brickbots/PiFinder/docs/source/index.rst

PiFinder™ Welcome
==================
A plate solving telescope finder based around a Raspberry PI, Camera, and custom UI 'hat'

For an overview of what the PiFinder is and how it came to be visit the official project website at `PiFinder.io <https://www.pifinder.io/>`_

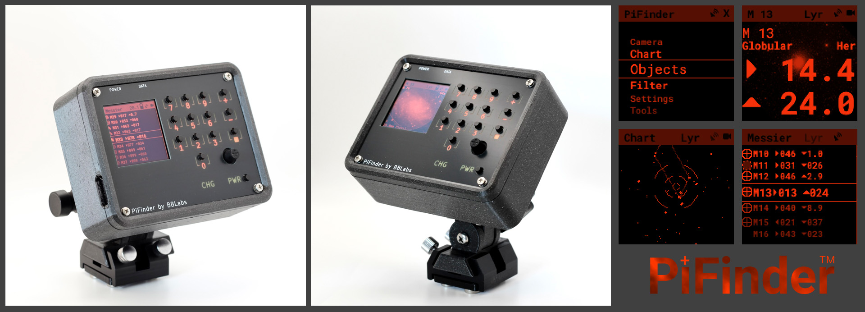
[picture p70: docs/source/images/PiFinder_rev4_banner.jpg]


.. note::
   This documentation covers rev4, v3 and v2.5 PiFinders running software |min_software| or
   above.  Not sure which you have?  See
   :ref:`Which PiFinder do I have? <quick_start:which pifinder do i have?>` in the Quick
   Start.

   Pages describe rev4 and note the v3 and v2.5 differences underneath.  |v3_docs|

   If you need docs for a previous version please choose `1.x.x <https://pifinder.readthedocs.io/en/v1.11.2/index.html>`_
   , `2.0.x <https://pifinder.readthedocs.io/en/v2.0.4/index.html>`_
   or `2.1.x <https://pifinder.readthedocs.io/en/v2.1.1/index.html>`_

* If you are new to the PiFinder, you probably want the :doc:`quick_start`
* Want to build your own?  Check out the :doc:`build_guide`
* Just bought and upgrade kit for your v2 PiFinder?  Here's the :doc:`v25_upgrade`

About
-------

The PiFinder is my attempt to improve my time at my telescope.  I don't get nearly enough of it and I want to enjoy it as much as possible.  So after years of observing with paper charts and, later, a Nexus DSC here is what I felt I was missing:

* **Reliable telescope positioning:**  The Nexus DSC is great, but my telescope just isn't built for solid encoder integration.  The slop in the way I have to couple the encoders means poor pointing accuracy.
* **Easy setup:**  The Nexus DSC needs multi-star alignment to understand how the encoders map to the sky.  The process is not terrible, but I'd like to avoid it.
* **Good push-to functionality**:  This is one place the Nexus DSC shines... if it's well aligned.  The catalog system is okay, and once you select and object the screen is clear and helpful to get the telescope pointed correctly.
* **Observation logging**:  I like to keep track of what I see each night.  I don't often sketch, just record what I saw when, with what eyepiece and some basic info about the experience.  If I could do this right at the eyepiece, that'd save time.

My hope is that other people will find this combination of functionality useful, will build their own PiFinder and help the whole project improve by making suggestions and potentially contributing to the software.  It's a pretty easy build with off the shelf parts and beginner friendly soldering.  

Features
--------

* Zero setup: Just turn it on and point it at the sky!  
* Accurate pointing: Onboard GPS determines location and time while the camera determines where the telescope is pointing.  Inertial Measurement Unit tracks telescope motion and updates sky position between camera solves
* Self-contained:  Includes catalog search/filtering, sky/object charting, push-to guidance and logging all via the screen and keypad on the unit.
* Dark site friendly:  Red OLED screen and soft backlit keys have wide brightness adjustment, right down to 'off'. No need for bright cell phones or tablets
* Easy access: Can be mounted by the eyepiece just like a finder.
* Wifi Access Point / SkySafari Integration:  The PiFinder can act as a WIFI access point to connect your tablet or phone to sync SkySafari or other planetarium software with your telescope.

Build Your Own
--------------
The PiFinder is fully open-source hardware and software.  You can order PCB's and 3d print the case with the files in this repo and order all the parts from the :doc:`Parts List <BOM>`

If you would like pre-assembled units, kits or other items to jump start your PiFinder journey, visit `PiFinder.io <https://www.pifinder.io/>`_ to see what's available and place an order.



If you'd like to learn more about how it works, and potentially build your own, everything you need should be here.  I recommend starting with the :doc:`User Manual <user_guide>` and then checking out the :doc:`Build Guide <build_guide>`.

Discord
-------
Join the `PiFinder Discord server <https://discord.gg/Nk5fHcAtWD>`_ for support with your build, usage questions, and suggestions for improvement.

.. toctree::
   :hidden:
   :maxdepth: 2

   self

.. toctree::
   :hidden:
   :maxdepth: 2
   :caption: Using your PiFinder

   quick_start
   user_guide
   menu_map
   equipment
   sqm
   catalogs
   connectivity
   skysafari
   troubleshooting

.. toctree::
   :hidden:
   :maxdepth: 2
   :caption: Building & upgrading

   build_guide
   BOM
   software
   sd_card
   v25_upgrade

.. toctree::
   :hidden:
   :maxdepth: 2
   :caption: For developers

   dev_guide
   dev_arch
   api
