brickbots/PiFinder/case/adapters/dovetail_meade_lxd.md

## PiFinder Dovetail for Meade LXD shoe

Contributed by: John Purdy

This part replaces the bottom half of the standard Vixen/Synta foot
shoe with a profile that mates with the Meade LXD shoe.  
Print with bottom of the dovetail on the plate, may require supports for side profile overhangs.
