brickbots/PiFinder/docs/ax/sqm/CONTEXT.md

# SQM (Sky Quality Meter)

Canonical language for PiFinder's solve-independent sky-brightness measurement.
The architecture and validation evidence live in [`../sqm.md`](../sqm.md).

## Product intent

**Zero-touch SQM**:
Normal operation selects the built-in profile from the detected sensor and
starts measuring without flats, darks, or a calibration file. Optional Correct
and Calibration flows refine a unit or session; they do not establish basic
functionality.

**SQM**:
The published PiFinder sky surface brightness in mag/arcsec². Higher means a
darker sky. It is empirically calibrated to an SQM-L scale but is not claimed
to have an identical spectral or angular response.

**`SQMState`**:
Latest published `value`, `source`, and `last_update` in shared state. The UI
reads this state and does not calculate photometry.

**Radiometric SQM**:
The published factory-calibration measurement from diffuse raw background,
exposure, pedestal, factory field width, and the effective radiometric zero
point. On bare sensors that zero point is not a constant — it moves with
measured **sky colour** (see *Radiometric colour term*). Avoid calling it the
"fixed-calibration" value; the calibration is fixed per sensor, the zero point
applied to a given frame is not.

**Stellar SQM (`sqm_star_calibrated`)**:
The former per-frame stellar-zero-point result. Retained as a transmission and
regression diagnostic; never the production primary or no-solve fallback.

**`sqm_altitude_corrected`**:
Optional comparison value `sqm_final + 0.28 × (airmass − 1)`. It is present
only when a real field altitude is known. It is never the primary reading.

## Images and coordinates

**Solve image**:
The processed 512×512 image used by Cedar and tetra3. It can be display-rotated.

**Raw photometry image**:
The linear cropped raw mono frame, or the mean of both Bayer-green sites. Star
flux and sky background are measured here, not on the processed solve image.
Always the **crop**, never the full-sensor frame that exposure sweeps archive —
see [Camera](../camera/CONTEXT.md) for the two extents. The margins are
vignetted with no optical black, so measuring them would bias the sky
background and break continuity with every calibrated sweep.

**Derotation**:
Mapping solve-image `(y, x)` centroids back to the orientation of the stored
raw frame using `solve_image_rotation`. Required before raw photometry.

**Centroid scale**:
Raw-photometry side length divided by 512. Both matched and all-detected
centroids must be scaled by it before use on the raw image.

## Stellar photometry

**Aperture**:
Circular radius-5-pixel region whose sky-subtracted sum is stellar flux.

**Annulus**:
The local sky ring from radius 10 through 18 pixels. Radius 10 is wing-safe on
the archive; the former 6–14 ring was contaminated by HQ PSF wings.

**Detected-source exclusion**:
Every Cedar centroid is masked out of every relevant annulus with an
aperture-radius disk. A 3σ clip catches unreported sources.

**Saturation threshold**:
`0.70 × (2^bit_depth − 1)` on raw photometry. The conservative limit rejects
stars in the sensor's nonlinear shoulder before hard clipping.

**Reference magnitude**:
Bare sensors use Gaia G with a BP−RP trim. HQ uses Hipparcos/Johnson V because
its factory IR-cut passband is closer to V. Missing Gaia data falls back to V.

**Fixed magnitude band**:
Catalog magnitudes 3.5–6.5. When at least five stars are available, only this
population votes on the frame zero point, preventing exposure-dependent
population drift.

**Photometric zero point (`mzero`)**:
Median of `reference_mag + 2.5 log10(star_flux)` over the selected population,
after a 3-MAD outlier rejection. Readings outside the fixed magnitude band do
not vote merely because a longer exposure detects them.

**MAD rejection**:
Three robust standard deviations (`1.4826 × MAD`) around the selected
population's median. Removes isolated catalog, colour, blend, or residual
nonlinearity failures; it does not replace the magnitude band.

**Wing correction (`mzero_correction`)**:
Rolling additive `−2.5 log10(f)`, where `f` is the aperture's enclosed stellar
flux fraction measured from a median-stacked curve of growth.

**`WingEstimator`**:
Conditions on several frames of bright unsaturated stars. Returns zero before
conditioning and naturally converges to zero for wingless optics. Do not
replace it with a per-star wing-boundary search; that approach integrated sky
noise and invented missing flux.

## Sky and detector model

**Local sky**:
Median cleaned annulus value for one matched star.

**Radiometer sample**:
Sparse central median reduced in the camera process on every raw frame. It
excludes the outer ten percent and records MAD, quadrant gradient, exposure,
timestamp, sequence, and native green/mono pixel scale.

**Stellar sky background**:
Median of local annulus skies, used only by stellar diagnostics.

**Bias offset**:
Static mean detector signal at minimum exposure, in raw ADU. Comes from the
built-in sensor profile unless an optional per-device calibration overrides it.
Static is the operative word: it is a stored constant, and a **tracked black
level** supersedes it when one is available.

**Tracked black level (`BlackLevelTracker`)**:
The sensor's actual pedestal right now, fitted as the intercept of sky
background against exposure over the running session. The optical-black clamp
moves with sensor state, so this measurement supersedes both the profile
constant and any wizard-measured bias offset once its fit is **leased**. It
needs no lens cap and no dark frame. Say "tracked black level", not "auto
bias" or "dynamic calibration" — it measures one specific quantity and does
not calibrate anything else. See
[ADR 0028](../../adr/0028-tracked-black-level-supersedes-stored-bias.md).

**Lease**:
The gate that decides whether a tracked black level is trusted enough to
publish, based on the fit's standard error and deviation band. Unleased, the
pedestal falls back to the stored constant. A tracker holding samples is not
the same as a tracker whose fit is leased.

**Mean dark signal**:
`calibrated_dark_current_rate × exposure_seconds`. A mean exposure-dependent
signal, not an RMS noise term. Factory profile rates are unverified engineering
estimates and remain diagnostic until optional per-device calibration measures
the rate.

**Pedestal**:
The mean detector signal subtracted from sky background. Its bias term is the
**tracked black level** when one is leased, otherwise `bias_offset`. An
optional measured calibration adds `mean_dark_signal` on top of that bias term.
An explicit total `pedestal_override` wins over all of it.

**Read noise**:
Zero-mean RMS variation in raw ADU. Diagnostic uncertainty; never subtracted
from sky signal.

**Unresolved background**:
Sky background no more than 1 ADU above the pedestal. SQM returns no new value
with `background_not_resolved_above_pedestal`; it does not clamp.

**`NoiseFloorEstimator`**:
Owner of one copied, optionally calibrated camera profile. Reports
the applied `pedestal + read_noise` as a raw-ADU operational threshold and
retains low image percentiles and the unapplied factory dark-current model only
for diagnostics. It cannot infer a dark calibration from ordinary sky images.

**Shared camera noise floor**:
The camera's exposure controller operates on processed 8-bit pixels. A raw-ADU
SQM threshold must not be published into it; the units differ.

**`CameraProfile`**:
Per-sensor hardware, detector, catalog-band, colour, and SQM offset constants.
`get_camera_profile()` returns a copy so optional calibration never mutates
global defaults or another calculator.

**Radiometric zero point**:
Exposure-normalized diffuse-sky conversion already mapped to the SQM-L scale.
It is fixed per shipped sensor/optics profile and does not change with current
stellar transmission.

**Radiometric field width**:
Angular width used for square-arcsecond conversion when no solve exists.
Derived from the **optical train** (see [Camera](../camera/CONTEXT.md)) rather
than stored per sensor: it is a property of the sensor *and* the fitted lens,
so a sensor-only constant is silently wrong the moment the lens changes. An
error here scales the assumed solid angle, and so biases every published
radiometric SQM — a lens change of one step is worth ~0.6 mag.
_Avoid_: factory field width (it is no longer a factory constant), FOV
(unqualified — see [Camera](../camera/CONTEXT.md)).

## Passband and atmosphere

**Colour coefficient**:
Per-sensor trim mapping catalog colour into the camera's stellar passband.

**SQM band offset (`sqm_band_offset`)**:
Additive mapping from sensor-band sky brightness to the reference SQM-L scale
for the calibrated sky regime, on the **stellar** path only. It is coupled to
the catalog transform, wing model, and local-annulus background estimator.
Diagnostic: the published value comes from the radiometer, not from here.

**Sky colour (`R/G`)**:
Ratio of median red to median green sky background, measured off the raw
mosaic. A *measurement of the scene*, not a sensor property — it is the
project's proxy for sky spectrum, and the thing that distinguishes a
sodium/LED-dominated light-polluted sky (green-weighted, R/G ≈ 0.83–0.89) from
a dark airglow sky (grey and NIR-rich, R/G ≈ 1.00–1.04). Say "sky colour" or
"R/G", not "colour temperature" or "white balance" — neither is what this is.

**Radiometric colour term (`radiometric_colour_slope` / `_pivot` / `_range`)**:
Sky-colour dependence of the radiometric zero point, in mag per unit R/G. It
exists because the sensor-band to V-band conversion depends on the sky's
spectrum, which a single constant cannot represent across regimes. Slope `0`
means a plain constant, which is correct for mono sensors and for IR-cut
sensors with no NIR leak. R/G is clamped to `_range` rather than extrapolated.
Distinct from **colour coefficient**, which trims *catalog star* colour on the
stellar path; this one trims *sky* colour on the radiometric path. See ADR 0026.

**Mosaic phase**:
The property that pixel `(0, 0)` of the frame reaching photometry is still a
red CFA site. Rotation by 180° and odd crop origins both break it while leaving
the green sites unchanged, so the colour term checks it and reports no colour
rather than blue-as-red.

**Airmass / altitude correction**:
Pickering (2002) airmass and `0.28 mag/airmass`. Comparison-only; unknown
altitude is `None`, never a fabricated 90°.

**Transmission deficit / cloud flag**:
Deficit of exposure-normalized stellar zero point relative to clear
transmission. Cloud is diagnostic and does not alter scene brightness.

**Optics attenuation correction**:
Recent stellar deficit classified as dew/dirty optics and subtracted from the
radiometric magnitude. It requires a session-conditioned clear baseline;
factory priors alone cannot activate it.

## Optional refinement

**SQM Correct** (removed 2026-07-18):
The former user-entered session offset against a reference meter. Removed: a
magnitude-additive knob silently absorbs ADU-space (brightness-dependent)
errors such as pedestal bias, masking the fault instead of fixing it. The
reference comparison lives on as data: a SWEEP run with a reference reading
records the difference in its metadata.

**Calibration JSON**:
Optional `~/PiFinder_data/sqm_calibration_<sensor>.json` override containing
bias, read noise, and dark-current rate. Absence is the normal zero-touch case.
Of the three fields the dark-current rate is the one that still changes the
published value: bias yields to a leased **tracked black level**, and read
noise is diagnostic.

**Calibration wizard**:
Optional service flow. Captures minimum-exposure bias frames, fits temporal
read noise and multi-exposure dark signal, optionally validates against exact
timestamp-paired sky solves, saves JSON, and sends typed
`ReloadSqmCalibration`. It does not produce or require flats or master darks.

**Zero-second request**:
An estimator capability for an explicitly managed caller. Disabled in normal
SQM because no runtime camera path services the request.

## Timing and distribution

**`SQM_CALCULATION_INTERVAL_SECONDS`**:
One-second minimum interval between new-frame-driven radiometric publications.
Camera-side radiometer collection runs on every captured frame. Sleep mode does
not publish without its normal periodic capture.

**`SQM_STELLAR_DIAGNOSTIC_INTERVAL_SECONDS`**:
Ten-second minimum interval between expensive solved stellar transmission
diagnostics.

**`ReloadSqmCalibration`**:
Typed solver command that discards the calculator and resets wing/cloud
history; the next solve reconstructs it from detected sensor plus optional
calibration JSON.

**Per-star arrays**:
Large diagnostic fields (`star_centroids`, `star_mags`, `star_fluxes`, local
backgrounds, individual mzeros). Removed before publishing shared details.

## Avoid these ambiguous phrases

- “Processed SQM pipeline” — production photometry is raw; only solving uses
  the processed image.
- “Needs calibration” — factory profiles are the normal path; qualify an
  optional per-device or session refinement.
- “Dark frame required” or “flat required” — neither is required in normal
  operation.
- “Corrected SQM” — say session-corrected, altitude-comparison, cloud estimate,
  or passband-mapped.
- “Adaptive dark calibration” — ordinary sky percentiles contain sky signal
  and are diagnostic only.
