brickbots/PiFinder/docs/source/includes/camera_cable_connect.rst

.. Shared between build_guide.rst (Assembly) and v25_upgrade.rst (Installing the
   Camera). Each page supplies its own lead-in sentence, then includes this file.

Open the connector all the way by sliding the dark-grey clip away from the PCB. Be gentle.
Too much force can break this clip.

With the connector open, slide the cable in gently and keep it aligned. Take your time and
watch the dark-grey clip. It should stay open while you slide the cable in. If it closes,
open it again so the cable goes all the way in.

When the cable is seated, slide the dark-grey clip shut. This can take a little force.
Check the photo below if you are unsure.

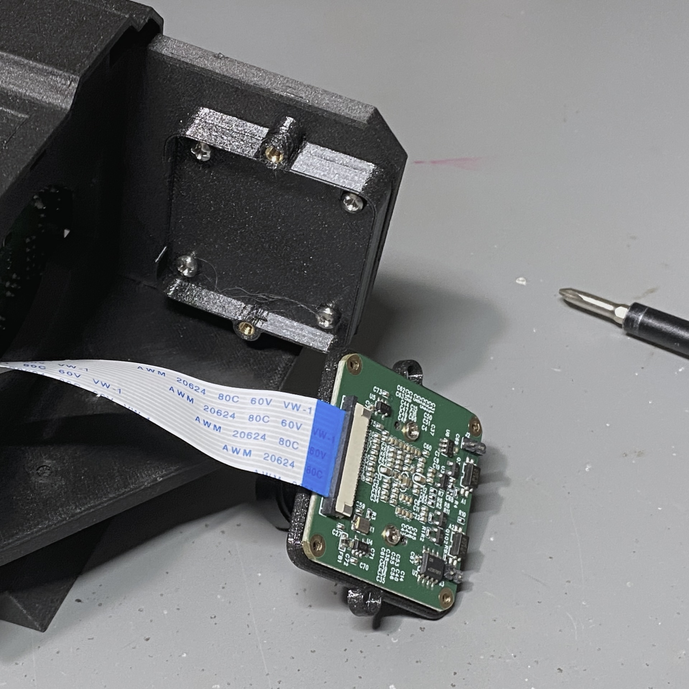
[picture p90: docs/source/images/v25_upgrade/v25_upgrade_24.jpeg]


Place the camera in the adapter and secure it with the two new screws. They match the
other four, so it does not matter if they get mixed up.

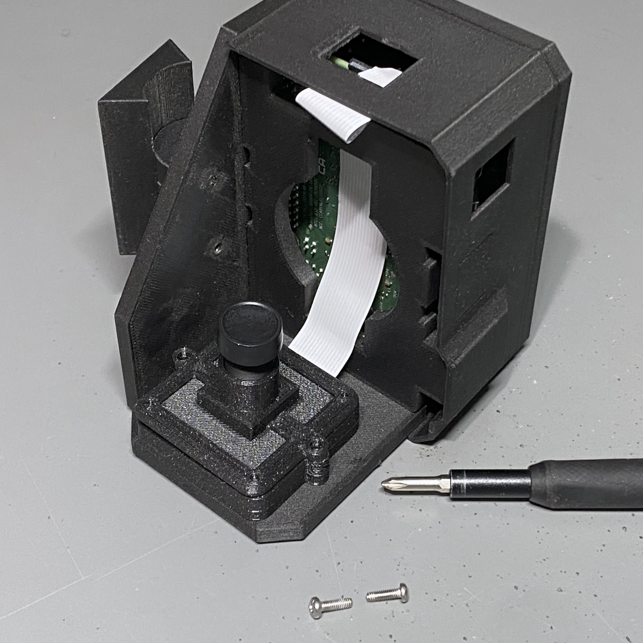
[picture p91: docs/source/images/v25_upgrade/v25_upgrade_25.jpeg]


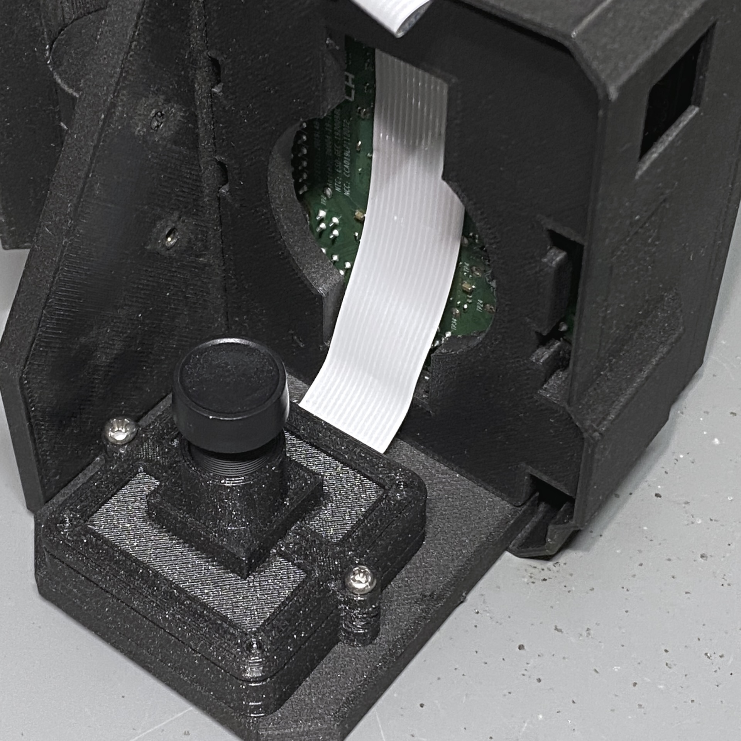
[picture p92: docs/source/images/v25_upgrade/v25_upgrade_26.jpeg]
