brickbots/PiFinder/docs/source/includes/camera_prep.rst

.. Shared between build_guide.rst and v25_upgrade.rst (Camera Prep). Each page
   supplies its own heading and lead-in sentence, then includes this file.

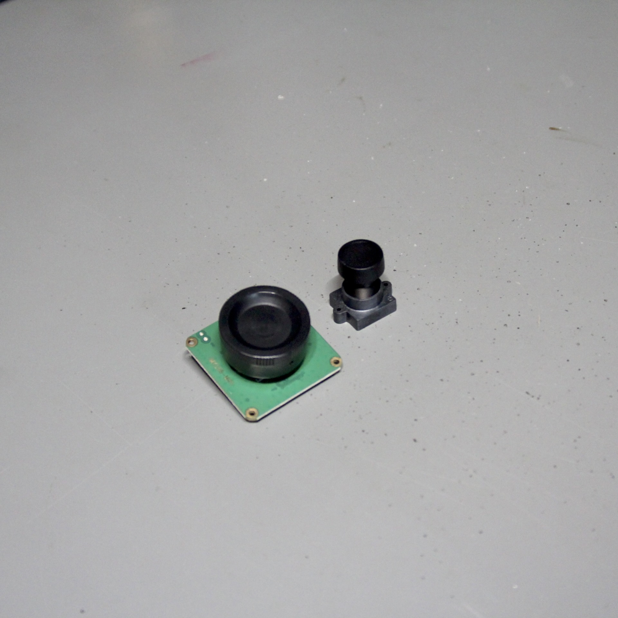
[picture p93: docs/source/images/v25_upgrade/v25_upgrade_11.jpeg]


If your camera has pin headers, clip them as close to the PCB as you reasonably can. To get closer to
the PCB, you can pull the black plastic part off with pliers, or cut through it. Take care not to
clip any surrounding components.

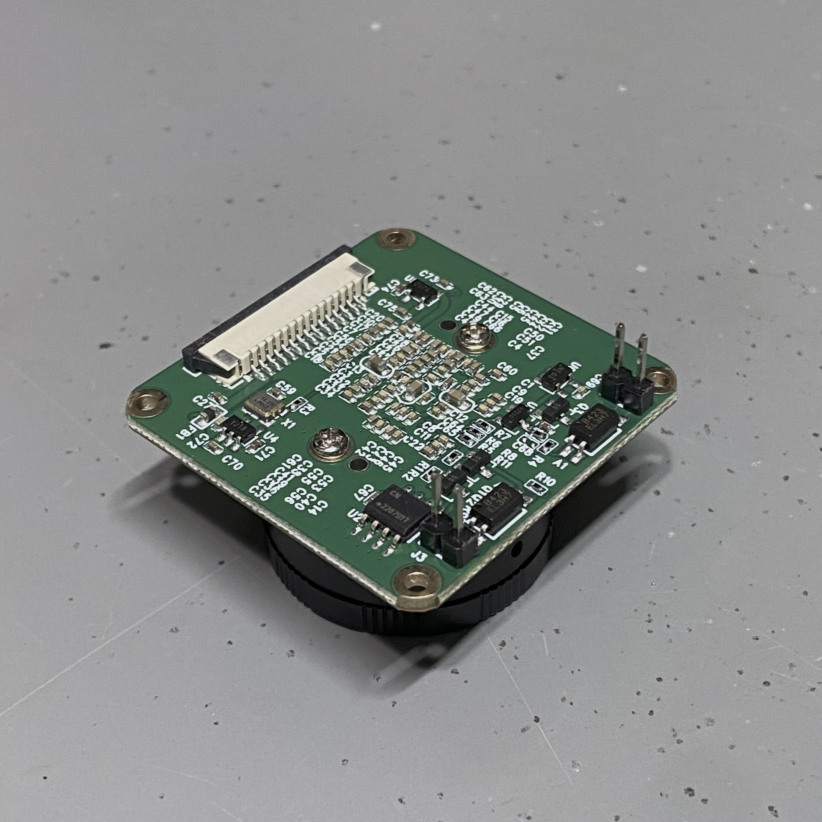
[picture p94: docs/source/images/v25_upgrade/v25_upgrade_12.jpeg]


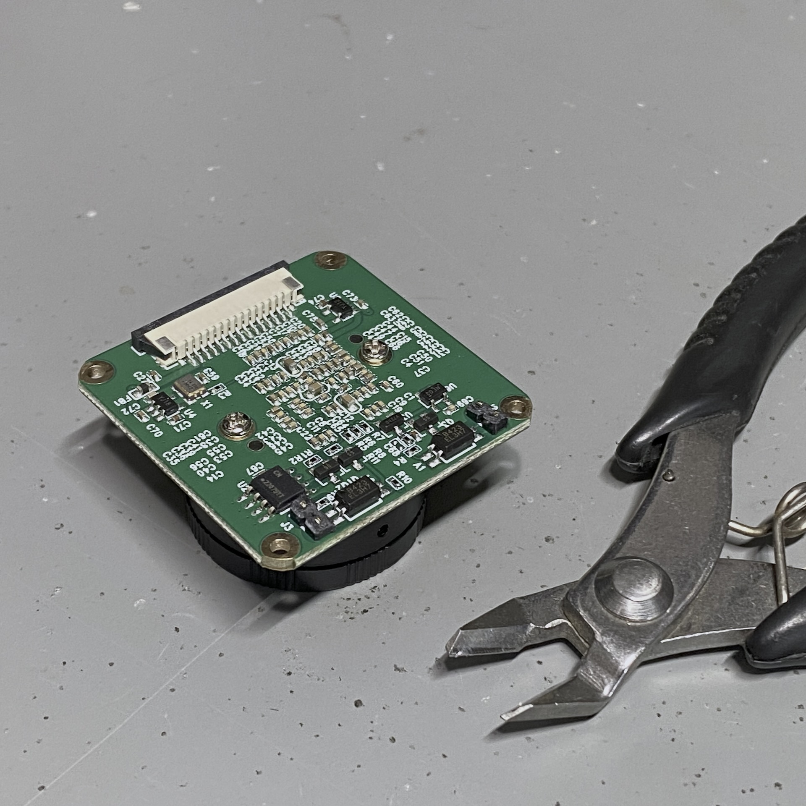
[picture p95: docs/source/images/v25_upgrade/v25_upgrade_13.jpeg]


Look through the lens holder to confirm it is clear of obstructions.

Place the lens holder on the table, large side up, as shown in the photo below. Its two
screw tabs must stick out on the sides opposite the cream-white and dark-grey cable
connector on the PCB.

Remove the two screws near the center of the green PCB (yours might be black). Lift the
PCB gently onto the new lens holder.

Take care with the sensor surface on the underside of the PCB. It should sit neatly in the
square recess of the lens holder. Refit the same two screws to fasten the PCB to the lens
holder. The screws cut their own threads, but the holes help you start them. Tighten them
until nothing moves.

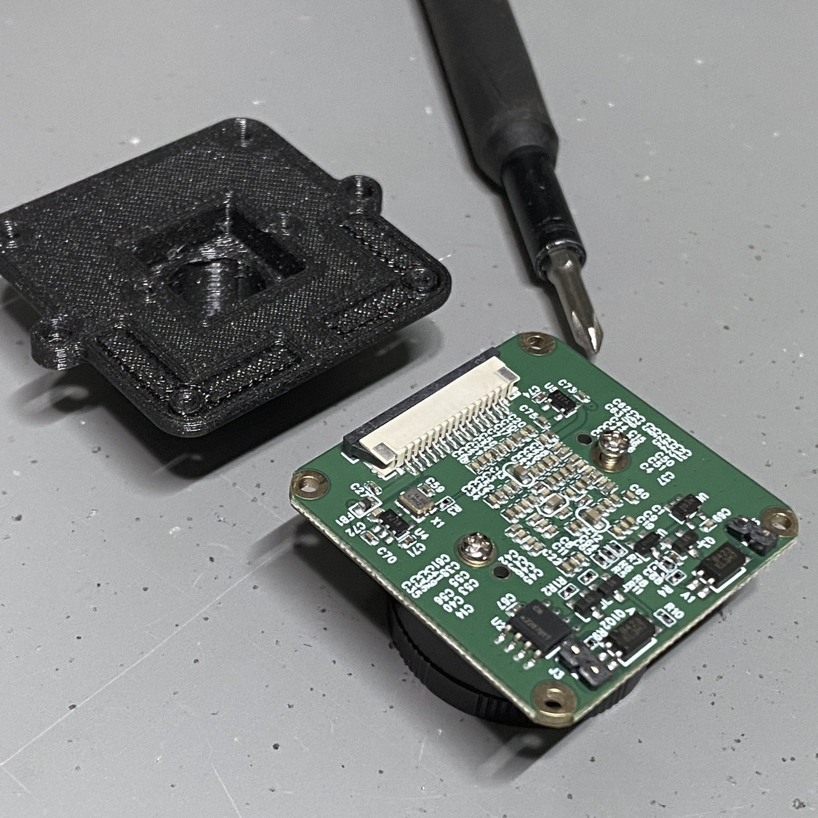
[picture p96: docs/source/images/v25_upgrade/v25_upgrade_14.jpeg]


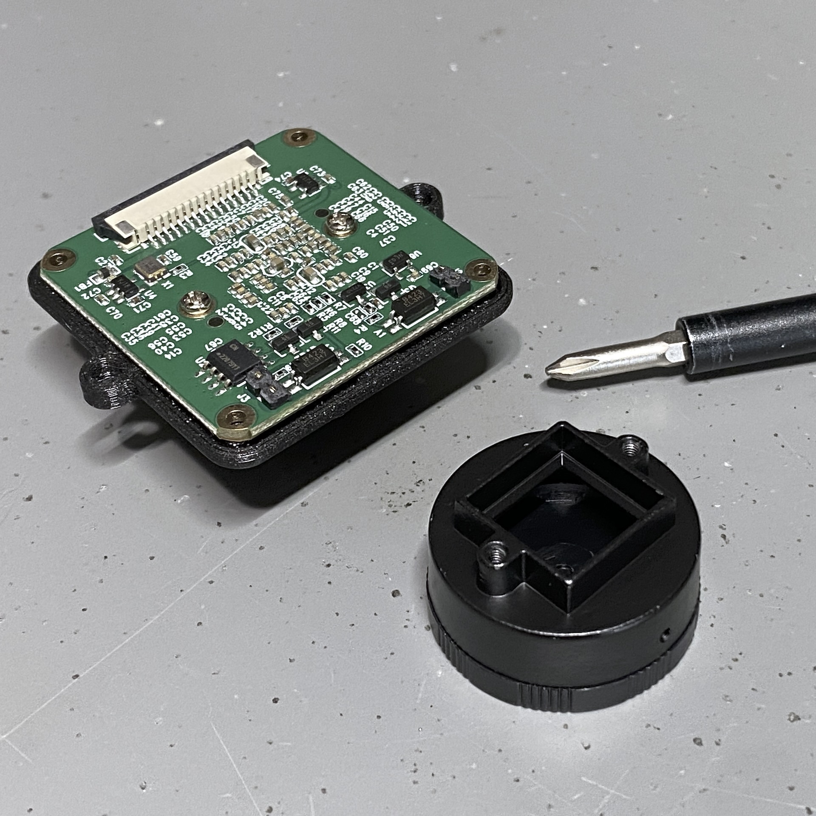
[picture p97: docs/source/images/v25_upgrade/v25_upgrade_15.jpeg]


Flip the camera assembly over and thread the lens in slowly. With gentle force it slides
in a few mm, aligns, then stops. When it stops, check that it sits straight, then screw it
into place.

For a rough focus, leave a 6mm gap (pictured below) between the top of the lens holder and
the bottom of the lip on the lens. It does not need to be exact. You set the final focus
under the stars.

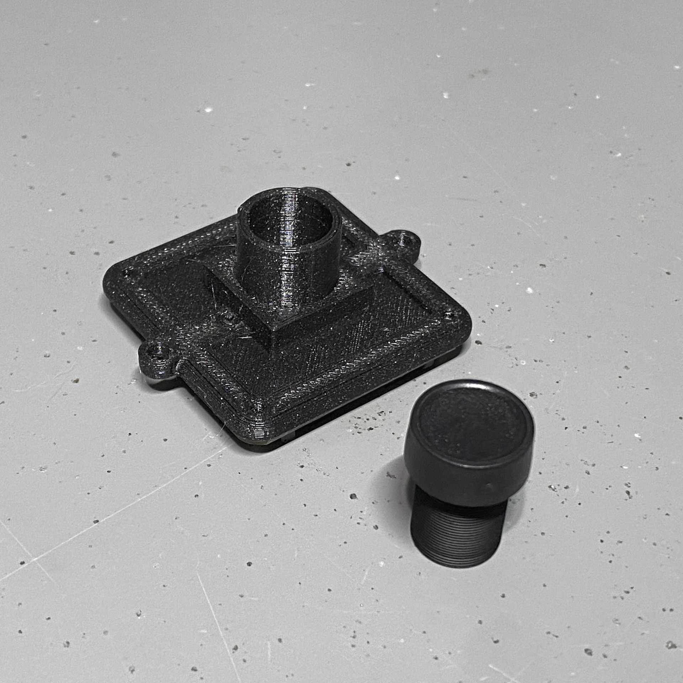
[picture p98: docs/source/images/v25_upgrade/v25_upgrade_16.jpeg]


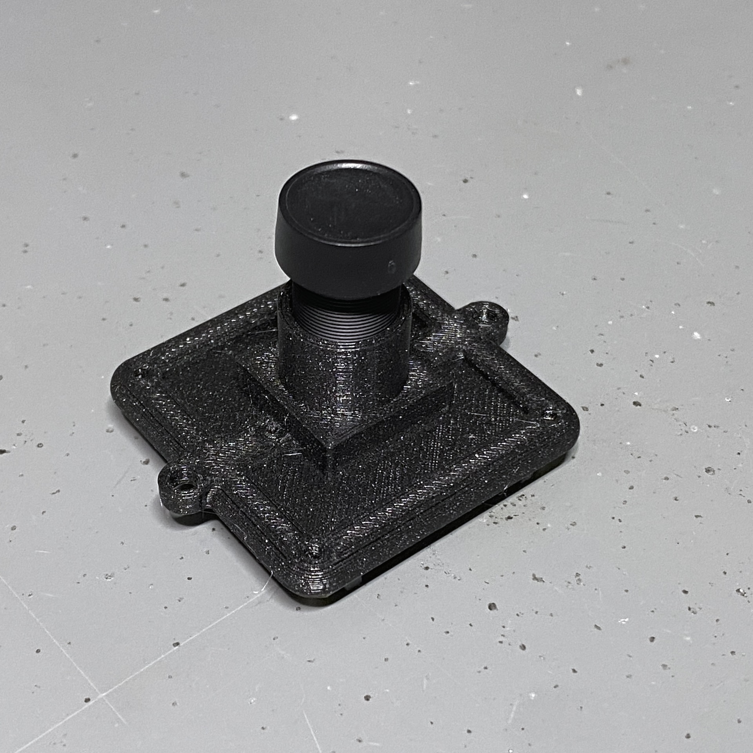
[picture p99: docs/source/images/v25_upgrade/v25_upgrade_17.jpeg]
