brickbots/PiFinder/docs/adr/0005-focus-hfd-self-contained-in-ui.md

# Focus-quality indicator: self-contained HFD measured in the UI

The focus screen (`UIPreview`) measures focus quality with **Half-Flux Diameter (HFD)** — the diameter enclosing half a star's background-subtracted flux — computed by its **own lightweight star detector** running in the main process on the raw 512×512 frame, deliberately tuned to accept broad, defocused blobs (up to a ~50 px HFD measurement cap). It does **not** reuse the solver's tetra3/Cedar centroids or SQM's photometry. The driving reason: a badly defocused frame **does not plate-solve**, so solver-derived stars (and SQM, which only runs on successful solves) vanish at exactly the moment focus help is needed most. A self-contained detector is the only source of focus feedback that works across the entire defocus range, including the donut phase at the start of a focus sweep. The math lives in a pure `focus.py` module (no UI/PIL deps) so it is unit-testable against synthetic blobs of known width; `UIPreview` owns only raw crop rendering.

## Considered Options

- **Reuse the solver's matched centroids via `shared_state`.** Rejected: matched-centroid count goes to zero when defocused. Focus guidance would go blind precisely when the image is most out of focus — the worst possible failure mode for the feature.
- **Open a second Cedar gRPC client from the UI.** Rejected: Cedar is tuned to *reject* fuzzy/large blobs (`max_size=10`, `sigma=8`) to find tight stars for solving, so it returns little or nothing on a defocused donut. Wrong tool for the defocused regime, and it adds cross-process coupling to the UI.
- **Share/refactor SQM's `_measure_star_flux_with_local_background` patch geometry.** Rejected: SQM is a different bounded context, runs in the solver process, is gated to once per 5 s on successful solves, and is photometry-tuned. The genuine overlap is ~15 lines of generic numpy patch math carrying no domain meaning; duplicating it keeps the two contexts decoupled and lets each evolve independently. SQM does not detect stars at all, so there is no "two competing star-finders" concern.
- **FWHM instead of HFD.** Rejected as the primary focus metric: FWHM assumes a Gaussian-ish PSF and breaks on saturated cores and broad/donut defocus — the exact shapes seen across a focus sweep. HFD stays stable and monotonic over the full range. The statistics display may show an area-equivalent FWHM estimate as supplementary information, clearly labelled and never substituted for HFD.
- **Report HFD in arcseconds.** Rejected: the PiFinder's ~10.2° / 512 px optics give ~72 arcsec/px, so an in-focus star would read as ~70–215 arcsec — ~30× worse than the 2–4 arcsec users expect from imaging-rig FWHM, inviting false alarm and false comparison. Pixels are the honest native unit, and only the *relative* trend matters for finding best focus.

## Consequences

- A second, intentional star-finder exists in the codebase, tuned opposite to Cedar (accept blobs rather than reject them). This is deliberate, not an oversight or a missed reuse opportunity.
- HFD is always computed on the **raw** frame. The four visual star tiles also preserve raw luminance: crop, nearest-neighbour enlargement, and the panel's red/grey channel mask are the only display operations. There is no contrast stretch, denoising, sharpening, blur, or interpolating resize.
- The four brightest detected blobs anywhere in the camera frame are repacked into the four display quadrants to use the small screen efficiently. Their relative image-space pattern is tracked under shared translation, preserving each surviving star's slot through global image motion and brightness-order changes; missing stars are replaced. HIP/catalog identity is deliberately not used because it requires a successful plate solve, while Focus must keep working before and during defocus. Compact stars use a nominal 10× enlargement relative to a full-frame preview; the crop expands around broad blobs so the effective zoom falls rather than clipping a defocused star.
- Short `SQUARE` follows the standard UI display-mode convention, cycling the four-star view, a full-screen view of the brightest star, an Image view, and focus statistics. The Image view uses the original per-frame autocontrast for display only; measurement, the star crops, and the Stats histogram remain raw. Single uses twice the apparent magnification of Stars while retaining adaptive crop expansion for broad blobs. In the four-star view the rolling 10-second HFD signal is split around the center readout; in the brightest-star view both sit on a translucent lower-third overlay so the raw star remains visible beneath them. The gap follows the actual glyph bounds so its visual padding is equal on both sides. Unavailable HFD is always `?.?`; no upper-limit sentinel is displayed. The recent signal range is centered on the readout with lower values below; this deliberately avoids claiming a universal good-focus HFD across different optics. No guide, marker, or under-stroke accompanies the signal. The statistics page includes HFD, supplementary FWHM, detected count, exposure mode/value, gain, and a log-scaled histogram of the raw frame.
- The indicator works without any plate solve, so the focus screen is useful before the system has ever solved.
- Companion glossary: [`docs/ax/ui/CONTEXT.md`](../ax/ui/CONTEXT.md) (Focus indicator section).
