brickbots/PiFinder/images/hardware_overview.png

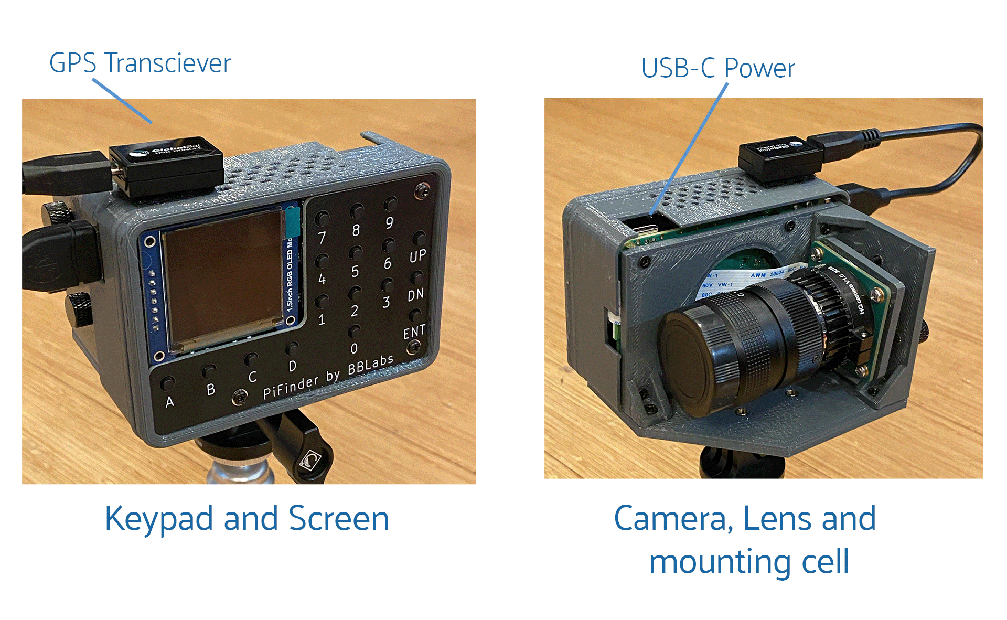
images/hardware_overview.png
