brickbots/PiFinder/case/accessories/tube_shoe_mount_38mm_bottom.stl

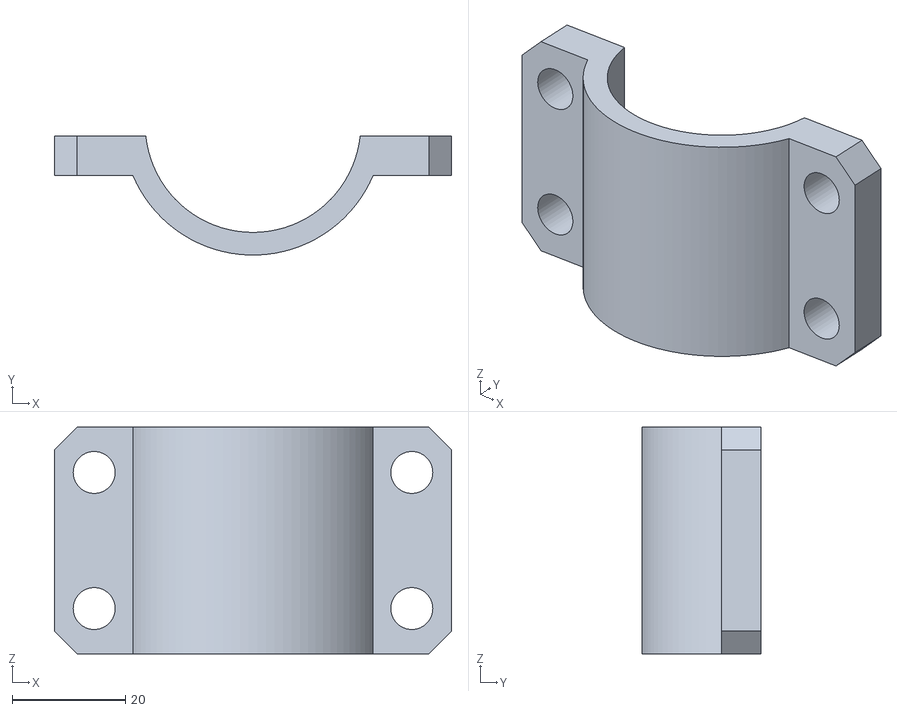
[picture p129: CAD file, 2025-09-29]
case/accessories/tube_shoe_mount_38mm_bottom.stl
70.0 x 21.0 x 40.0
