brickbots/PiFinder/case/adapters/flat30_adapter_sidemount.stl

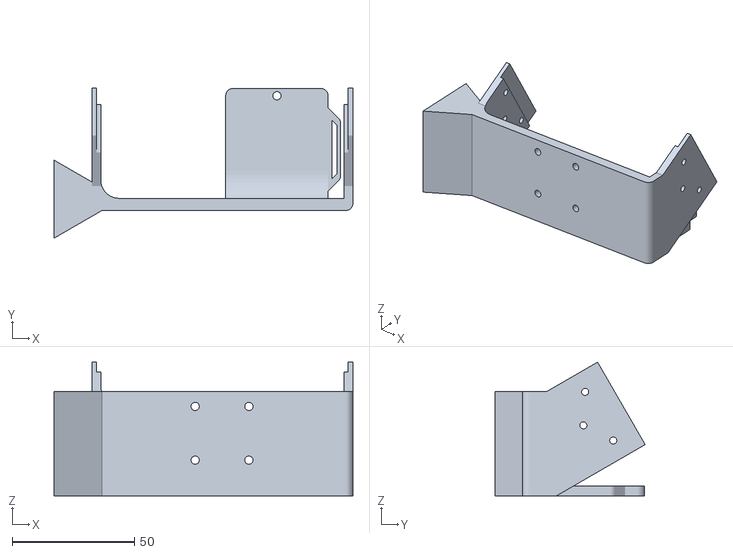
[picture p130: CAD file, 2025-02-12]
case/adapters/flat30_adapter_sidemount.stl
122.5 x 61.6 x 54.8
