brickbots/PiFinder/case/rev4/case.stl

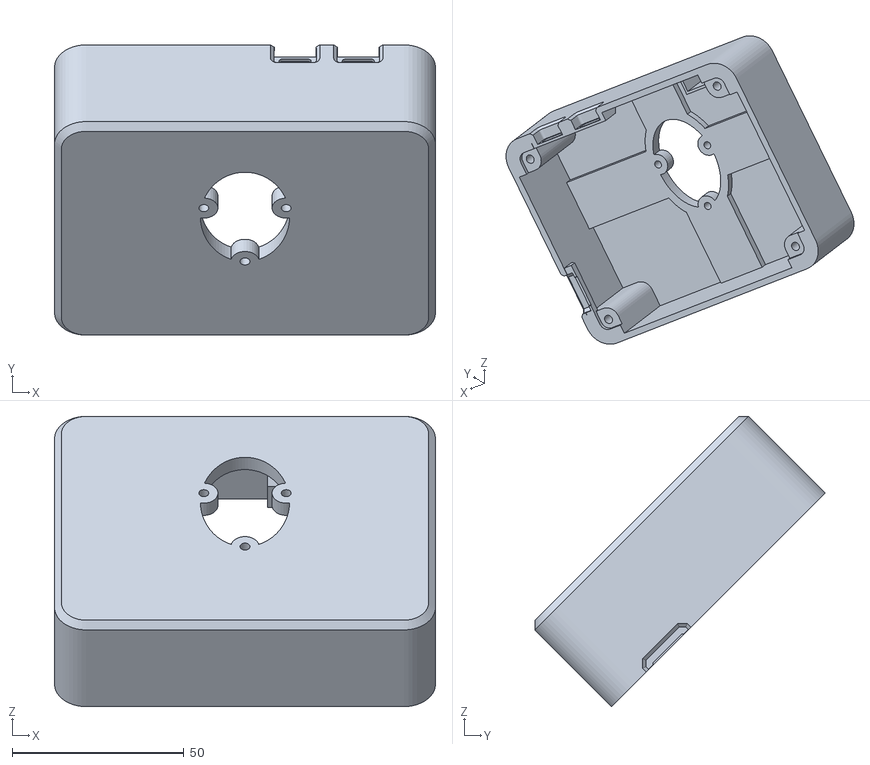
[picture p131: CAD file, 2026-08-08]
case/rev4/case.stl
111.0 x 84.6 x 84.6
