brickbots/PiFinder/case/accessories/tethered_lens_cap/Lens Cap - PETG.stl

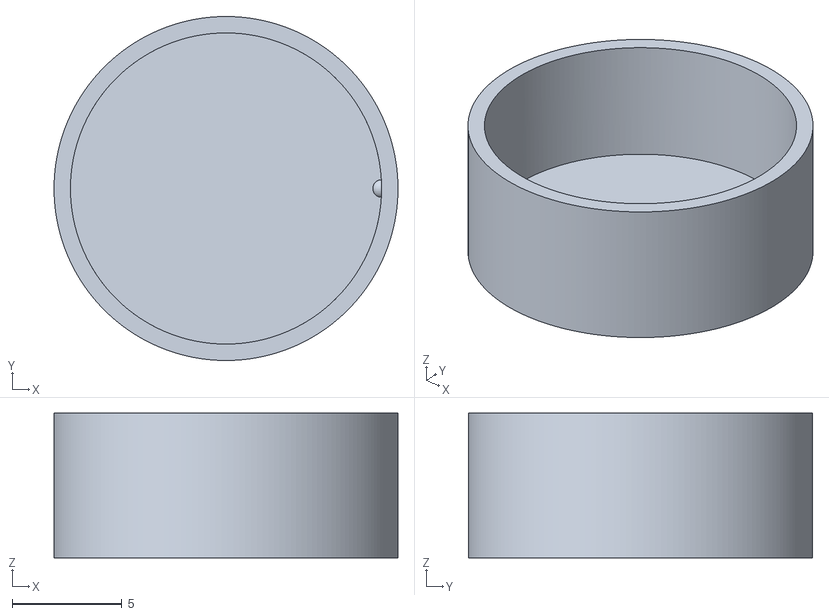
[picture p132: CAD file, 2026-07-01]
case/accessories/tethered_lens_cap/Lens Cap - PETG.stl
15.7 x 15.7 x 6.60
