brickbots/PiFinder/case/accessories/tube_shoe_mount_38mm_top.stl

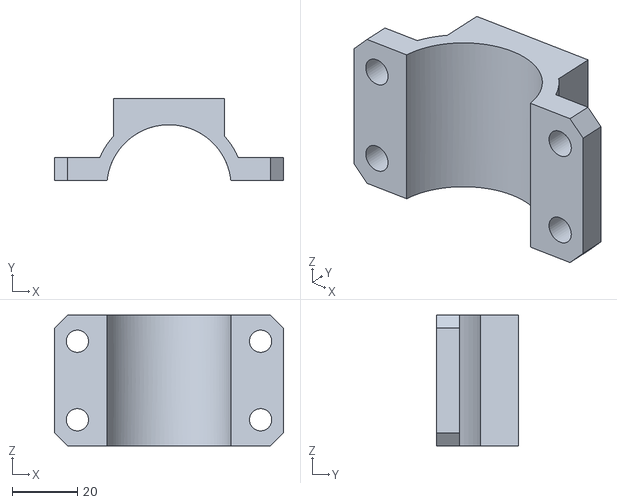
[picture p133: CAD file, 2025-09-29]
case/accessories/tube_shoe_mount_38mm_top.stl
70.0 x 25.0 x 40.0
