brickbots/PiFinder/case/adapters/dovetail_losmandy.stl

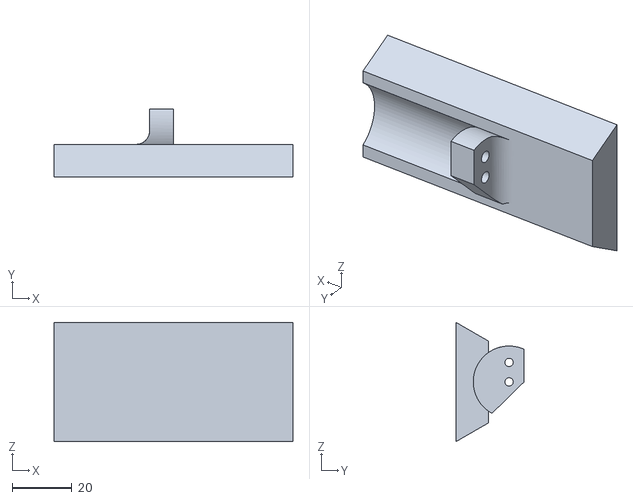
[picture p134: CAD file, 2025-02-12]
case/adapters/dovetail_losmandy.stl
80.0 x 22.9 x 40.0
