brickbots/PiFinder/case/rev4/bezel.stl

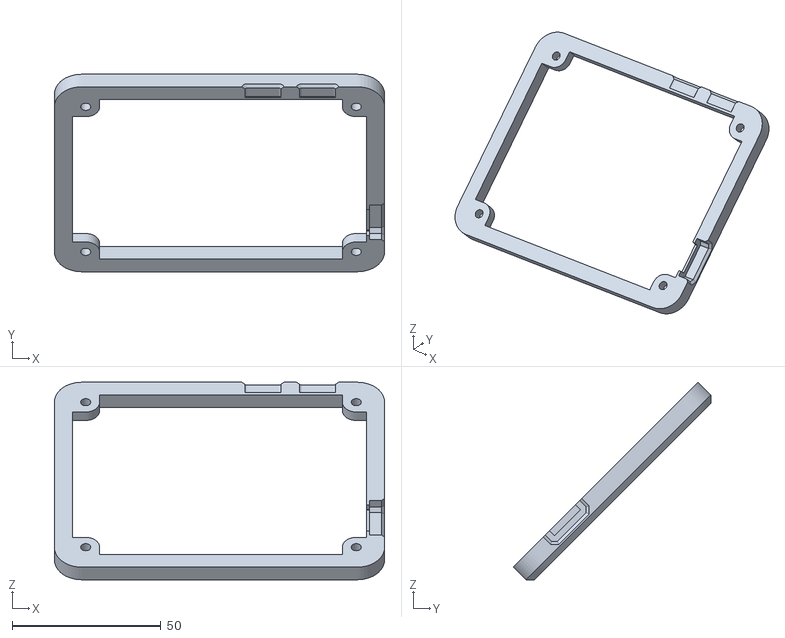
[picture p135: CAD file, 2026-08-08]
case/rev4/bezel.stl
111.0 x 66.5 x 66.5
