brickbots/PiFinder/case/accessories/tethered_lens_cap/Threaded Lens Holddown.stl

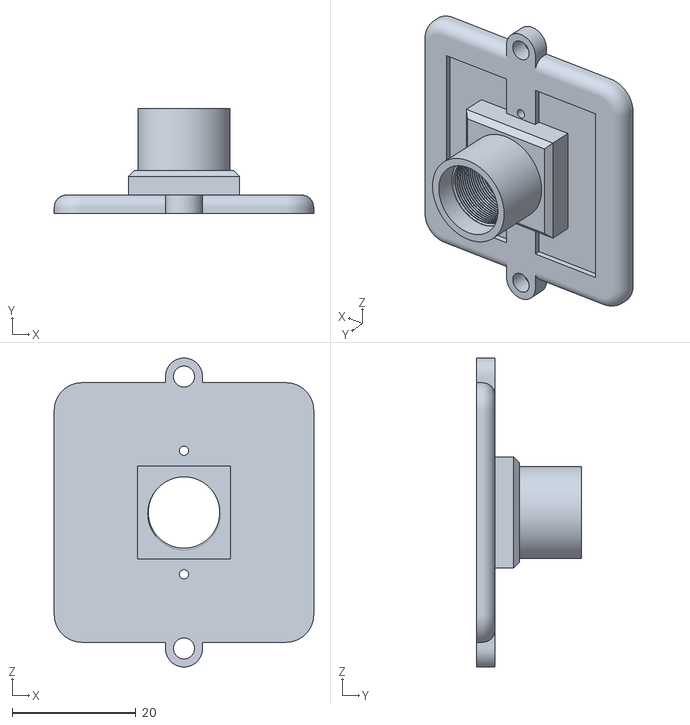
[picture p136: CAD file, 2026-07-01]
case/accessories/tethered_lens_cap/Threaded Lens Holddown.stl
42.0 x 17.0 x 50.0
