brickbots/PiFinder/case/accessories/tube_shoe_mount_30mm_bottom.stl

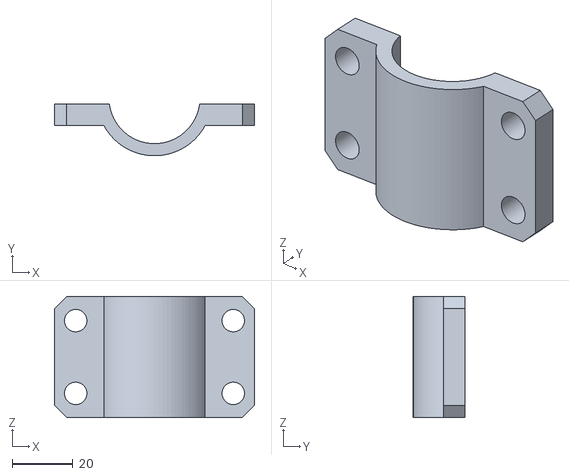
[picture p137: CAD file, 2025-09-29]
case/accessories/tube_shoe_mount_30mm_bottom.stl
66.0 x 17.0 x 40.0
