brickbots/PiFinder/case/rev4/joint_top.stl

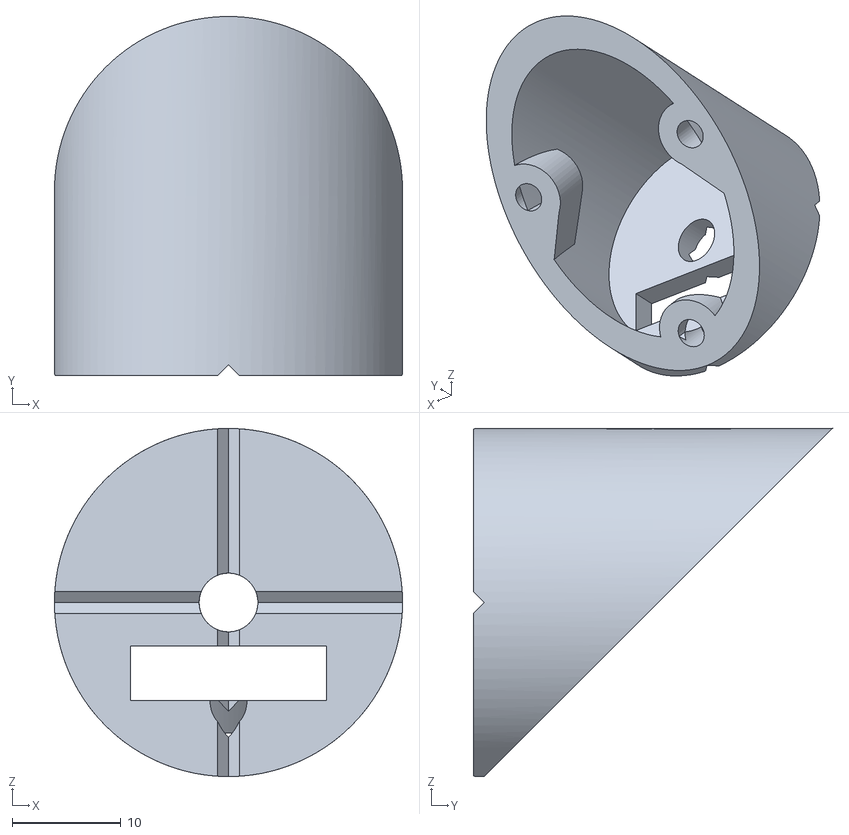
[picture p138: CAD file, 2026-08-08]
case/rev4/joint_top.stl
32.0 x 33.0 x 32.0
