brickbots/PiFinder/case/accessories/tube_shoe_mount_25mm_top.stl

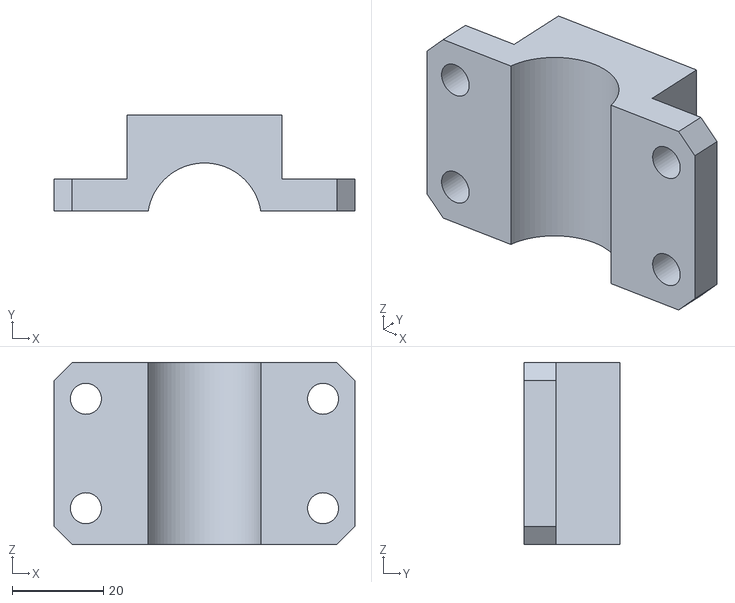
[picture p139: CAD file, 2025-09-29]
case/accessories/tube_shoe_mount_25mm_top.stl
66.0 x 21.0 x 40.0
