brickbots/PiFinder/case/rev4/joint_body.stl

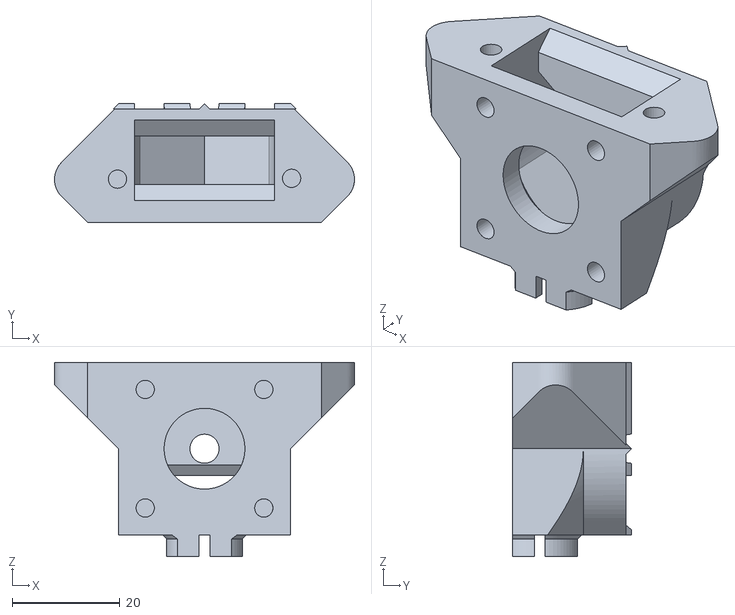
[picture p140: CAD file, 2026-08-08]
case/rev4/joint_body.stl
55.7 x 22.0 x 36.0
