brickbots/PiFinder/case/rev4/dovetail_top.stl

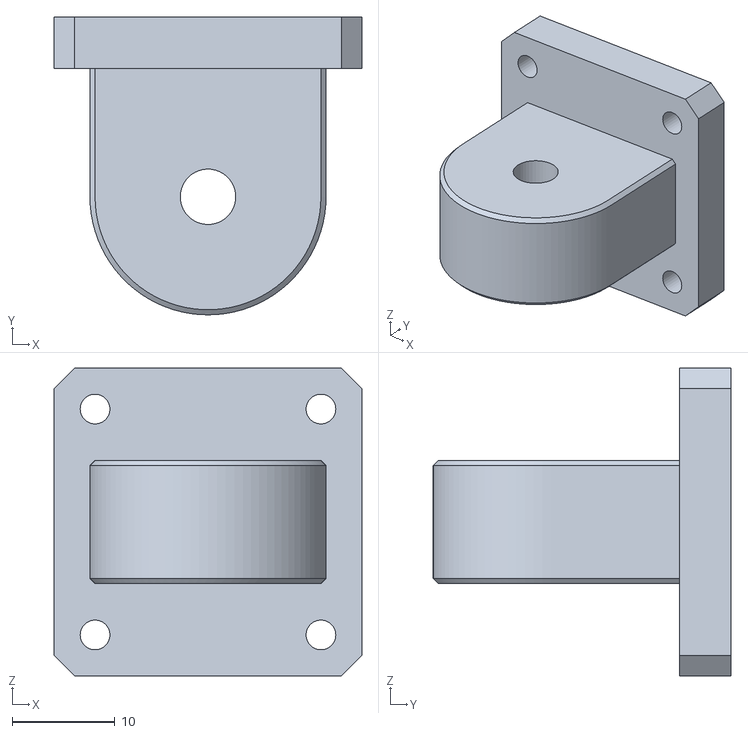
[picture p142: CAD file, 2025-10-22]
case/rev4/dovetail_top.stl
30.0 x 29.0 x 30.0
