brickbots/PiFinder/case/accessories/90_degree_dovetail.stl

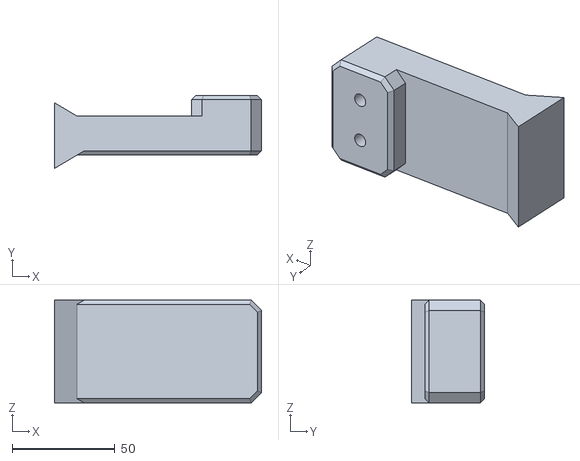
[picture p143: CAD file, 2025-09-29]
case/accessories/90_degree_dovetail.stl
100.9 x 35.5 x 50.0
