brickbots/PiFinder/case/accessories/vixen_right_angle.stl

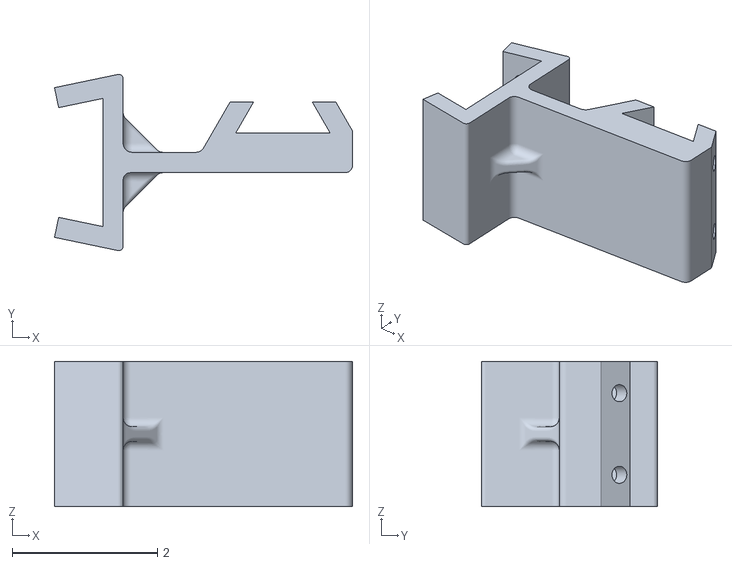
[picture p144: CAD file, 2025-04-20]
case/accessories/vixen_right_angle.stl
4.10 x 2.43 x 2.00
