brickbots/PiFinder/case/accessories/tube_shoe_mount_22mm_bottom.stl

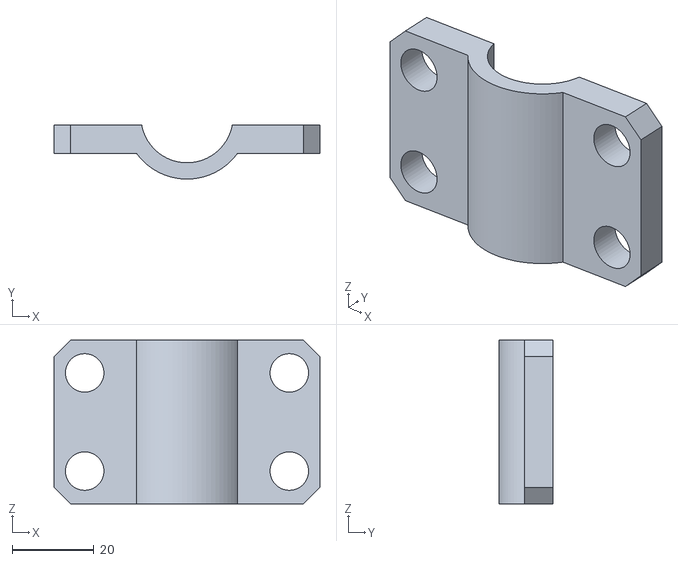
[picture p145: CAD file, 2024-08-23]
case/accessories/tube_shoe_mount_22mm_bottom.stl
65.0 x 13.2 x 40.0
