brickbots/PiFinder/case/accessories/tube_shoe_mount_32mm_bottom.stl

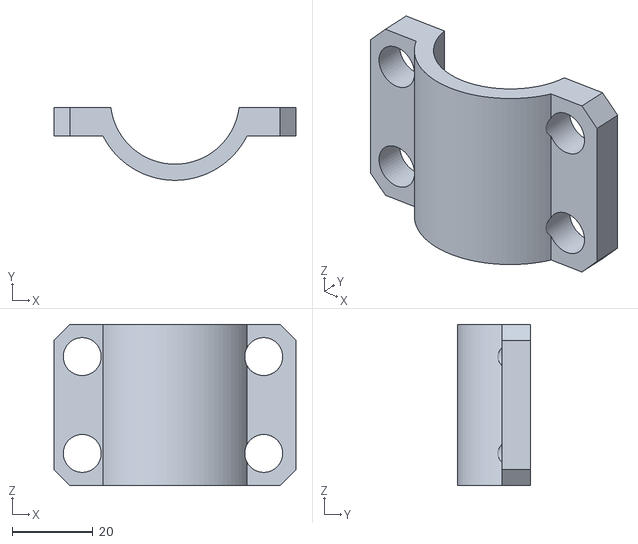
[picture p146: CAD file, 2024-08-23]
case/accessories/tube_shoe_mount_32mm_bottom.stl
60.0 x 18.0 x 40.0
