brickbots/PiFinder/case/accessories/tube_shoe_mount_22mm_top.stl

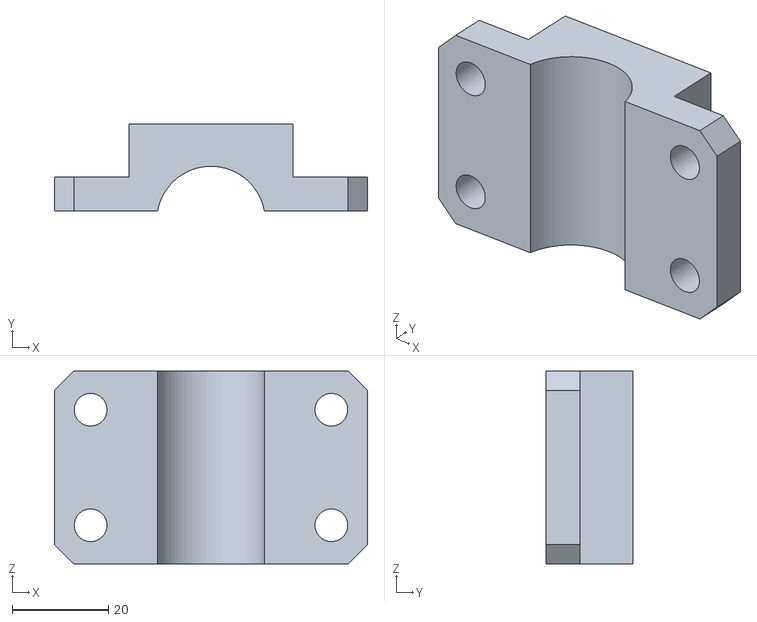
[picture p147: CAD file, 2024-08-23]
case/accessories/tube_shoe_mount_22mm_top.stl
65.0 x 18.0 x 40.0
