brickbots/PiFinder/case/accessories/tube_shoe_mount_32mm_top.stl

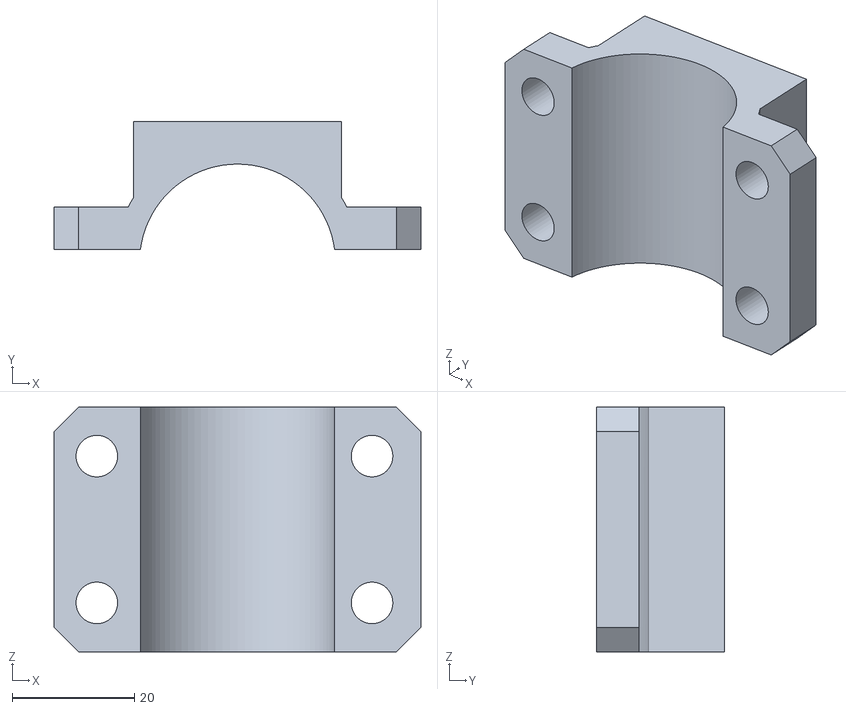
[picture p148: CAD file, 2024-08-23]
case/accessories/tube_shoe_mount_32mm_top.stl
60.0 x 21.0 x 40.0
