brickbots/PiFinder/docs/source/images/build_guide/assembly_left_04.jpeg

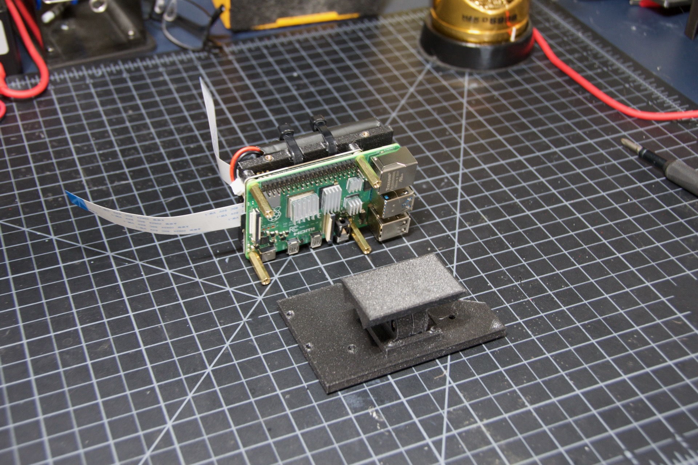
docs/source/images/build_guide/assembly_left_04.jpeg
