brickbots/PiFinder/docs/source/images/build_guide/assembly_left_13.jpeg

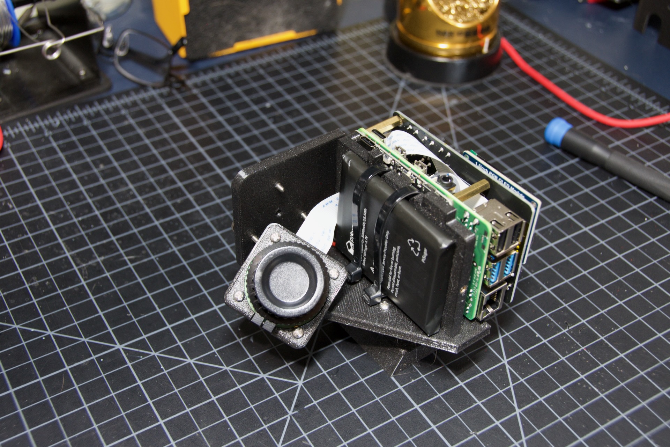
docs/source/images/build_guide/assembly_left_13.jpeg
