brickbots/PiFinder/docs/source/images/build_guide/assembly_left_17.jpeg

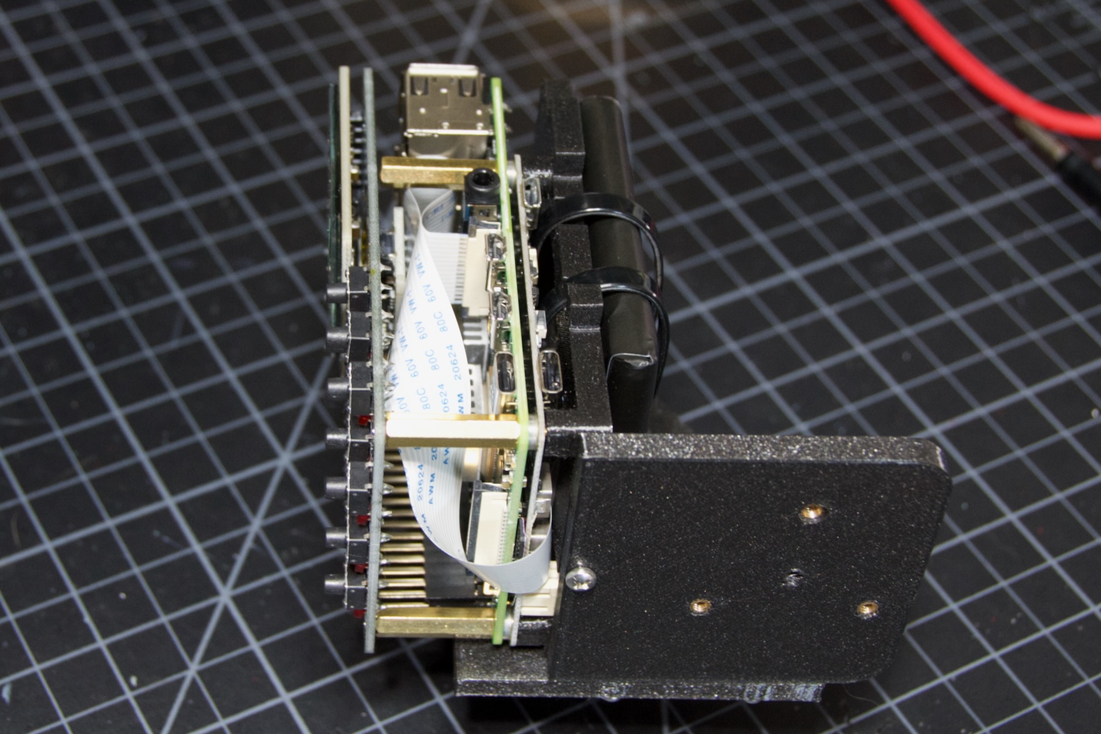
docs/source/images/build_guide/assembly_left_17.jpeg
