brickbots/PiFinder/docs/source/images/build_guide/assembly_right_04.jpeg

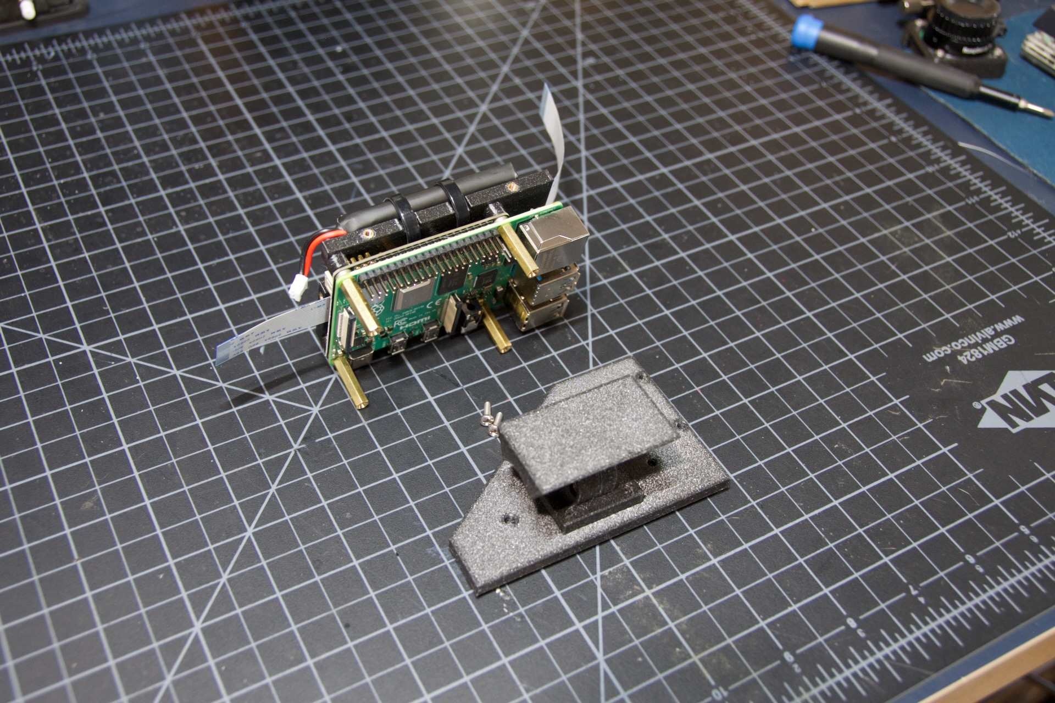
docs/source/images/build_guide/assembly_right_04.jpeg
