brickbots/PiFinder/docs/source/images/build_guide/assembly_right_05.jpeg

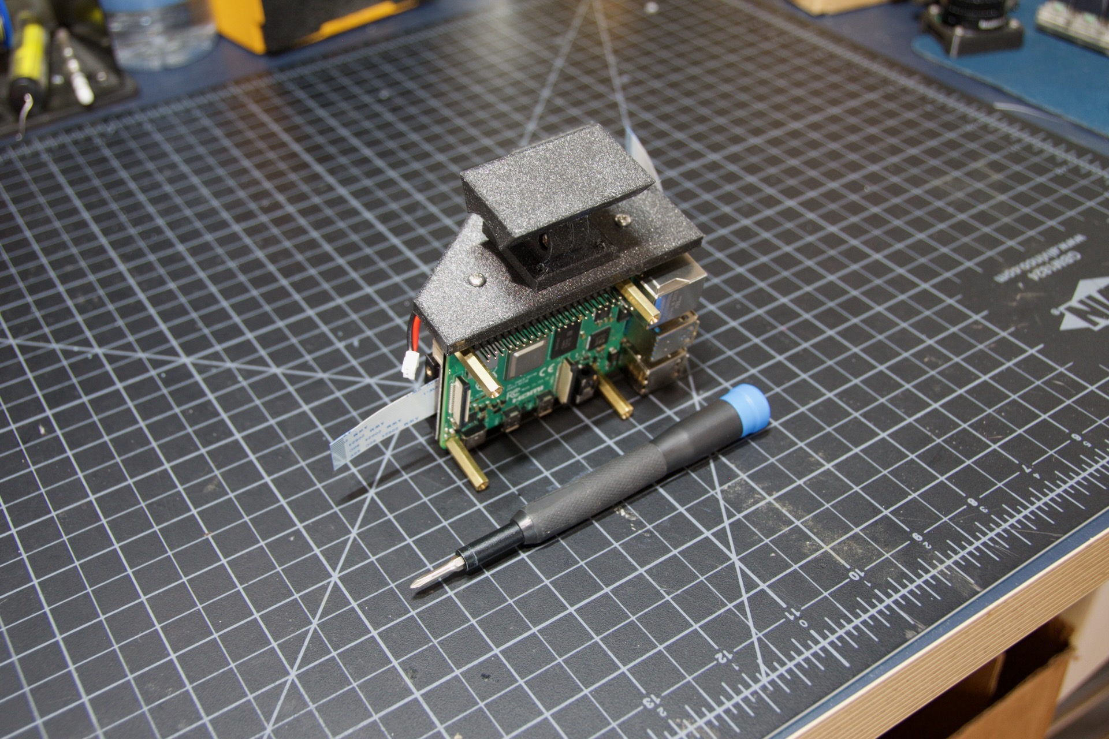
docs/source/images/build_guide/assembly_right_05.jpeg
