brickbots/PiFinder/docs/source/images/build_guide/assembly_right_06.jpeg

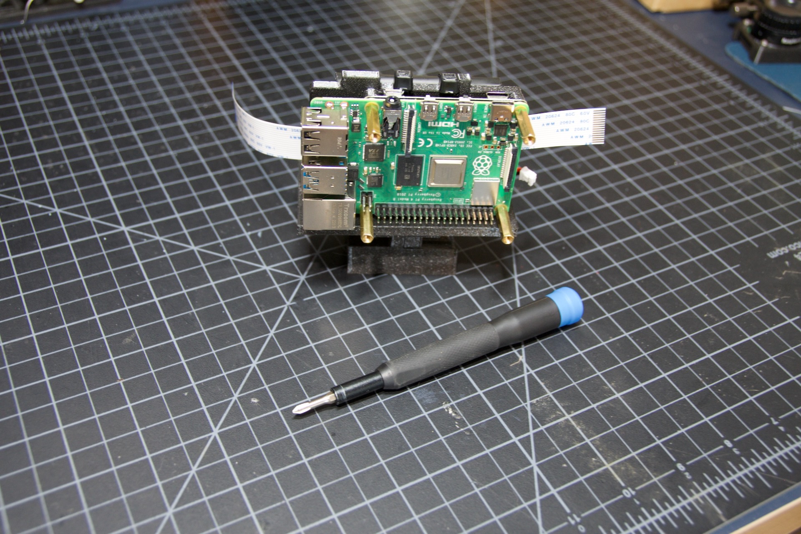
docs/source/images/build_guide/assembly_right_06.jpeg
