brickbots/PiFinder/docs/source/images/build_guide/assembly_right_17.jpeg

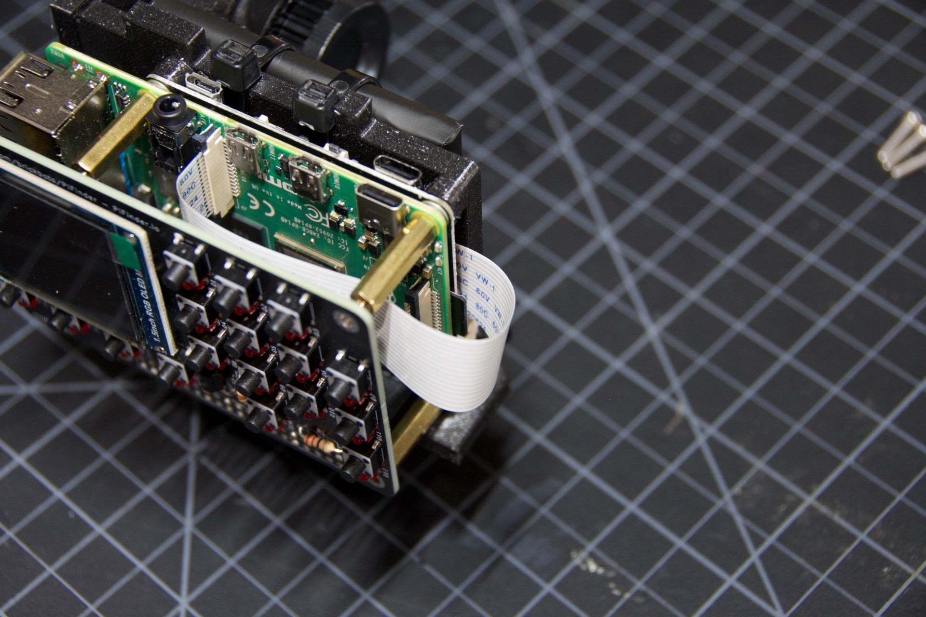
docs/source/images/build_guide/assembly_right_17.jpeg
