brickbots/PiFinder/docs/source/images/build_guide/cam_1.jpeg

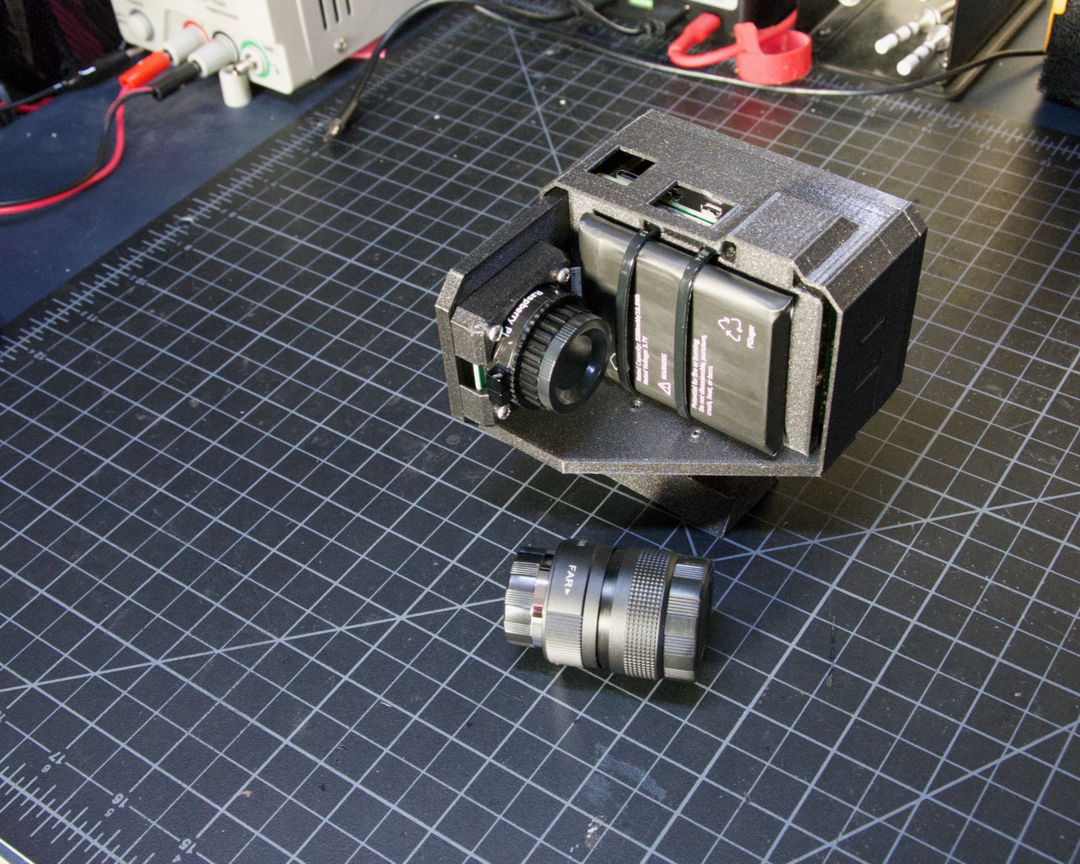
docs/source/images/build_guide/cam_1.jpeg
