brickbots/PiFinder/docs/source/images/build_guide/cam_2.jpeg

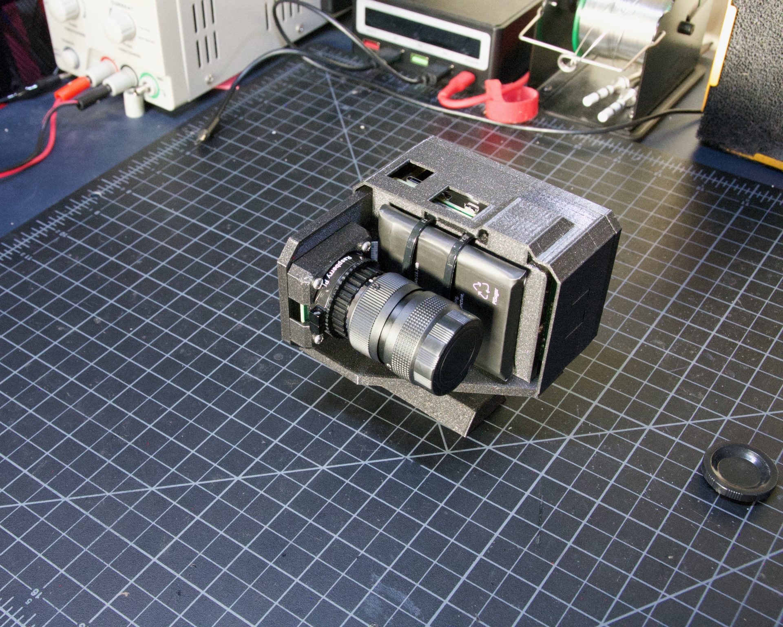
docs/source/images/build_guide/cam_2.jpeg
