brickbots/PiFinder/docs/source/images/build_guide/left_11.jpeg

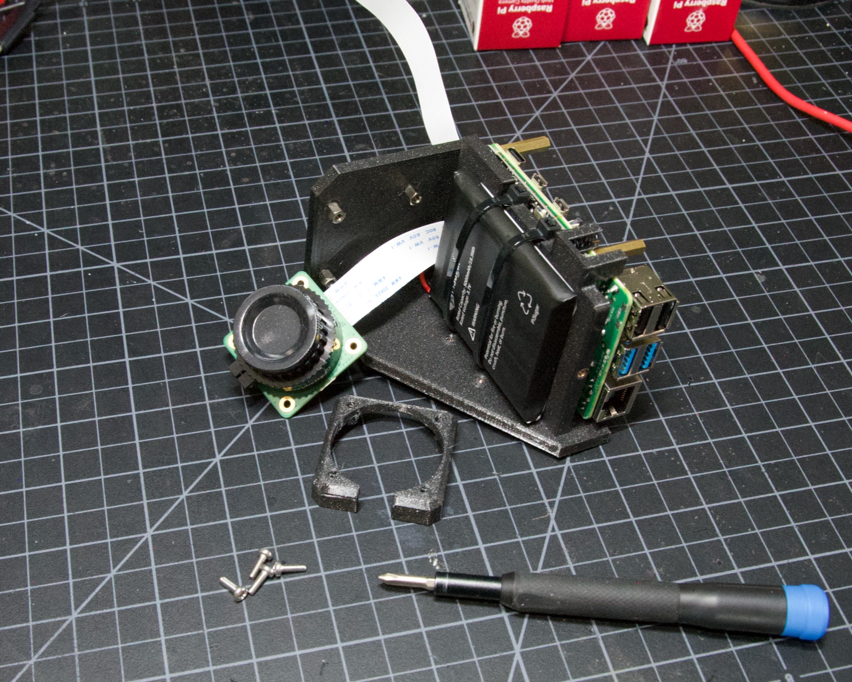
docs/source/images/build_guide/left_11.jpeg
