brickbots/PiFinder/docs/source/images/build_guide/right_12.jpeg

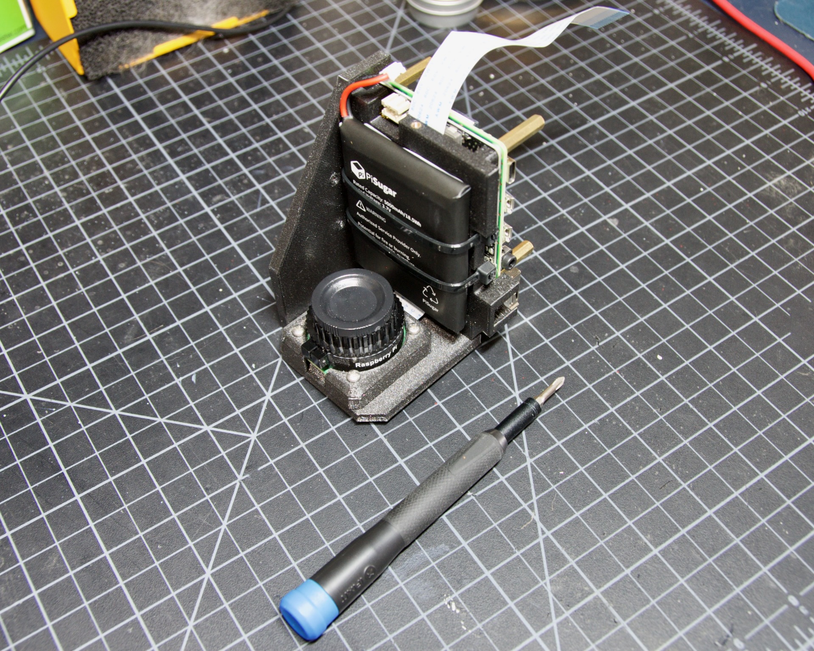
docs/source/images/build_guide/right_12.jpeg
