brickbots/PiFinder/docs/source/images/build_guide/right_13.jpeg

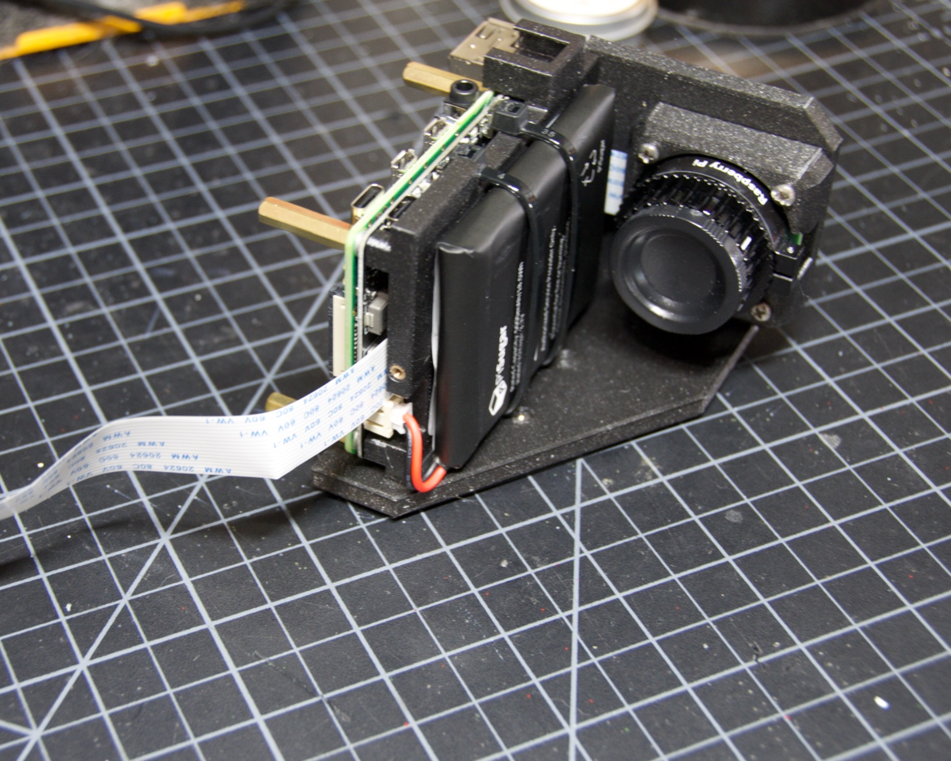
docs/source/images/build_guide/right_13.jpeg
