brickbots/PiFinder/docs/source/images/user_guide/object_list_05_docs.png

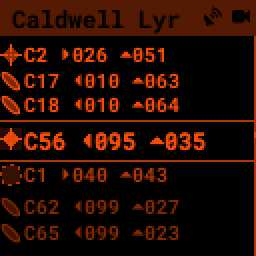
docs/source/images/user_guide/object_list_05_docs.png
