brickbots/PiFinder/images/build_guide/adjustable_dovetail/DSC_8569.jpeg

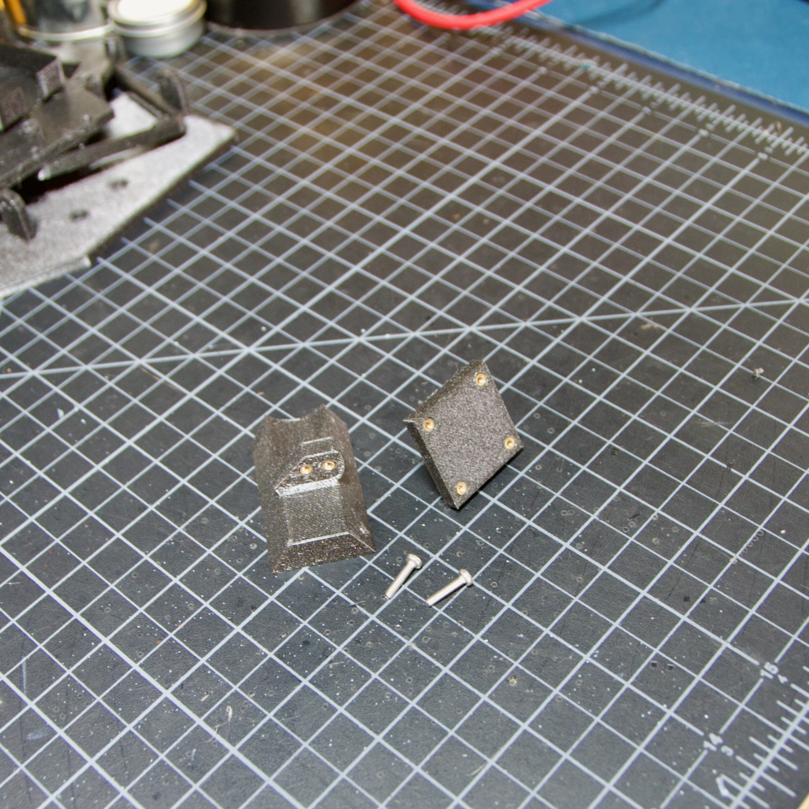
images/build_guide/adjustable_dovetail/DSC_8569.jpeg
