brickbots/PiFinder/images/build_guide/adjustable_dovetail/DSC_8578.jpeg

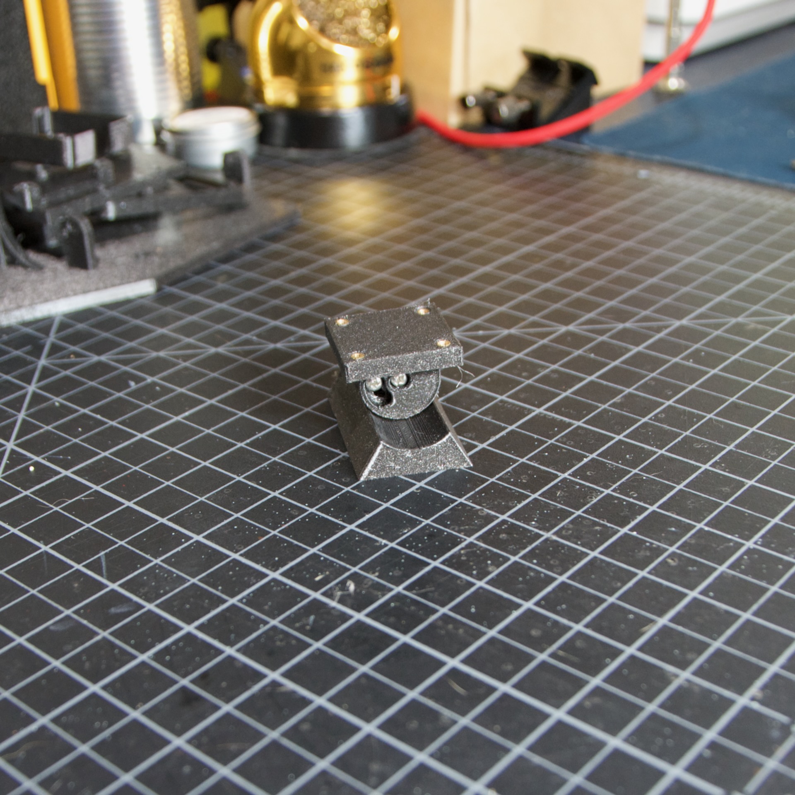
images/build_guide/adjustable_dovetail/DSC_8578.jpeg
