brickbots/PiFinder/images/build_guide/case/small_style_inserts.png

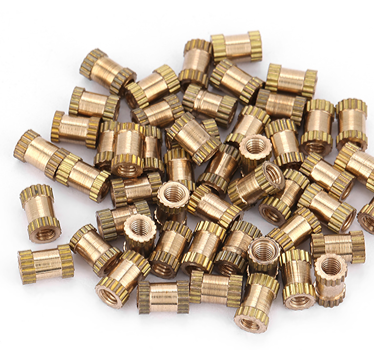
images/build_guide/case/small_style_inserts.png
