brickbots/PiFinder/images/build_guide/IMG_4633.jpeg

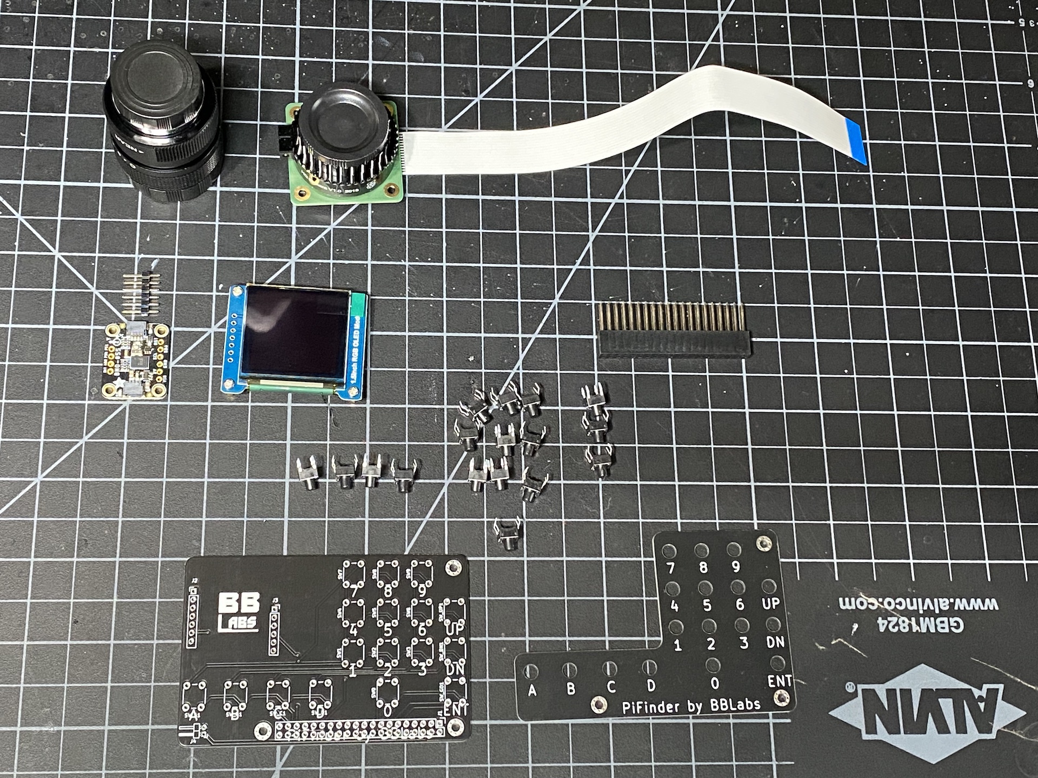
images/build_guide/IMG_4633.jpeg
