brickbots/PiFinder/images/build_guide/IMG_4634.jpeg

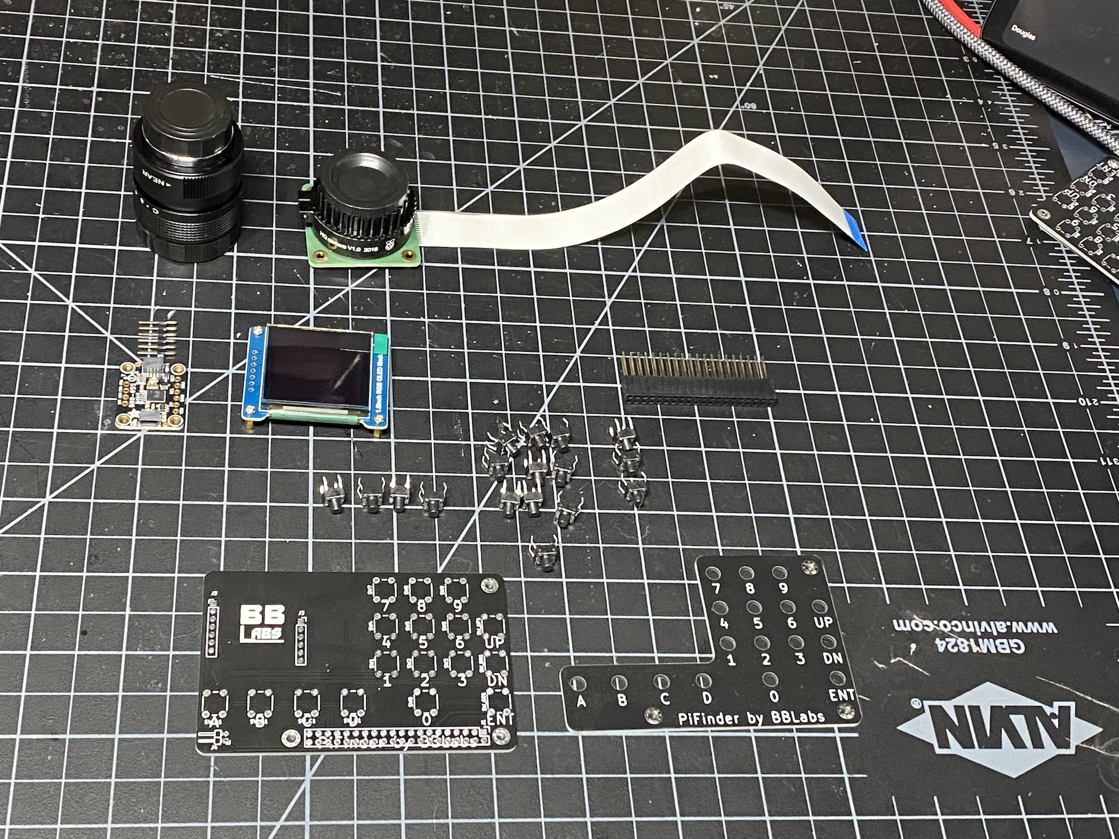
images/build_guide/IMG_4634.jpeg
