brickbots/PiFinder/images/build_guide/IMG_4635.jpeg

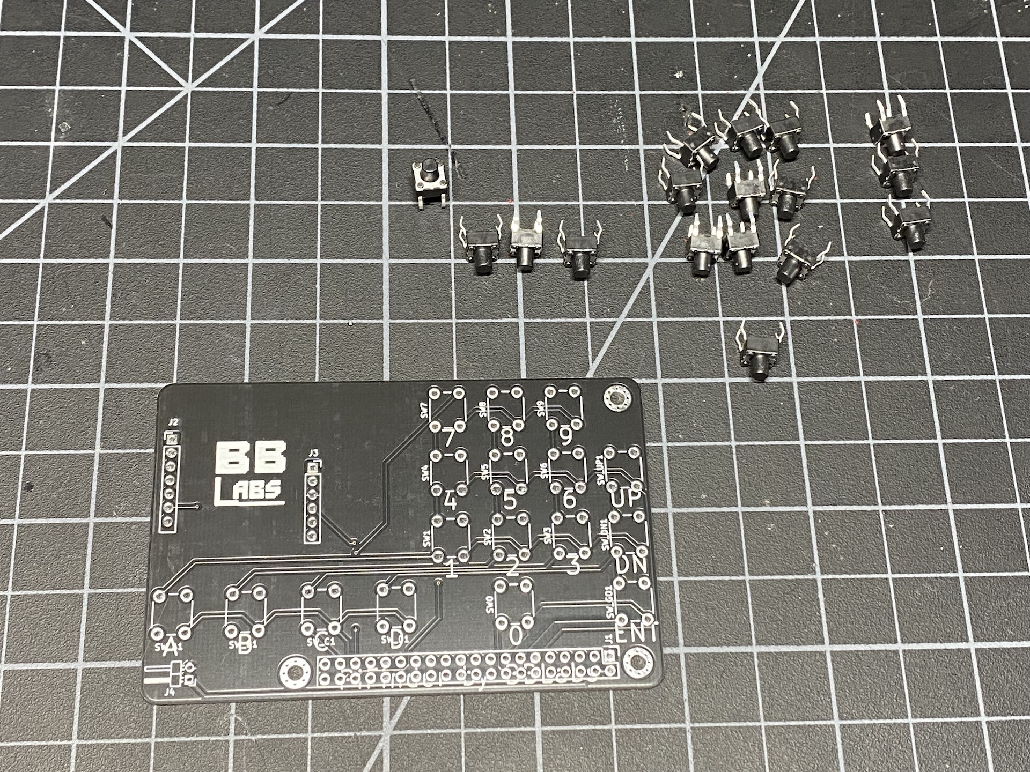
images/build_guide/IMG_4635.jpeg
