brickbots/PiFinder/images/build_guide/IMG_4636.jpeg

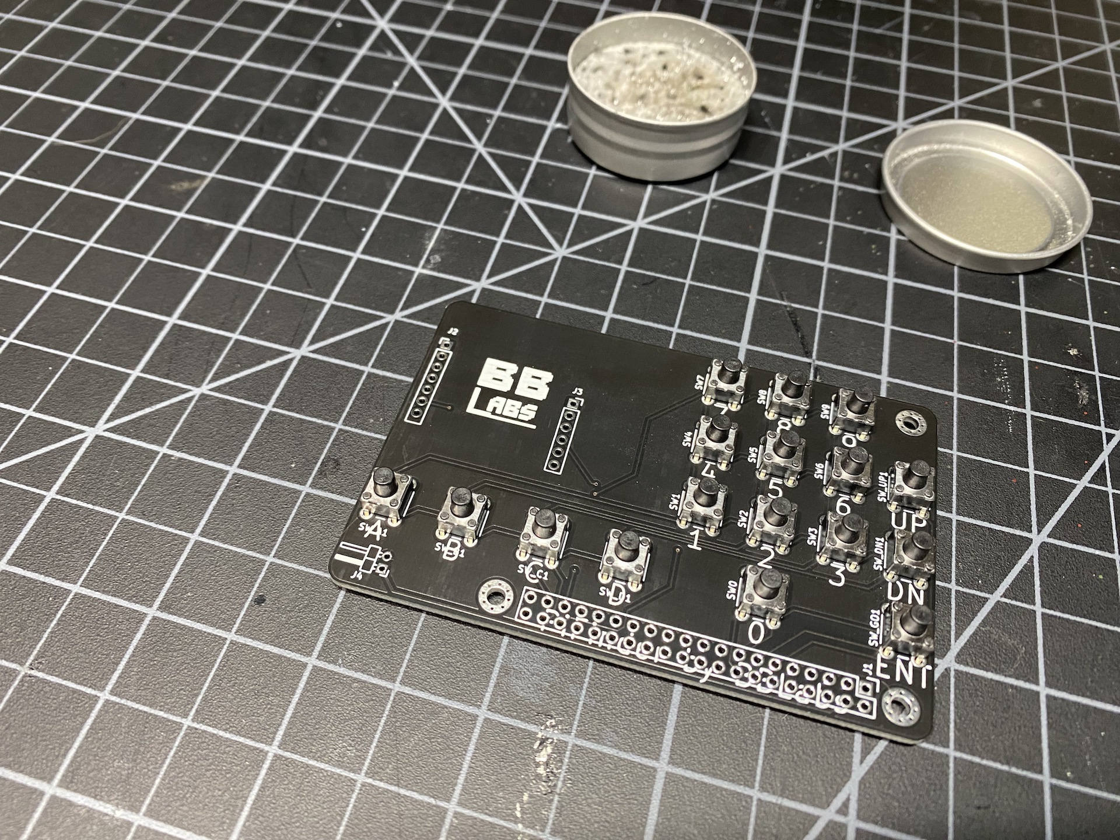
images/build_guide/IMG_4636.jpeg
