brickbots/PiFinder/images/build_guide/IMG_4637.jpeg

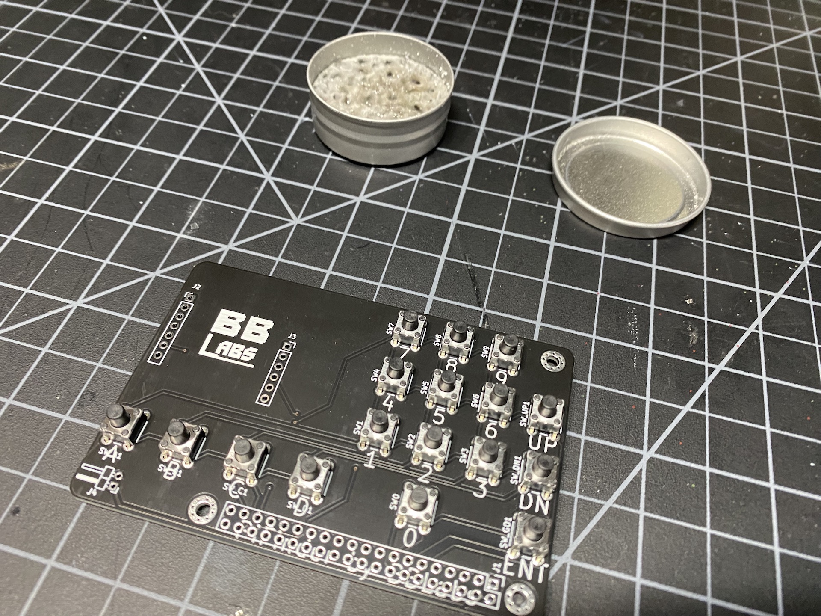
images/build_guide/IMG_4637.jpeg
