brickbots/PiFinder/images/build_guide/IMG_4638.jpeg

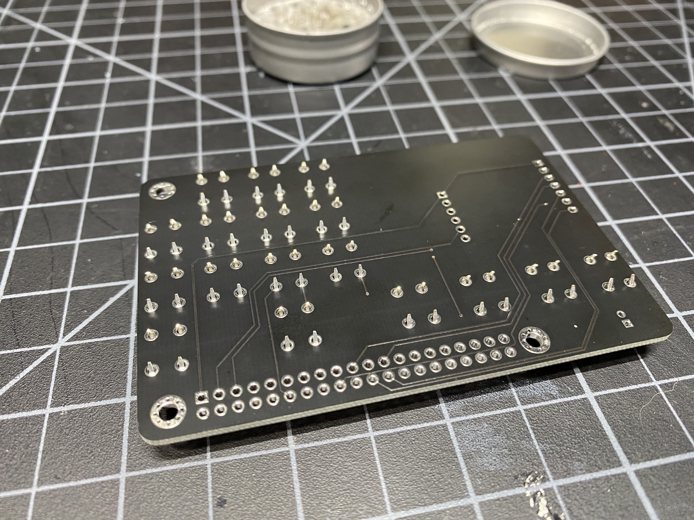
images/build_guide/IMG_4638.jpeg
