brickbots/PiFinder/images/build_guide/IMG_4639.jpeg

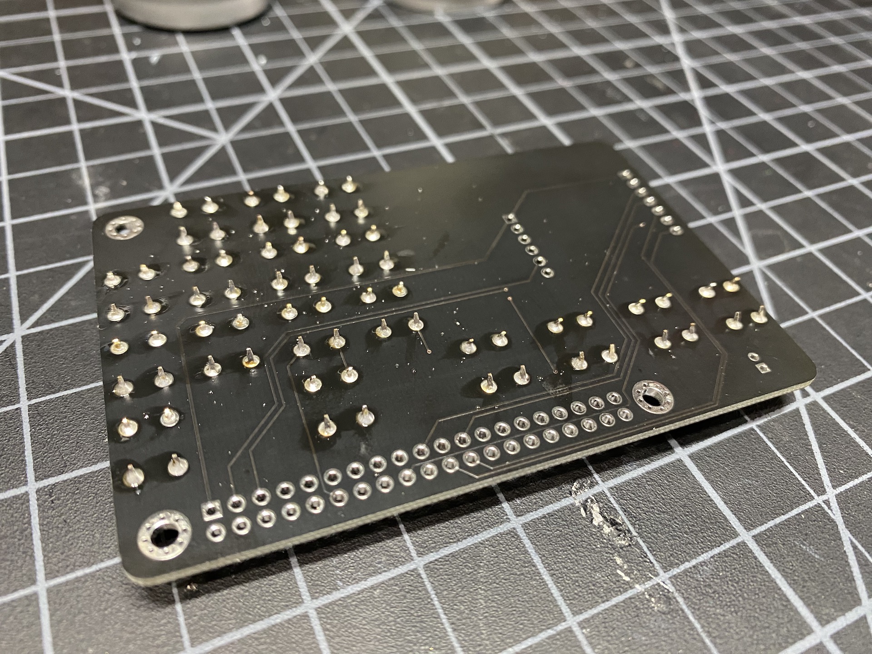
images/build_guide/IMG_4639.jpeg
