brickbots/PiFinder/images/build_guide/IMG_4642.jpeg

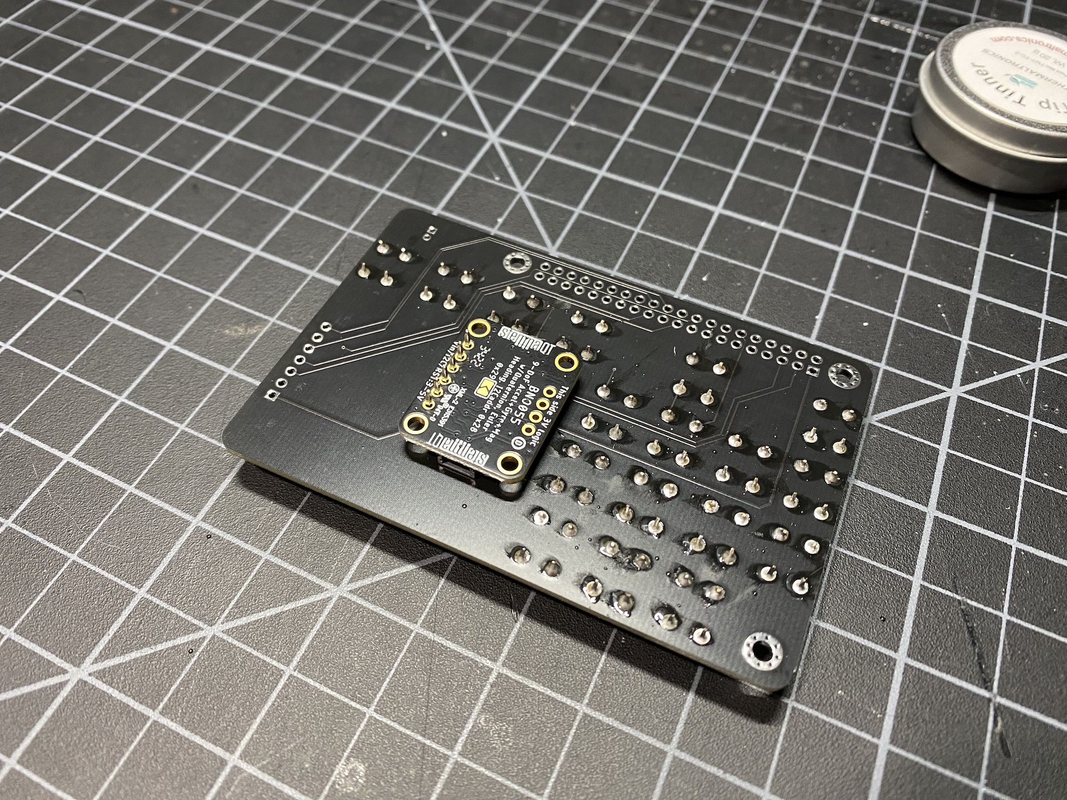
images/build_guide/IMG_4642.jpeg
