brickbots/PiFinder/images/build_guide/IMG_4643.jpeg

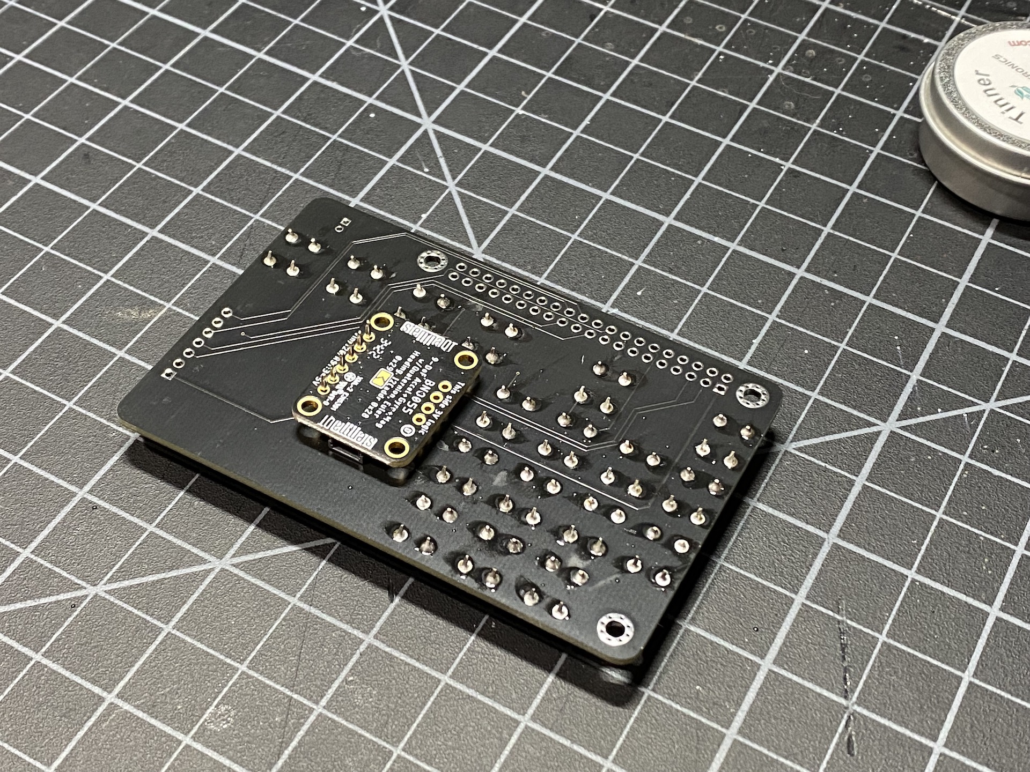
images/build_guide/IMG_4643.jpeg
