brickbots/PiFinder/images/build_guide/IMG_4647.jpeg

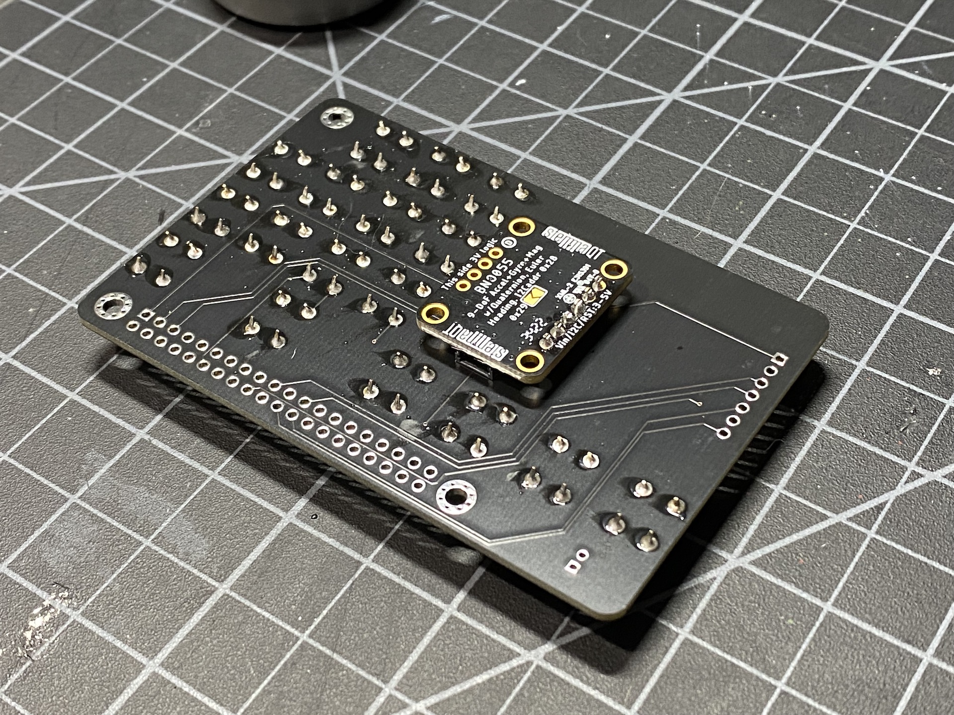
images/build_guide/IMG_4647.jpeg
