brickbots/PiFinder/images/build_guide/IMG_4651.jpeg

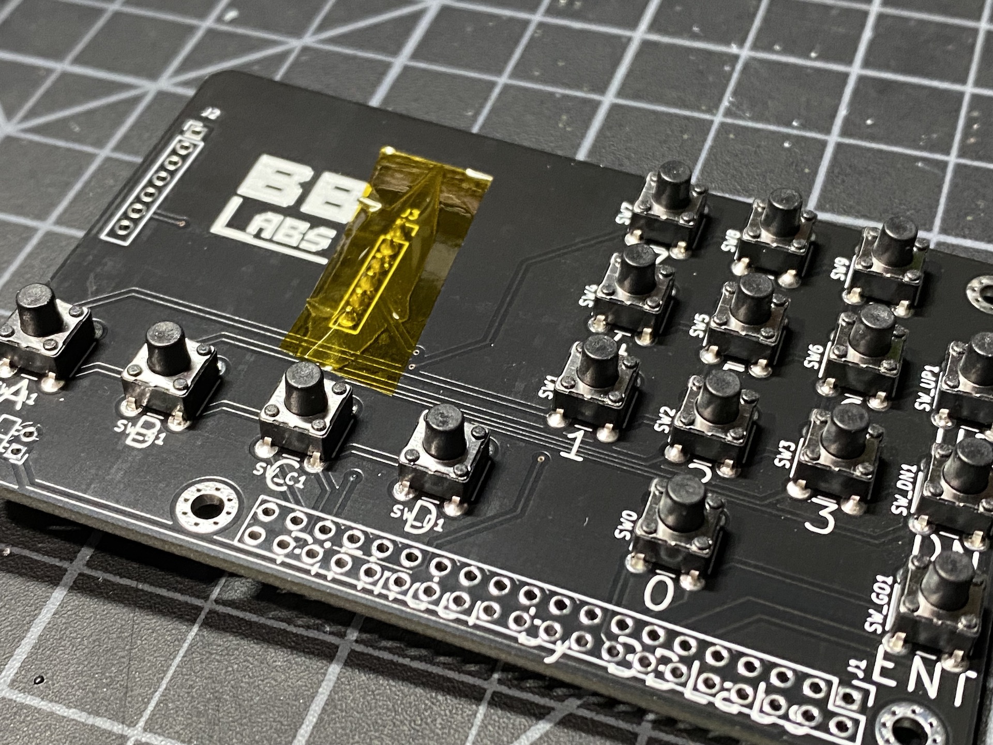
images/build_guide/IMG_4651.jpeg
