brickbots/PiFinder/images/build_guide/IMG_4655.jpeg

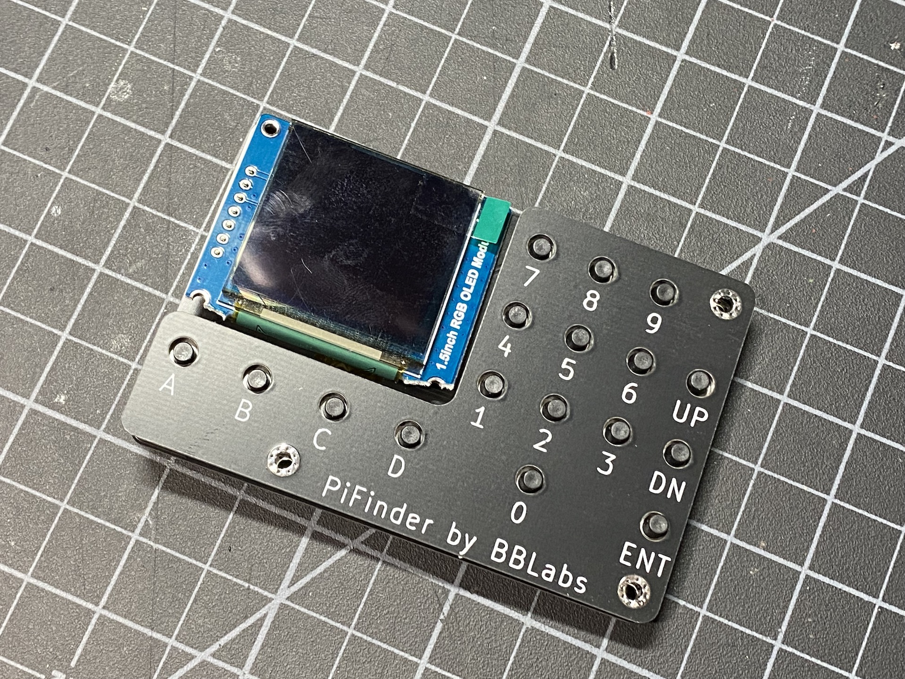
images/build_guide/IMG_4655.jpeg
