brickbots/PiFinder/images/build_guide/IMG_4658.jpeg

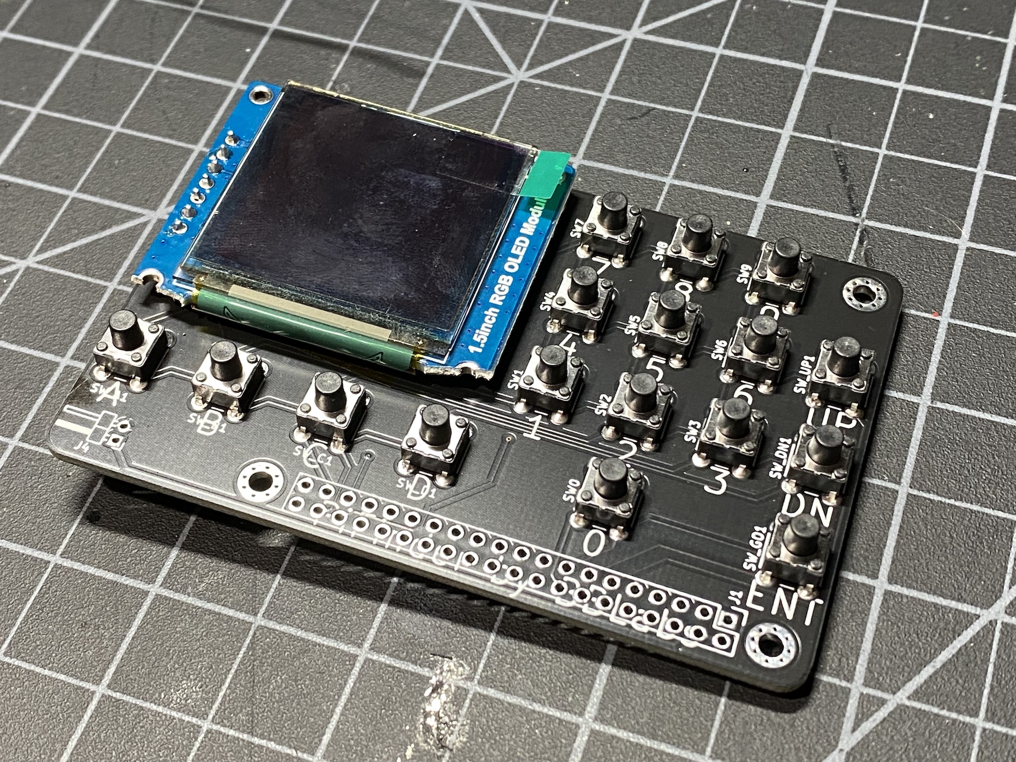
images/build_guide/IMG_4658.jpeg
