brickbots/PiFinder/images/build_guide/IMG_4661.jpeg

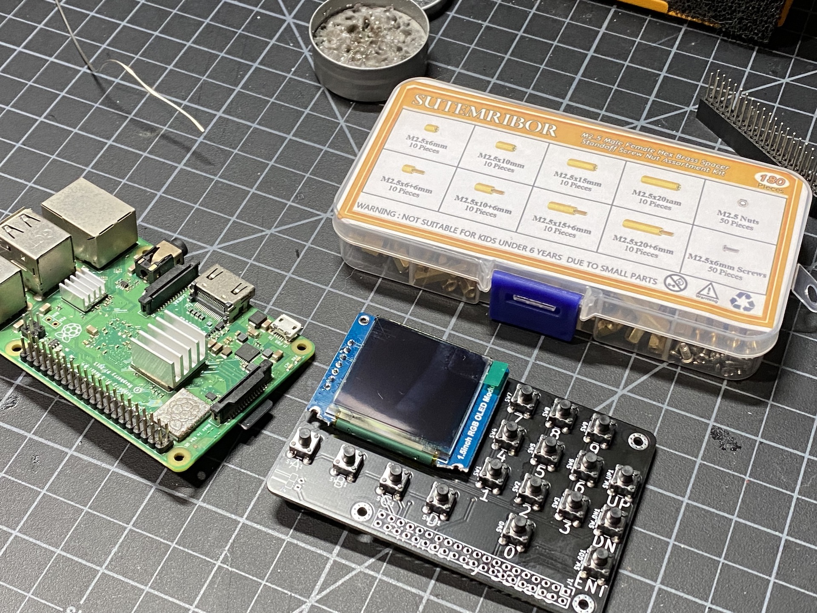
images/build_guide/IMG_4661.jpeg
