brickbots/PiFinder/images/build_guide/IMG_4662.jpeg

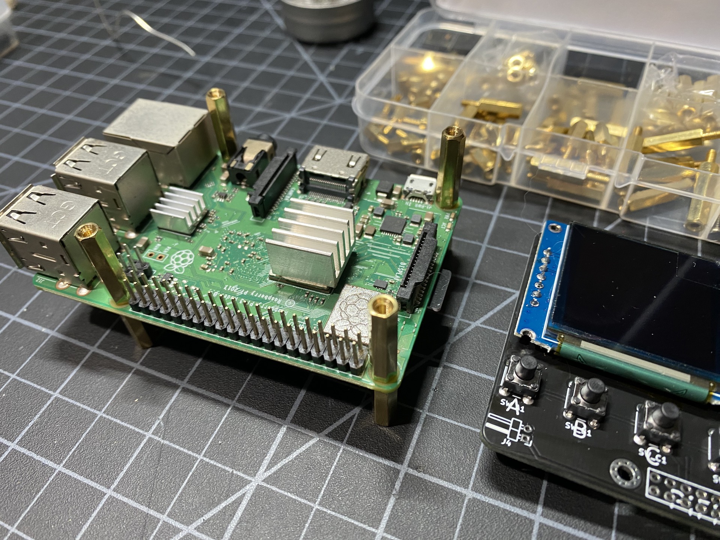
images/build_guide/IMG_4662.jpeg
