brickbots/PiFinder/images/build_guide/IMG_4663.jpeg

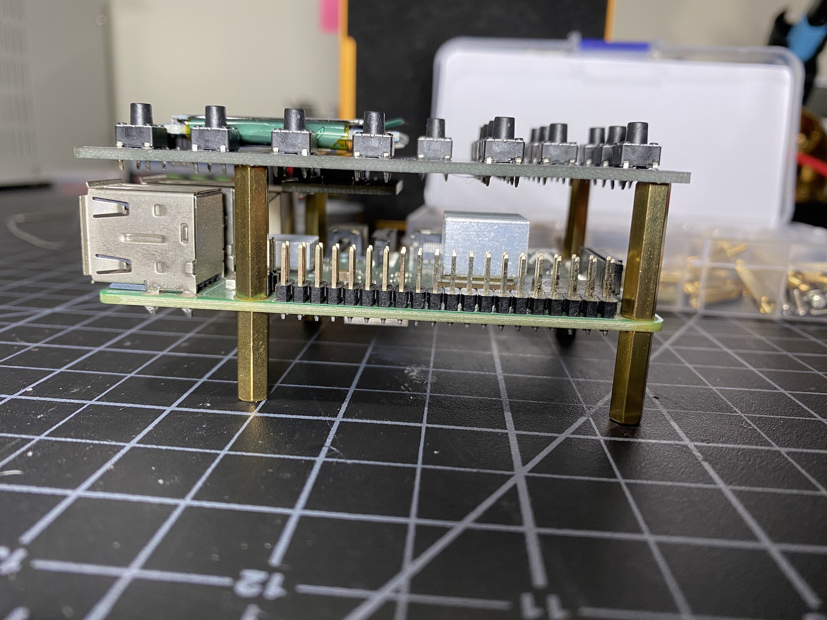
images/build_guide/IMG_4663.jpeg
