brickbots/PiFinder/images/build_guide/IMG_4667.jpeg

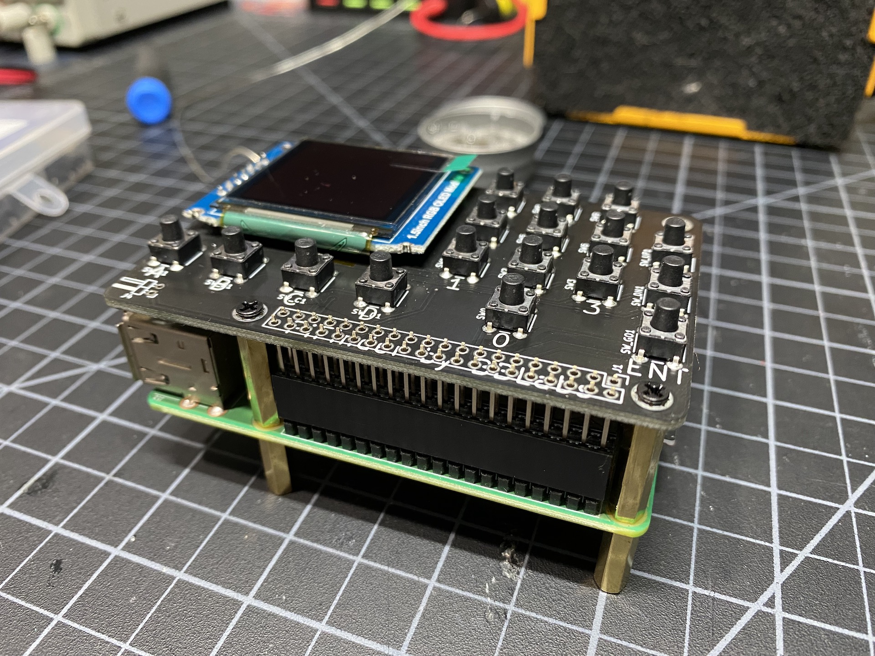
images/build_guide/IMG_4667.jpeg
