brickbots/PiFinder/images/build_guide/IMG_4685.jpeg

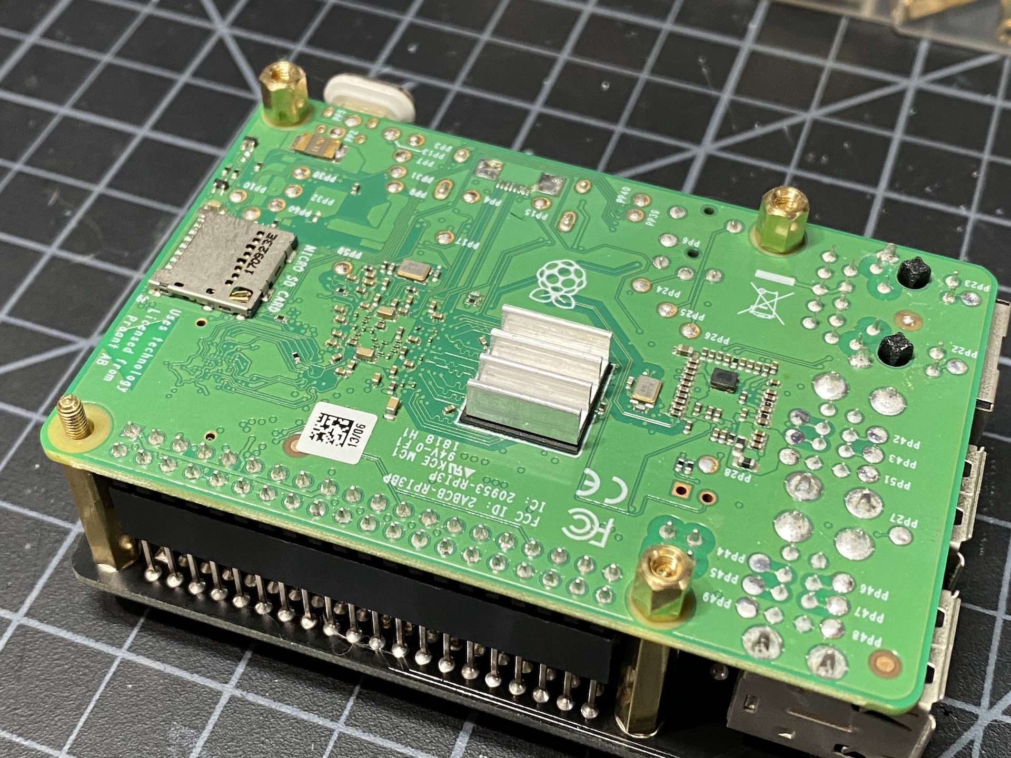
images/build_guide/IMG_4685.jpeg
