brickbots/PiFinder/images/build_guide/IMG_4686.jpeg

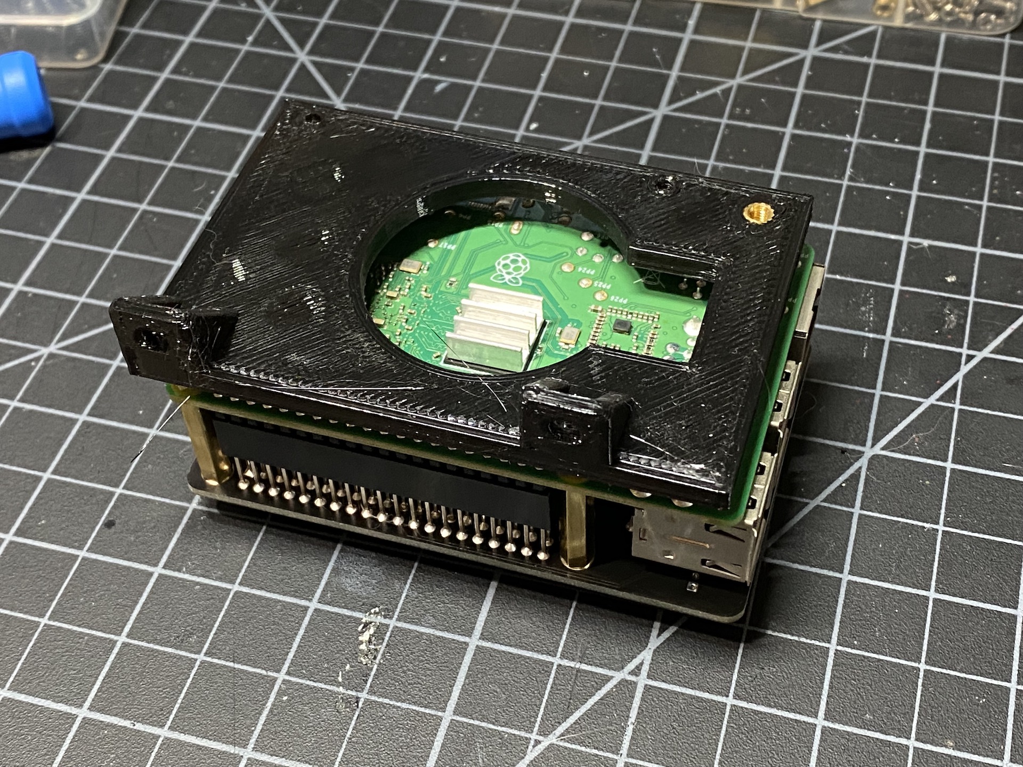
images/build_guide/IMG_4686.jpeg
