brickbots/PiFinder/images/build_guide/IMG_4687.jpeg

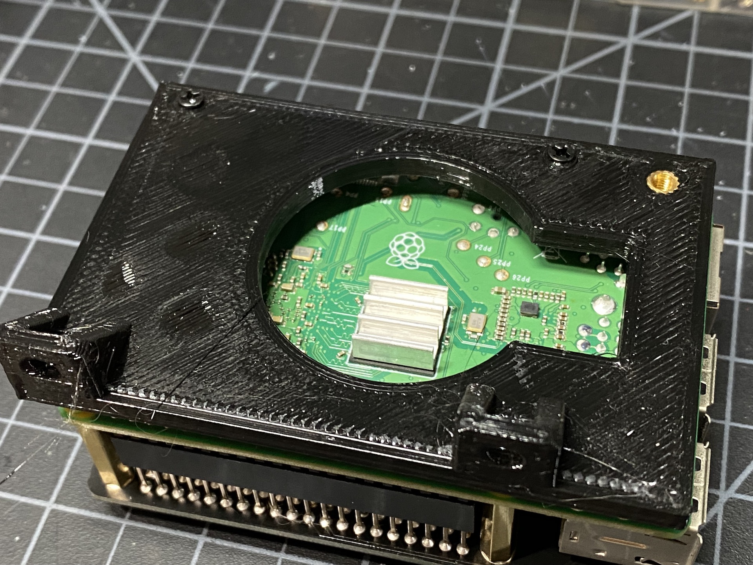
images/build_guide/IMG_4687.jpeg
