brickbots/PiFinder/images/build_guide/IMG_4688.jpeg

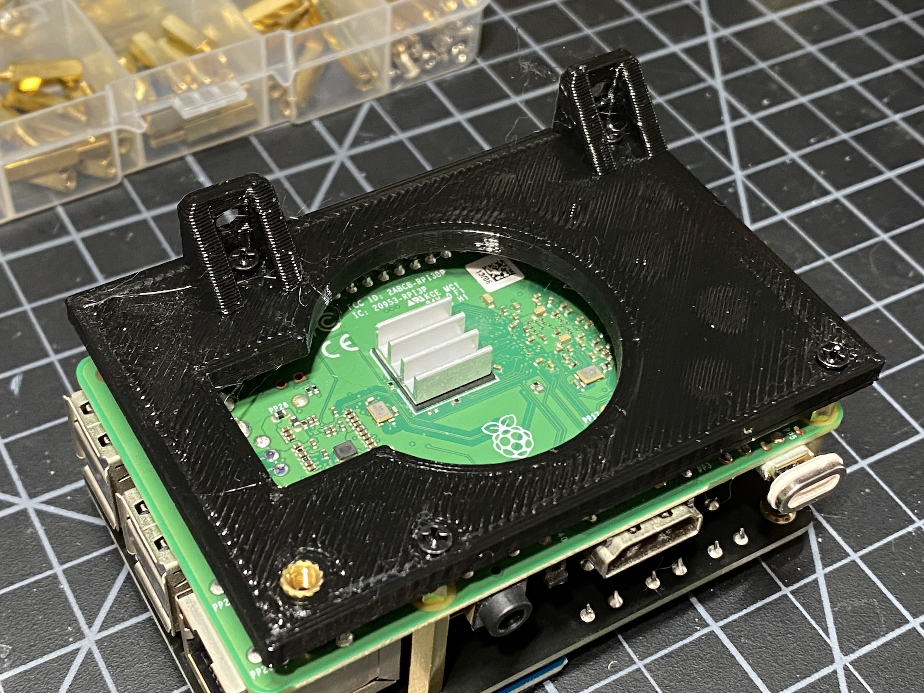
images/build_guide/IMG_4688.jpeg
