brickbots/PiFinder/images/build_guide/IMG_4689.jpeg

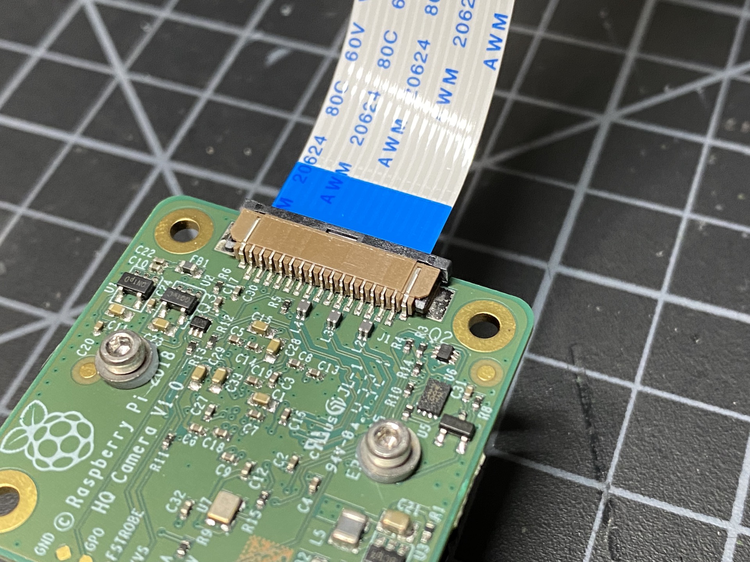
images/build_guide/IMG_4689.jpeg
