brickbots/PiFinder/images/build_guide/IMG_4695.jpeg

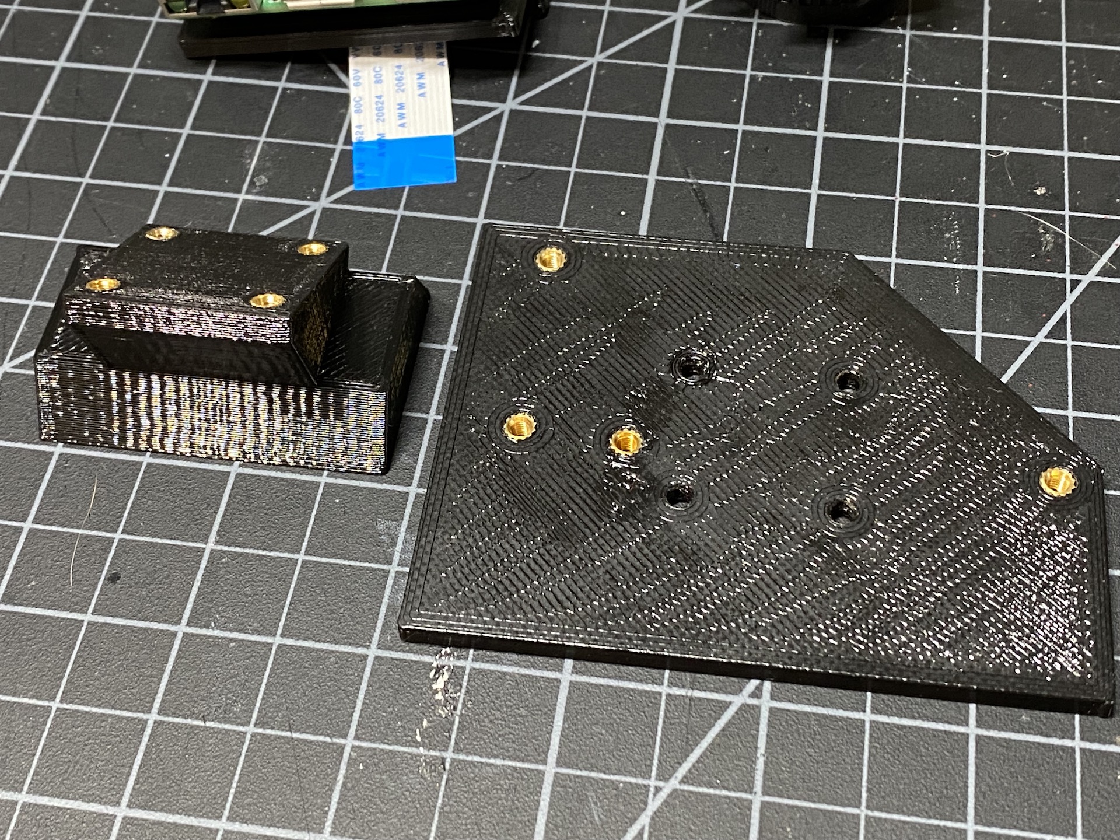
images/build_guide/IMG_4695.jpeg
