brickbots/PiFinder/images/build_guide/IMG_4697.jpeg

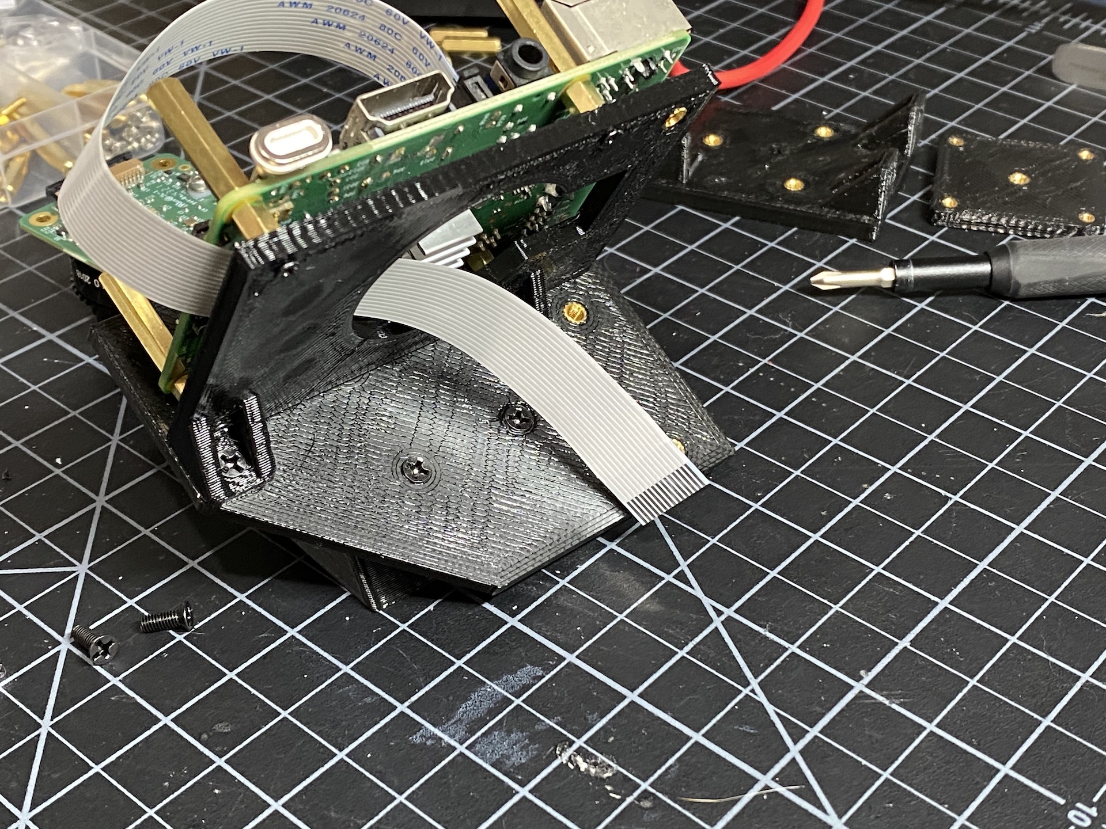
images/build_guide/IMG_4697.jpeg
