brickbots/PiFinder/images/build_guide/IMG_4698.jpeg

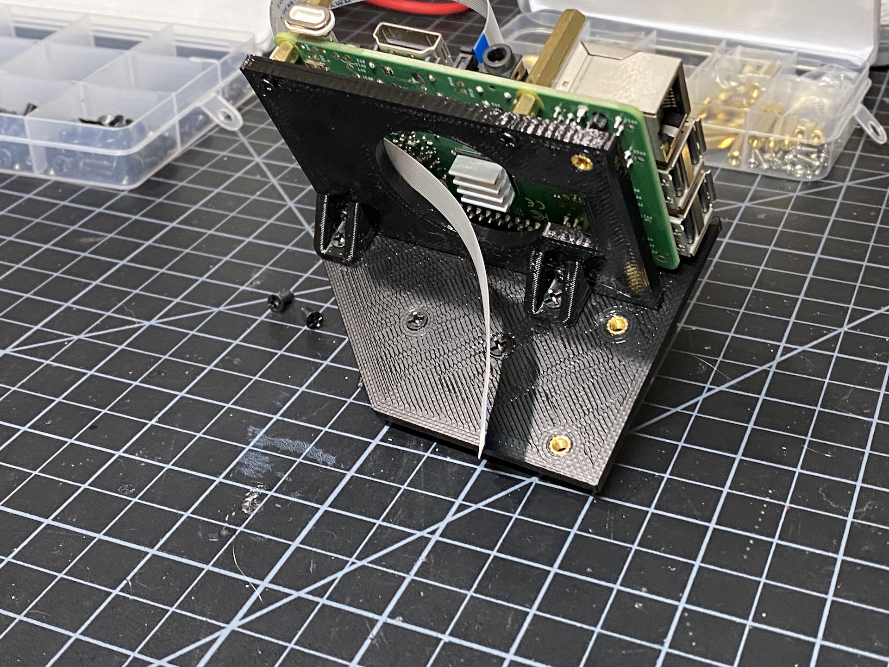
images/build_guide/IMG_4698.jpeg
