brickbots/PiFinder/images/build_guide/IMG_4702.jpeg

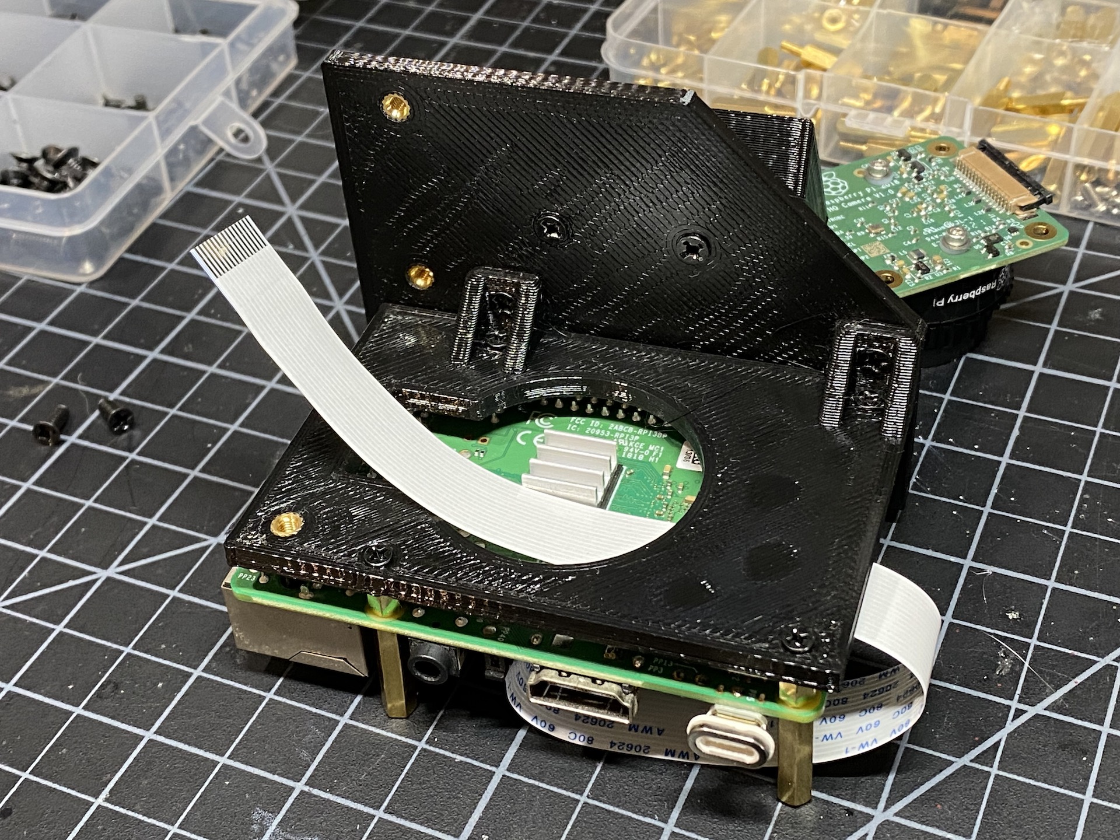
images/build_guide/IMG_4702.jpeg
