brickbots/PiFinder/images/build_guide/IMG_4709.jpeg

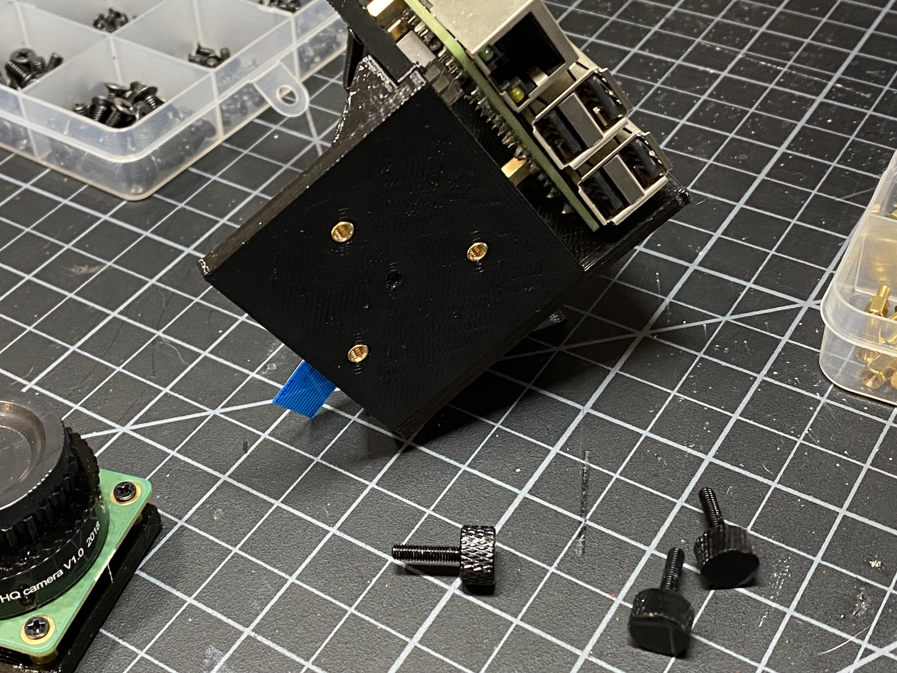
images/build_guide/IMG_4709.jpeg
