brickbots/PiFinder/images/build_guide/IMG_4711.jpeg

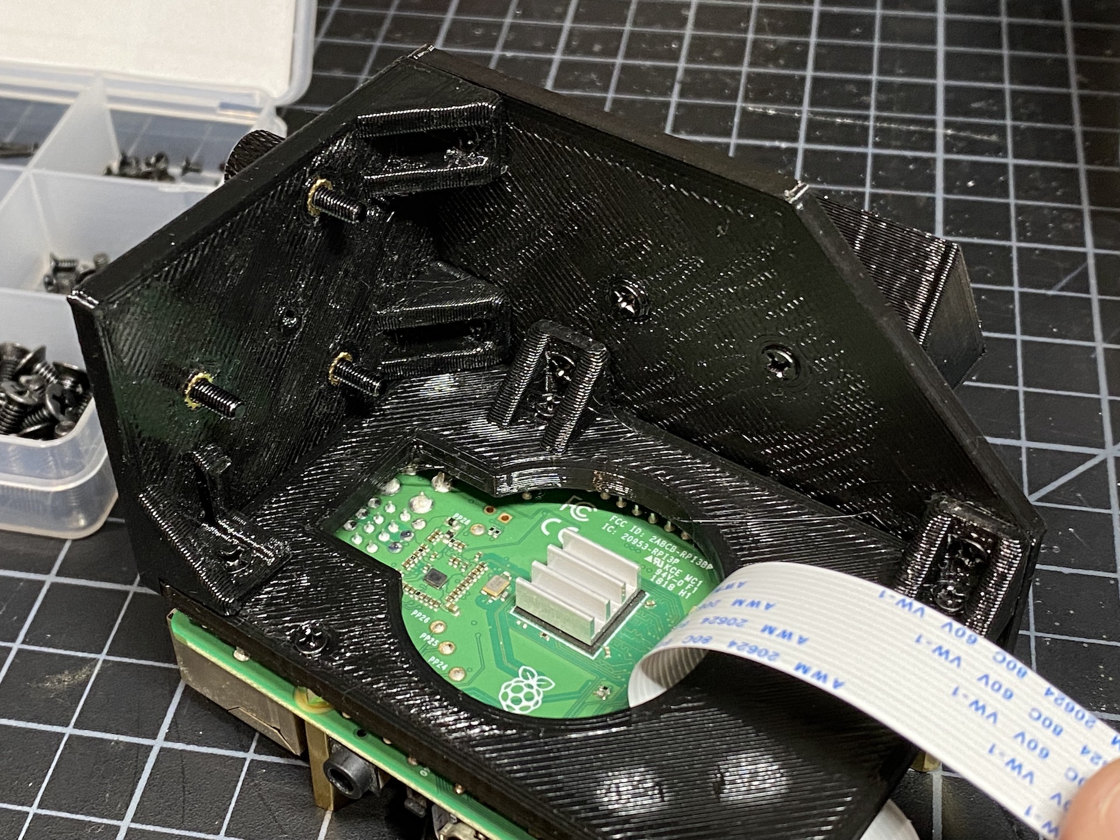
images/build_guide/IMG_4711.jpeg
