brickbots/PiFinder/images/build_guide/IMG_4713.jpeg

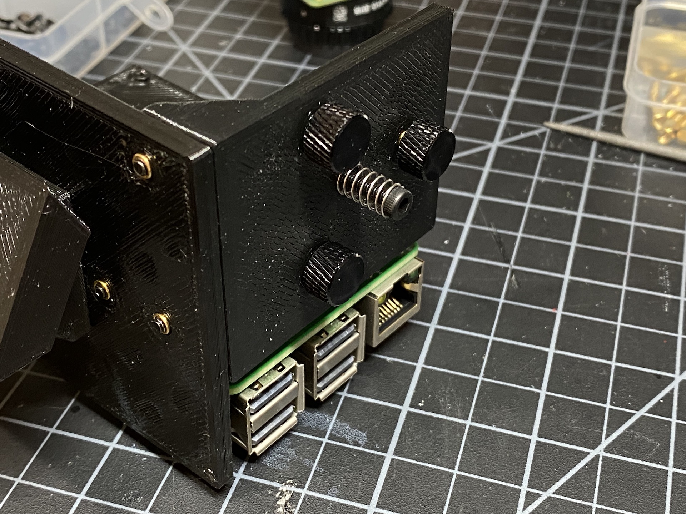
images/build_guide/IMG_4713.jpeg
