brickbots/PiFinder/images/build_guide/IMG_4716.jpeg

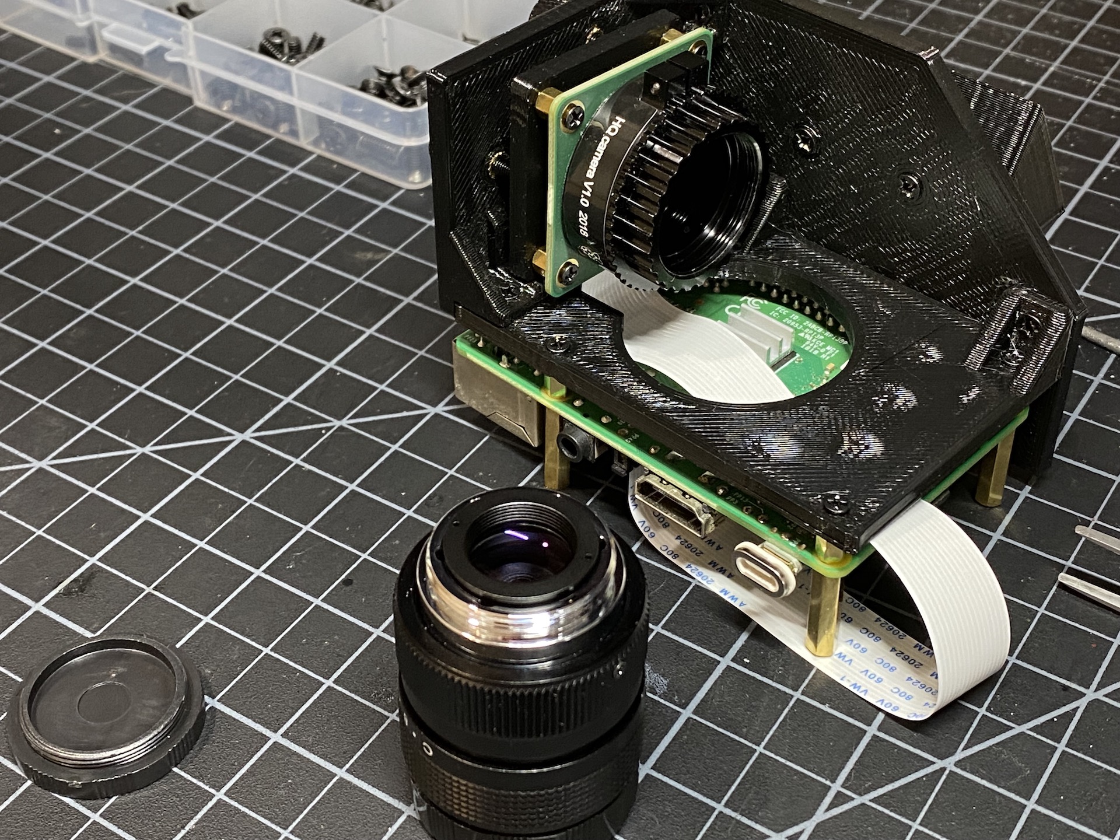
images/build_guide/IMG_4716.jpeg
