brickbots/PiFinder/images/build_guide/IMG_4717.jpeg

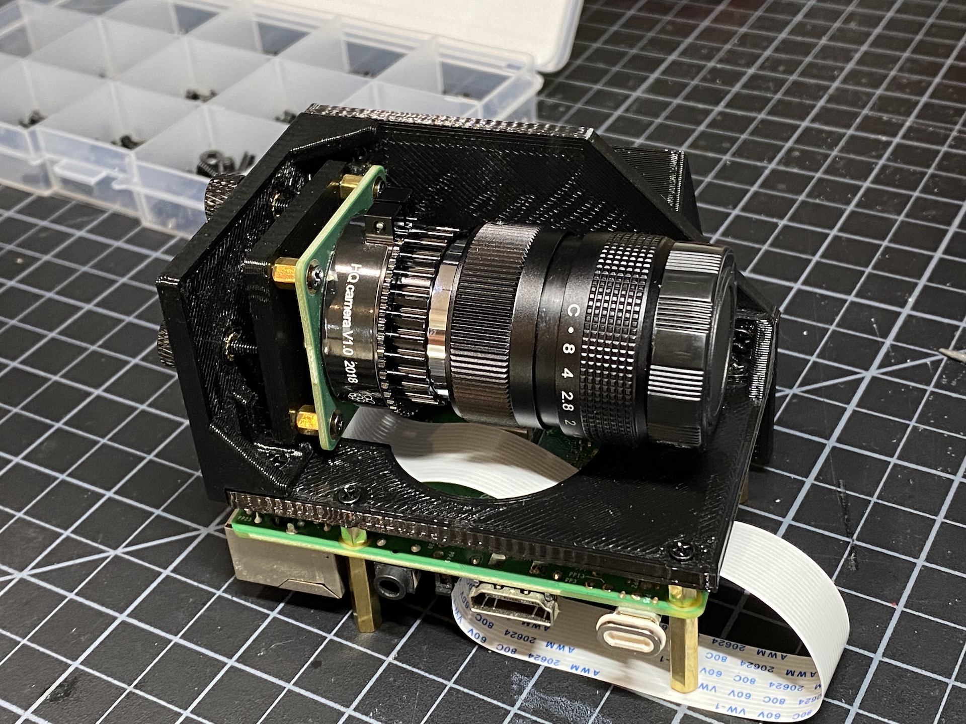
images/build_guide/IMG_4717.jpeg
