brickbots/PiFinder/images/build_guide/IMG_4718.jpeg

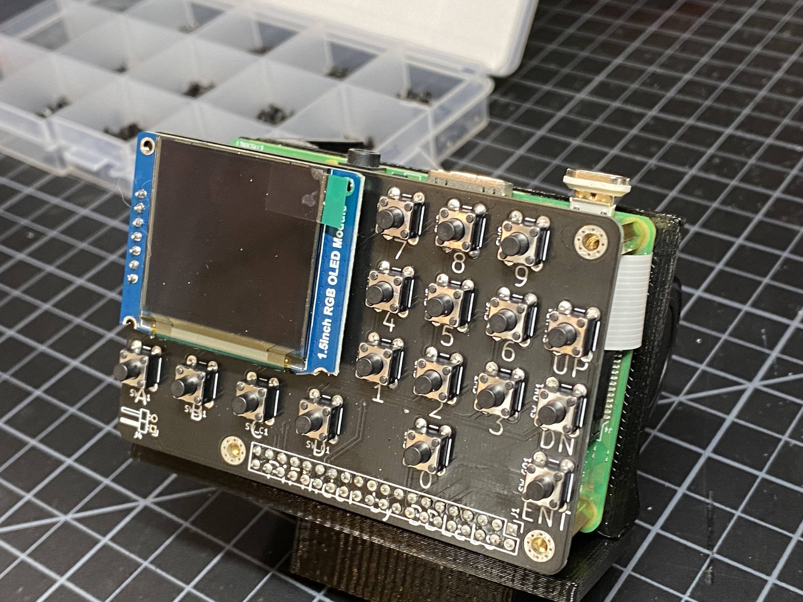
images/build_guide/IMG_4718.jpeg
