brickbots/PiFinder/images/build_guide/IMG_4721.jpeg

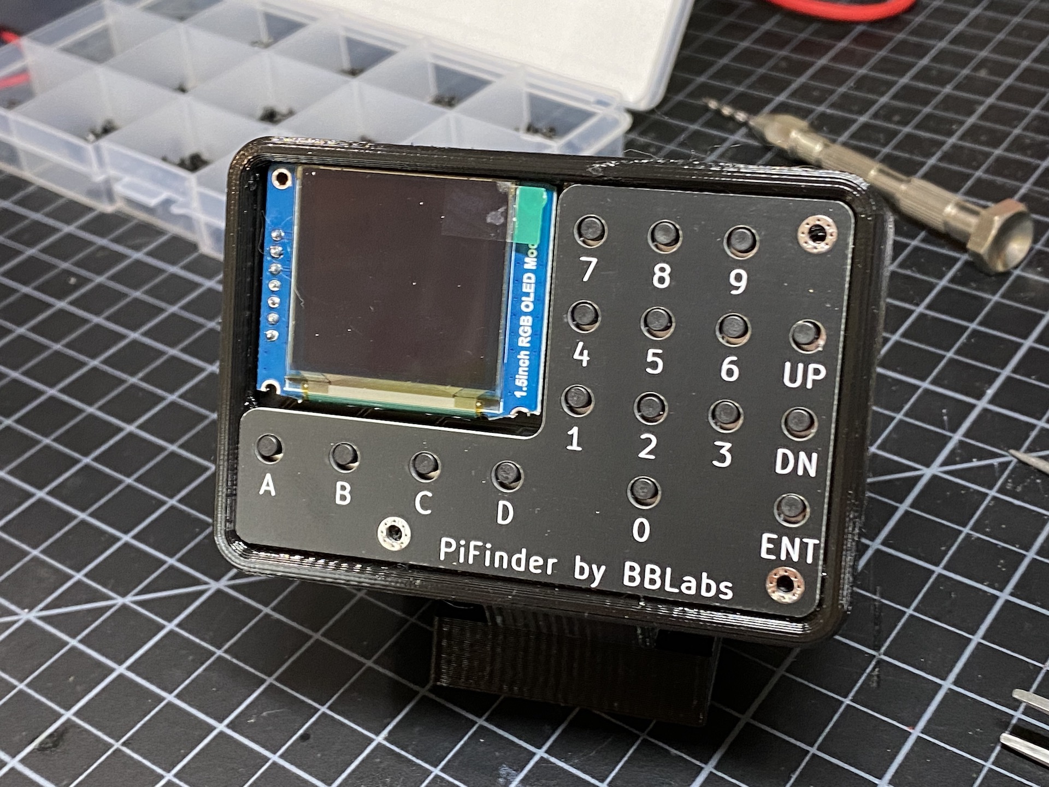
images/build_guide/IMG_4721.jpeg
