brickbots/PiFinder/images/build_guide/IMG_4725.jpeg

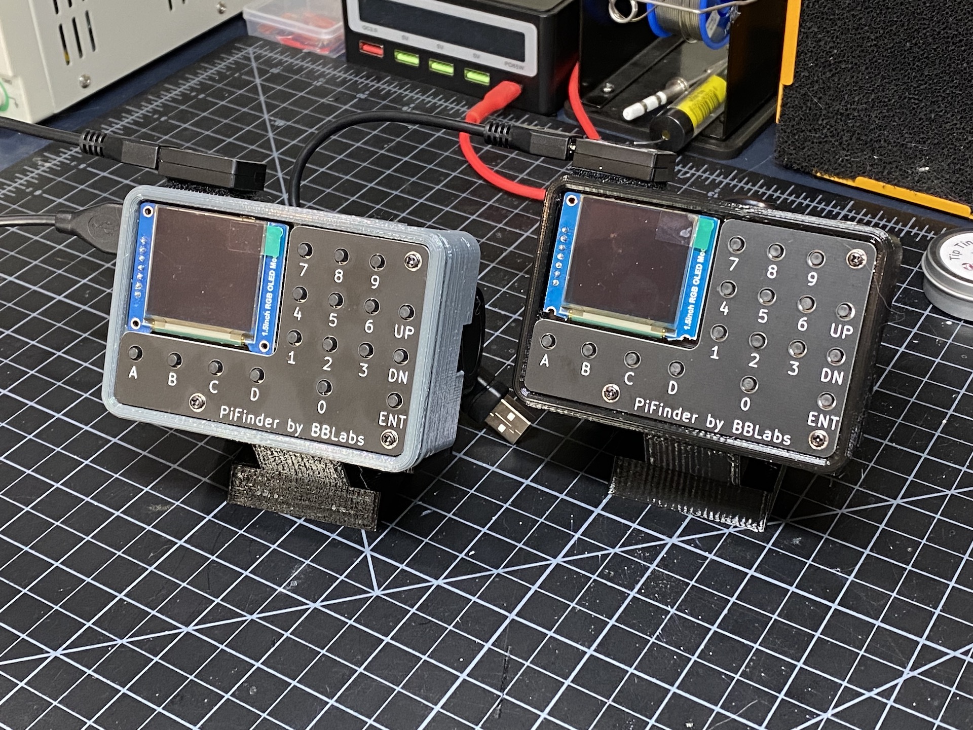
images/build_guide/IMG_4725.jpeg
