brickbots/PiFinder/images/build_guide/IMG_4808.jpeg

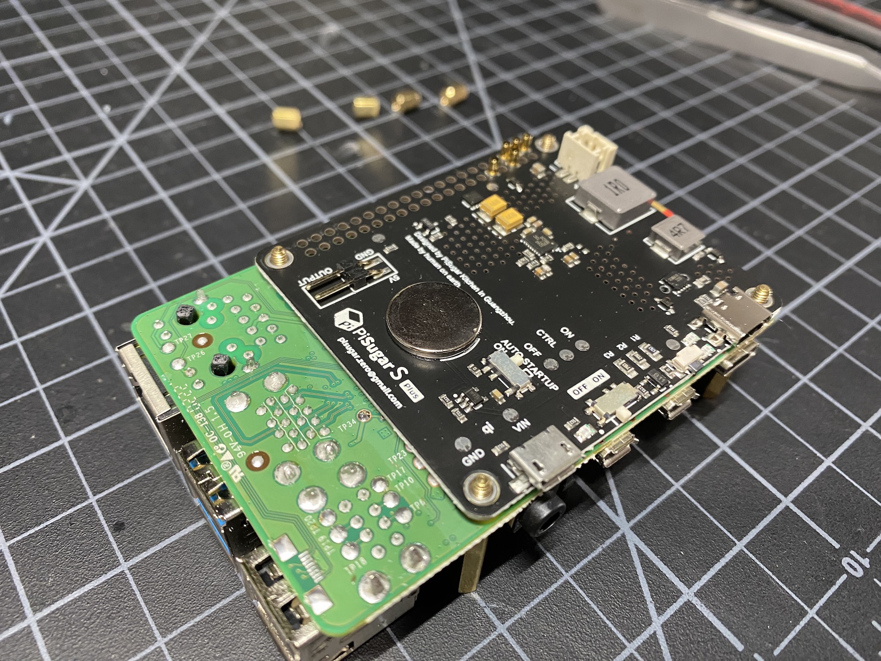
images/build_guide/IMG_4808.jpeg
