brickbots/PiFinder/images/build_guide/IMG_4809.jpeg

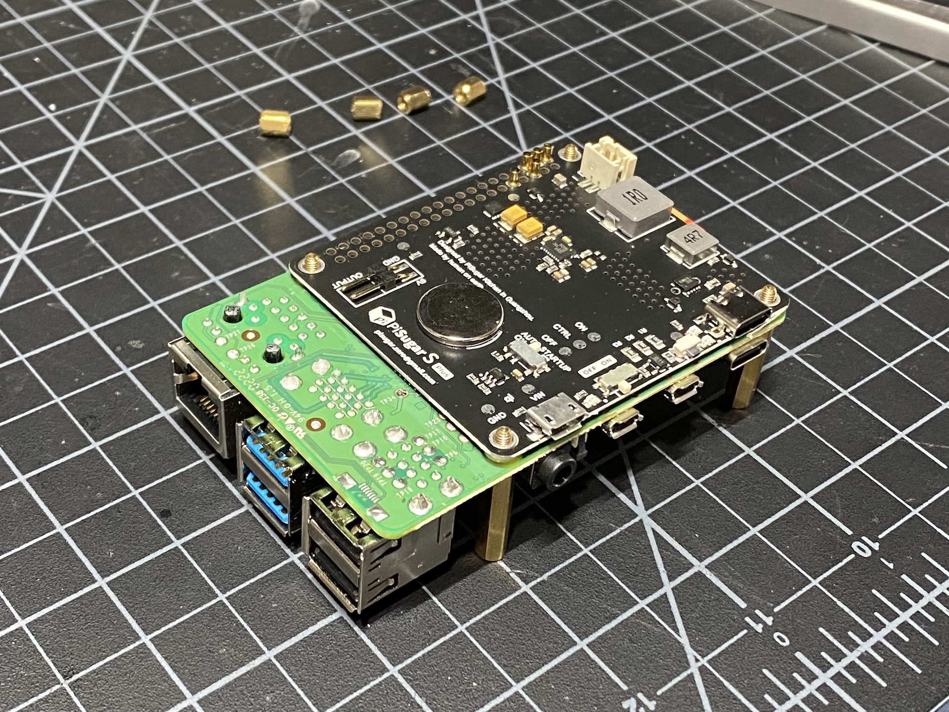
images/build_guide/IMG_4809.jpeg
