brickbots/PiFinder/images/build_guide/IMG_4810.jpeg

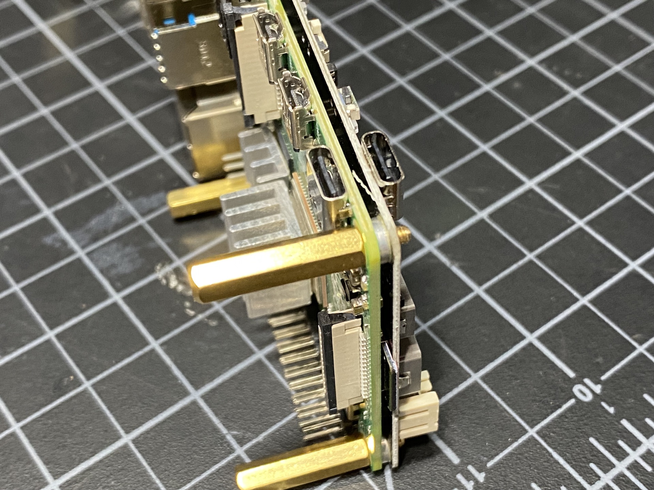
images/build_guide/IMG_4810.jpeg
