brickbots/PiFinder/images/build_guide/IMG_4812.jpeg

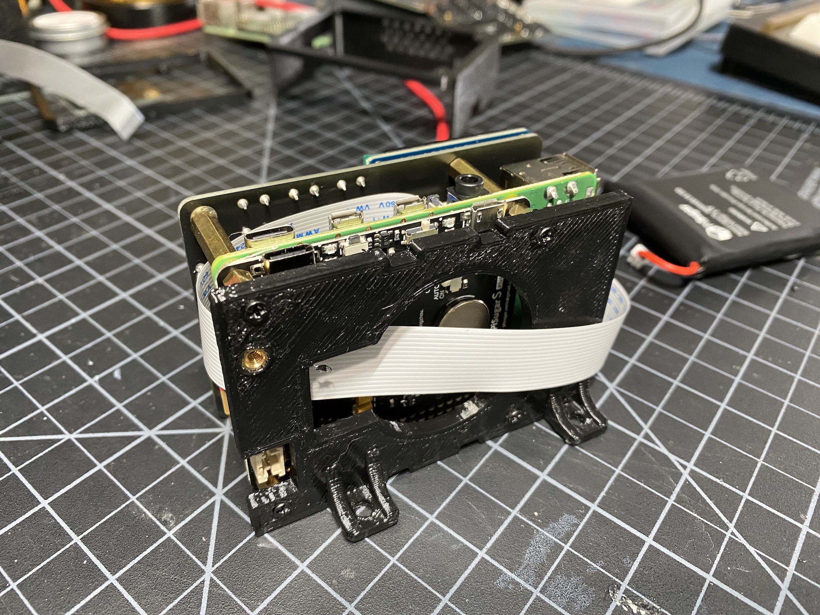
images/build_guide/IMG_4812.jpeg
