brickbots/PiFinder/images/build_guide/IMG_4813.jpeg

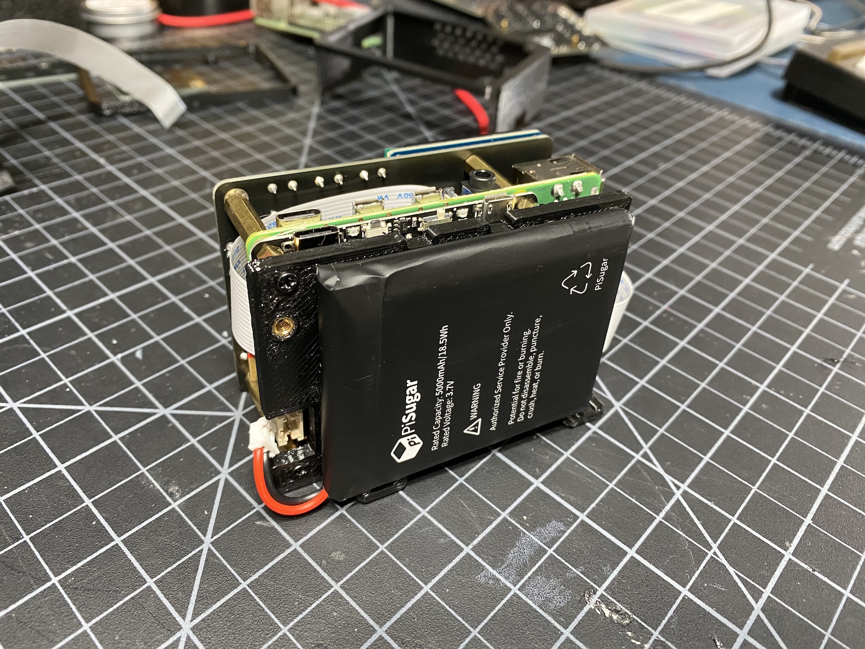
images/build_guide/IMG_4813.jpeg
