brickbots/PiFinder/images/build_guide/IMG_4816.jpeg

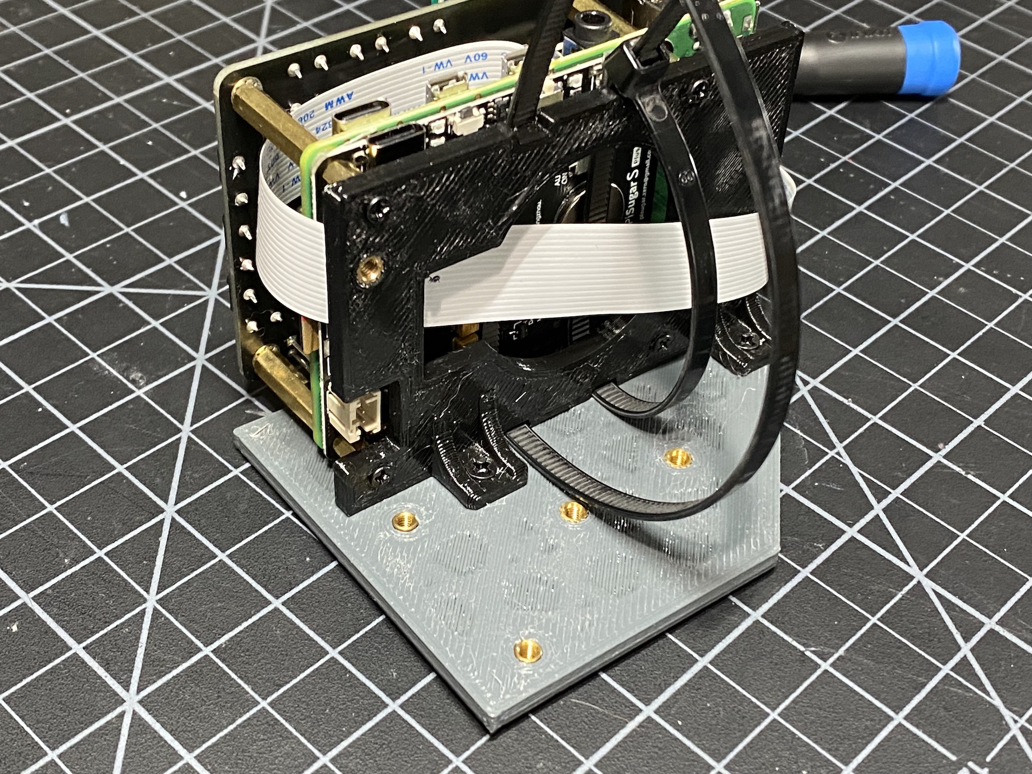
images/build_guide/IMG_4816.jpeg
