brickbots/PiFinder/images/build_guide/IMG_4817.jpeg

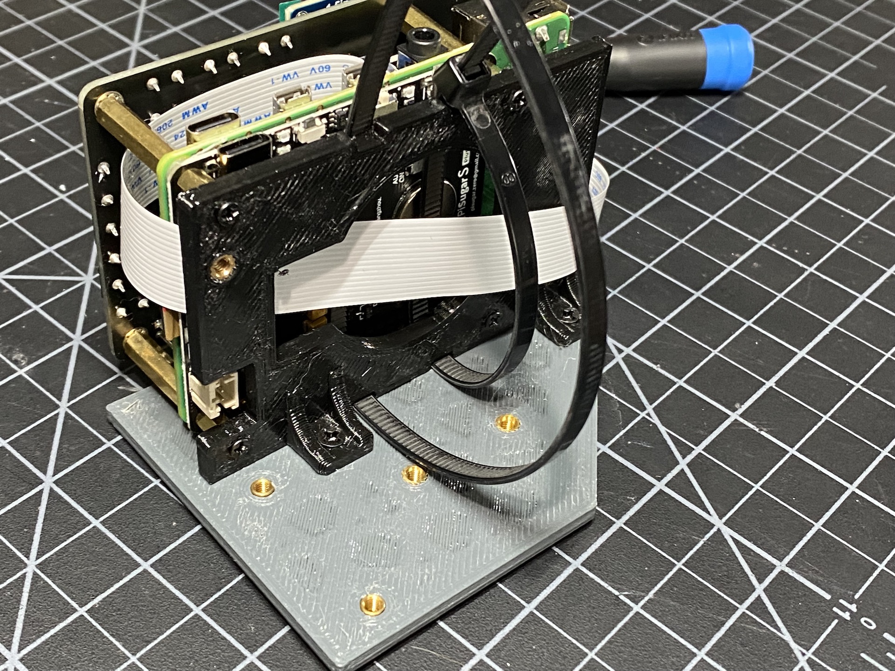
images/build_guide/IMG_4817.jpeg
