brickbots/PiFinder/images/build_guide/IMG_4820.jpeg

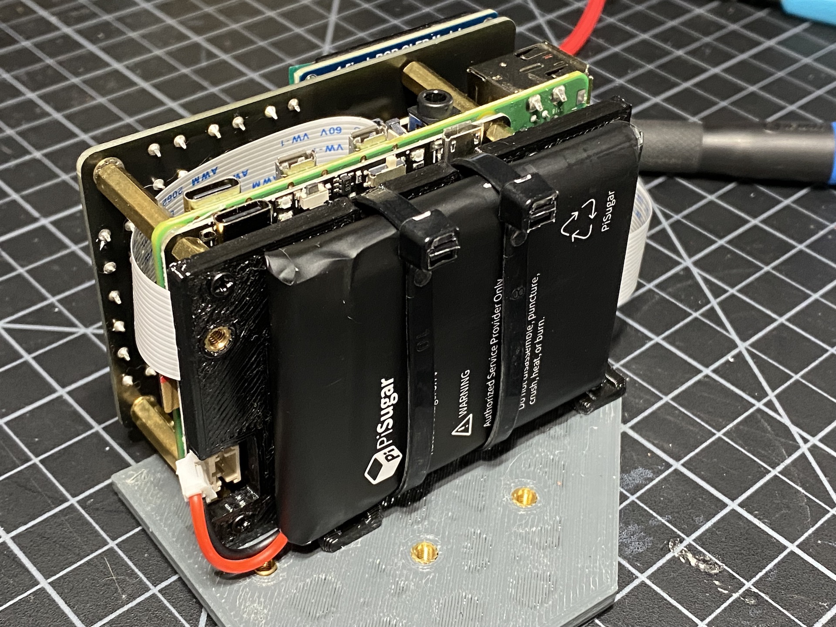
images/build_guide/IMG_4820.jpeg
