brickbots/PiFinder/images/build_guide/IMG_4822.jpeg

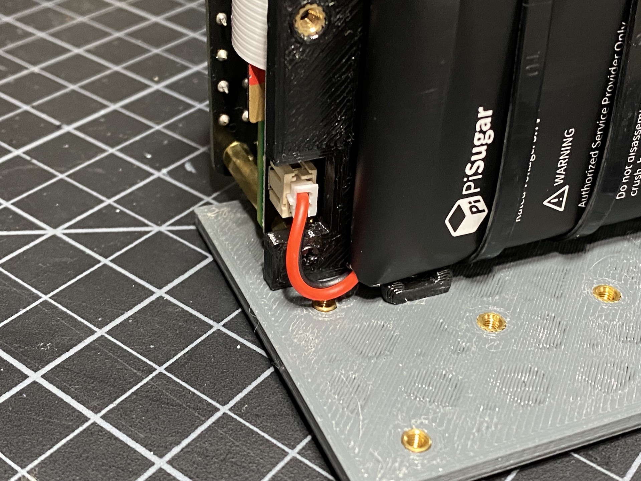
images/build_guide/IMG_4822.jpeg
