brickbots/PiFinder/images/build_guide/IMG_4824.jpeg

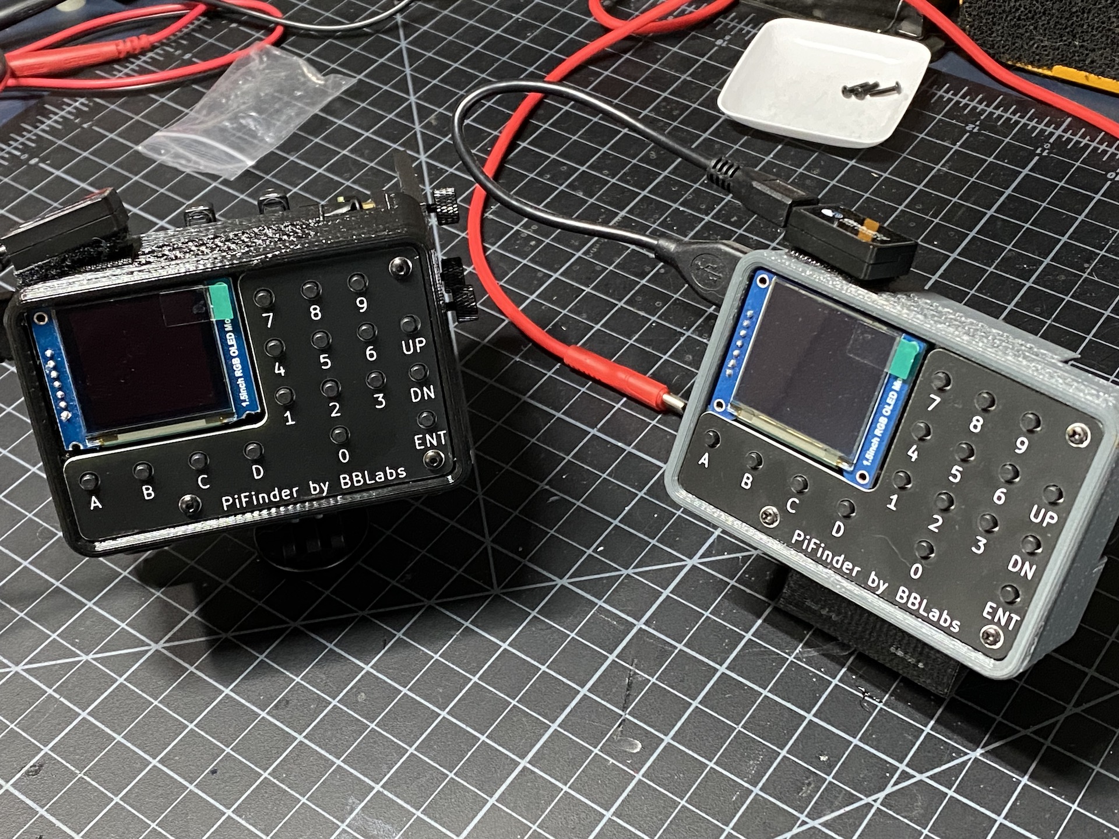
images/build_guide/IMG_4824.jpeg
