brickbots/PiFinder/images/build_guide/IMG_4825.jpeg

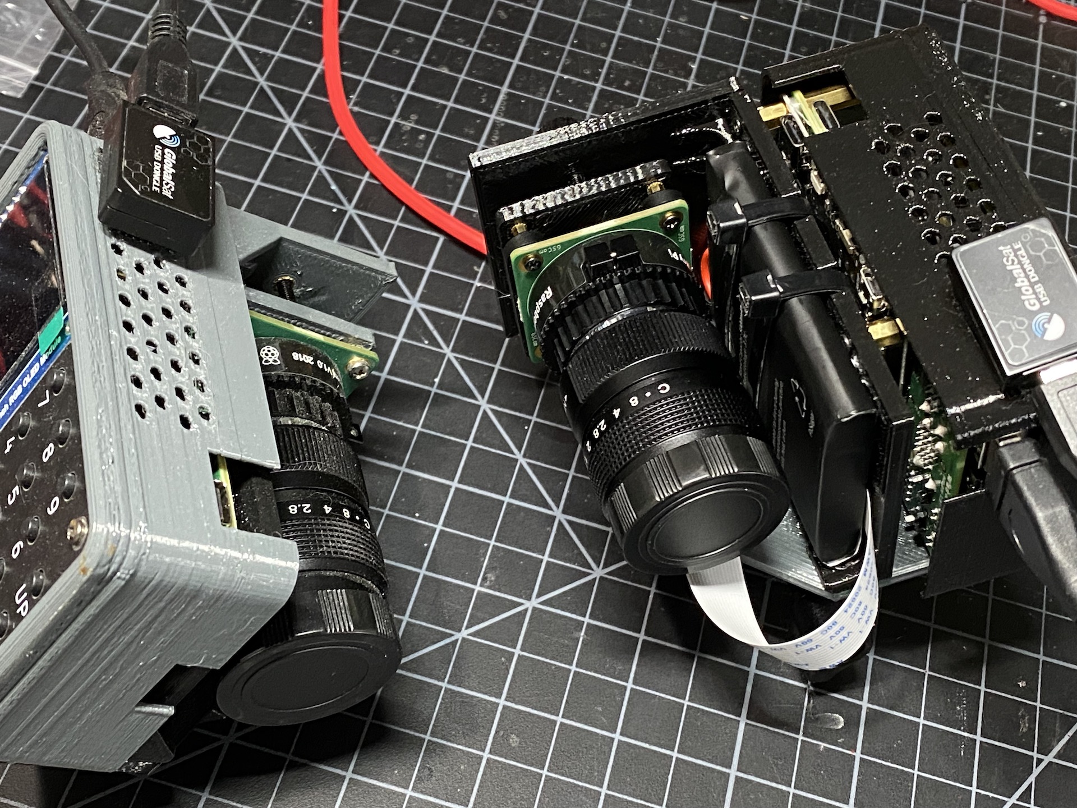
images/build_guide/IMG_4825.jpeg
