brickbots/PiFinder/images/build_guide/IMG_4826.jpeg

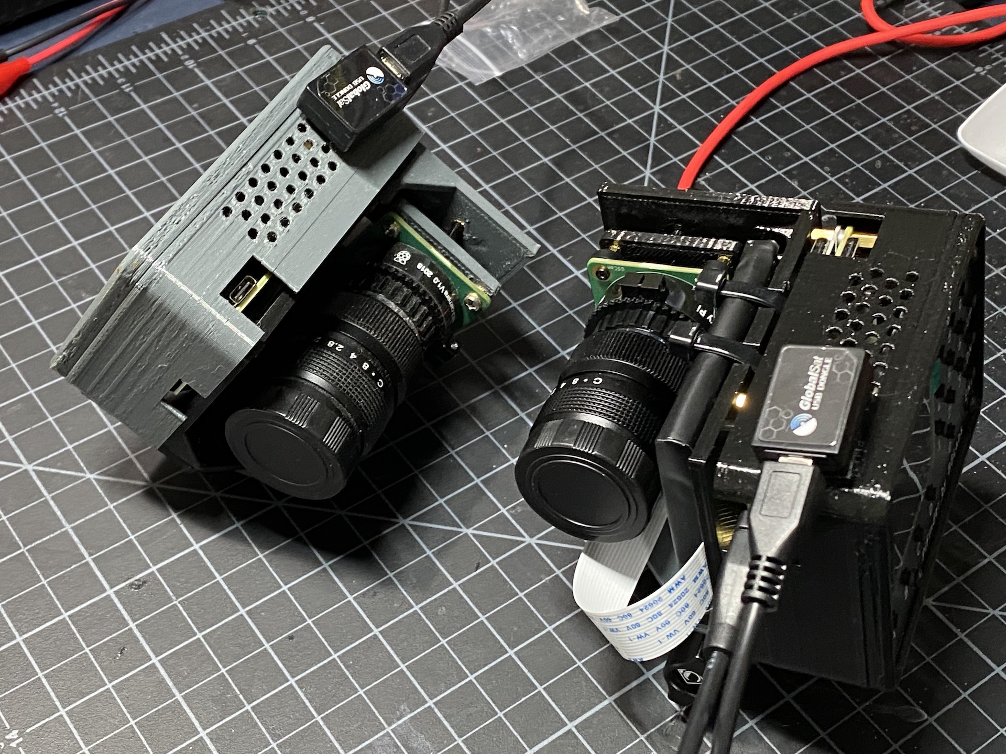
images/build_guide/IMG_4826.jpeg
