brickbots/PiFinder/images/build_guide/IMG_4827.jpeg

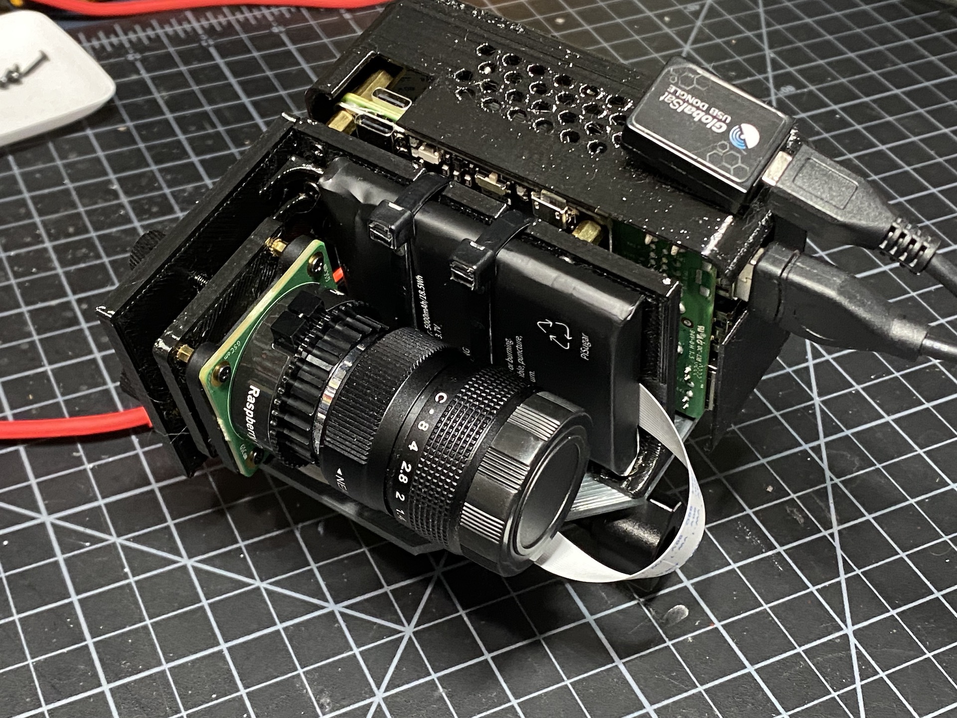
images/build_guide/IMG_4827.jpeg
