brickbots/PiFinder/images/build_guide/IMG_4828.jpeg

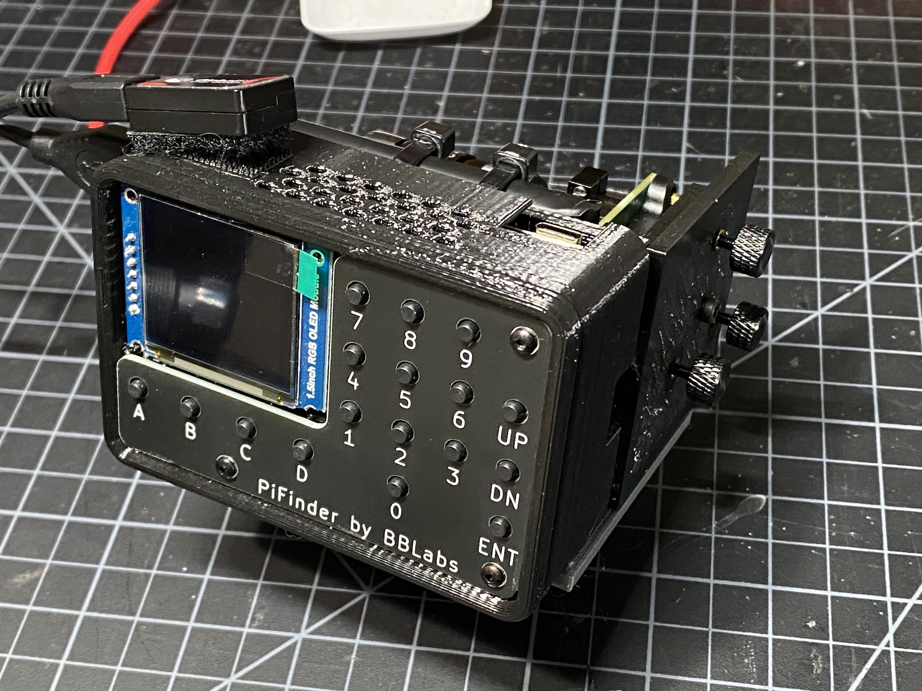
images/build_guide/IMG_4828.jpeg
