brickbots/PiFinder/images/build_guide/IMG_4830.jpeg

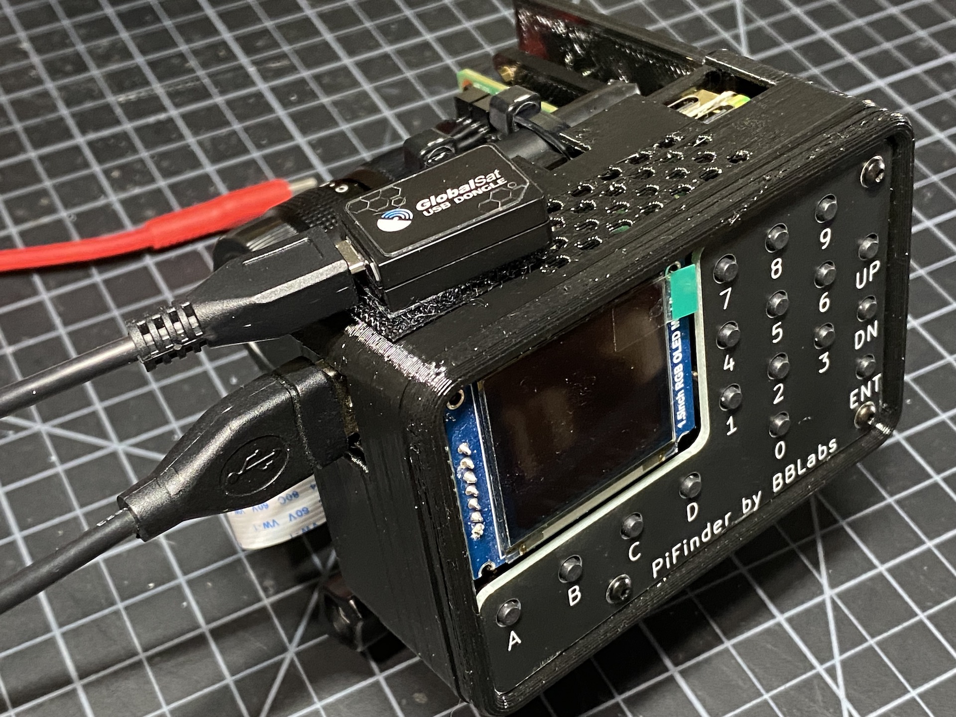
images/build_guide/IMG_4830.jpeg
