brickbots/PiFinder/images/build_guide/led_build_02.jpeg

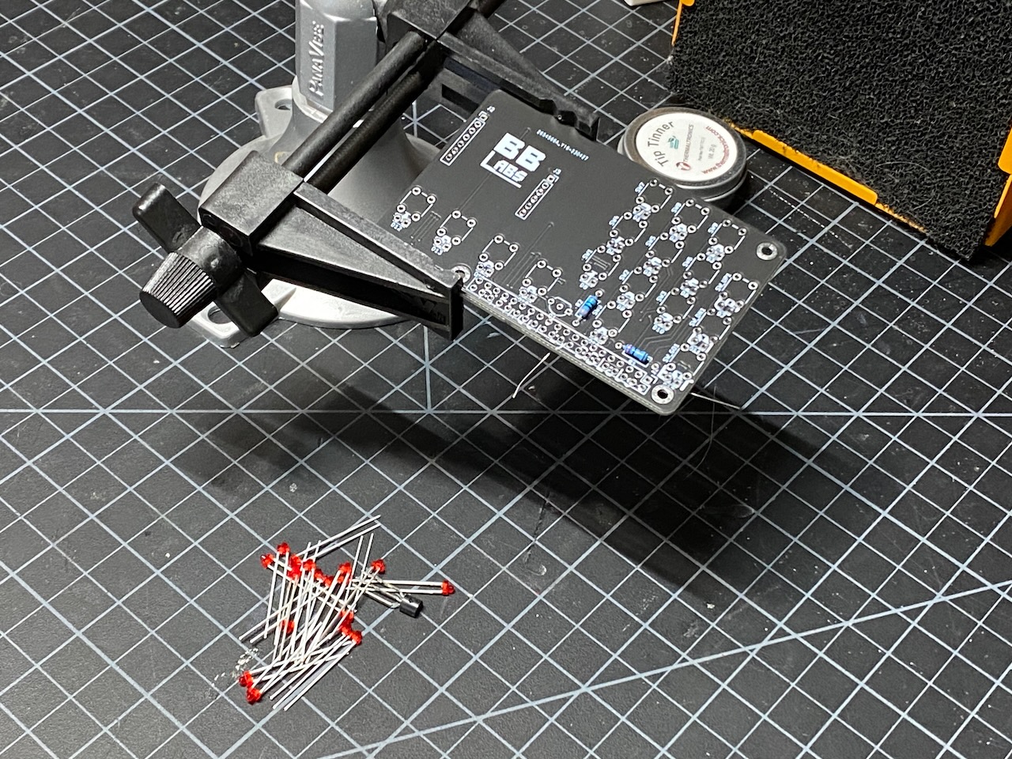
images/build_guide/led_build_02.jpeg
