brickbots/PiFinder/images/build_guide/led_build_04.jpeg

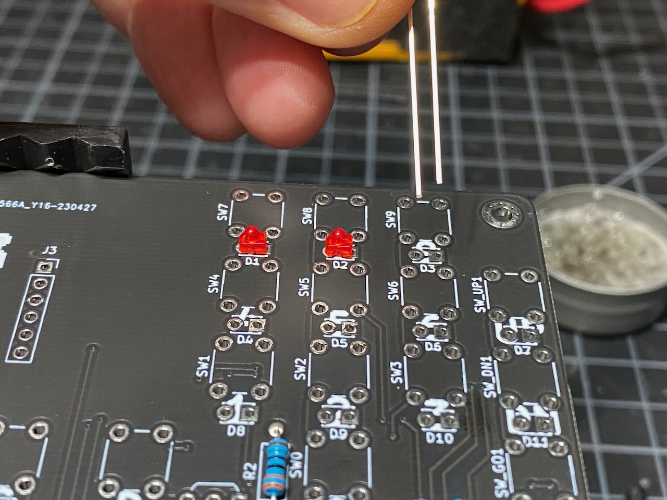
images/build_guide/led_build_04.jpeg
