brickbots/PiFinder/images/build_guide/led_build_05.jpeg

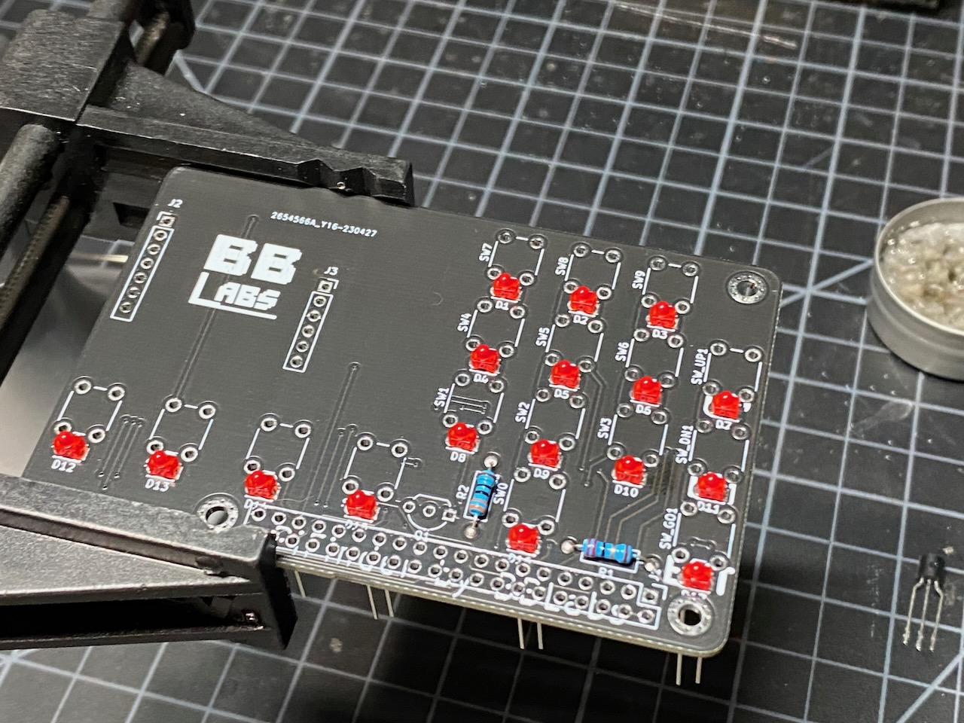
images/build_guide/led_build_05.jpeg
