brickbots/PiFinder/images/build_guide/led_build_06.jpeg

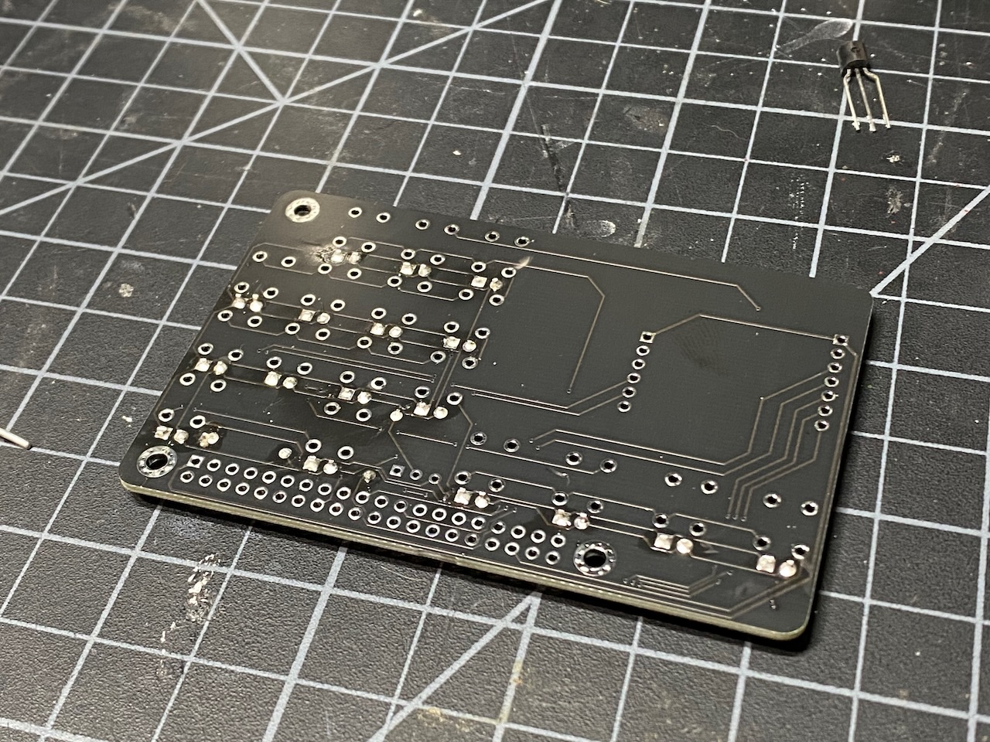
images/build_guide/led_build_06.jpeg
