brickbots/PiFinder/images/build_guide/led_build_09.jpeg

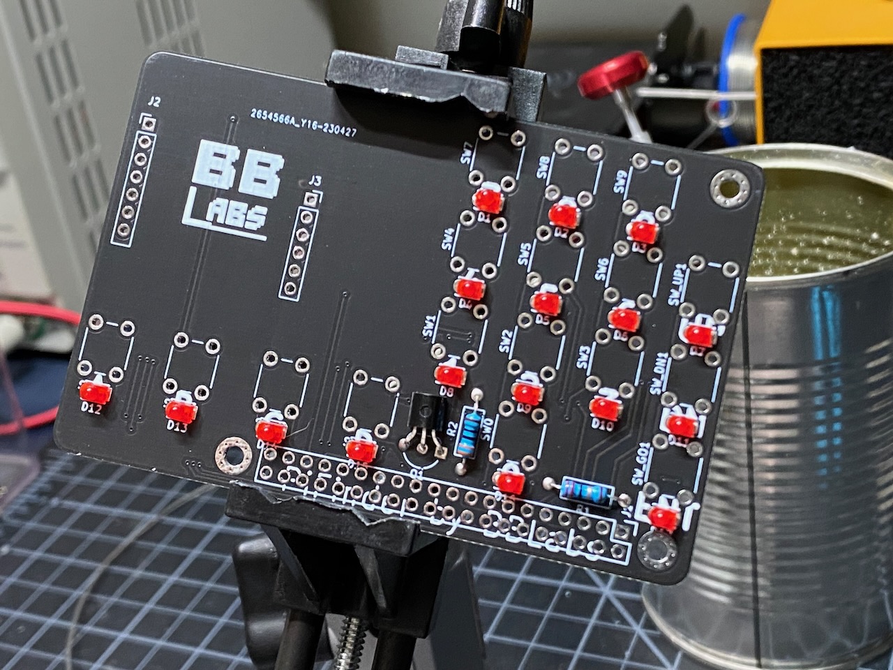
images/build_guide/led_build_09.jpeg
