brickbots/PiFinder/images/build_guide/led_build_11.jpeg

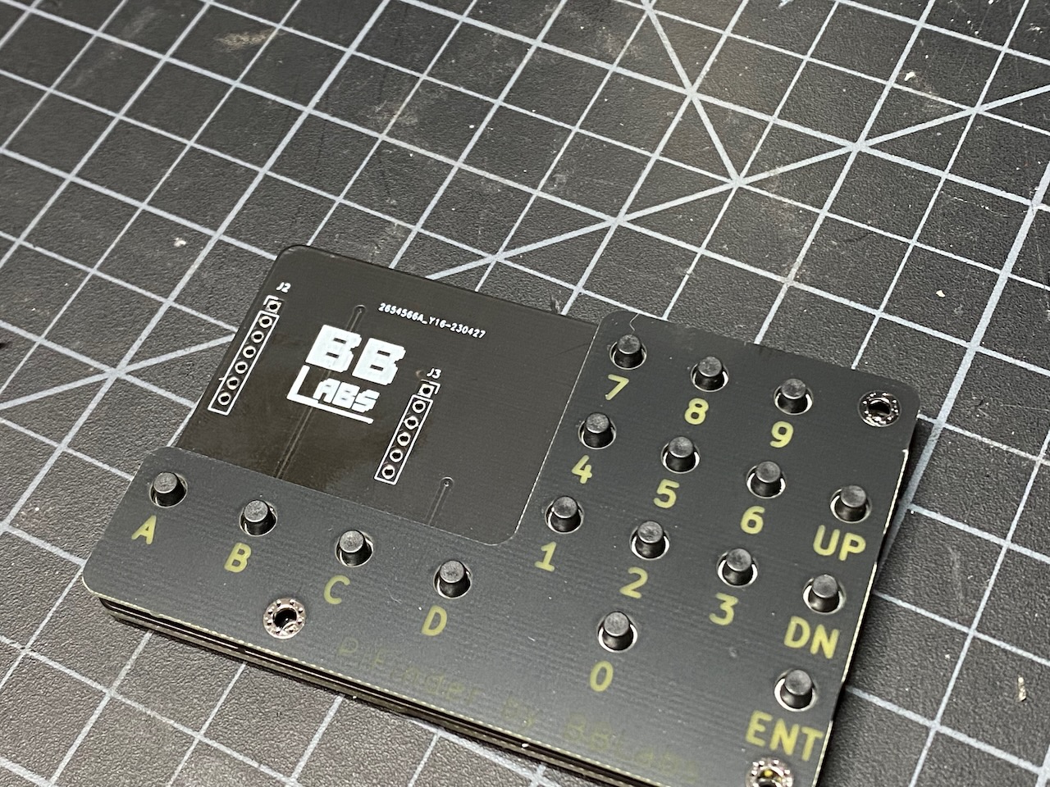
images/build_guide/led_build_11.jpeg
