brickbots/PiFinder/images/build_guide/v1.6/build_guide_26.jpeg

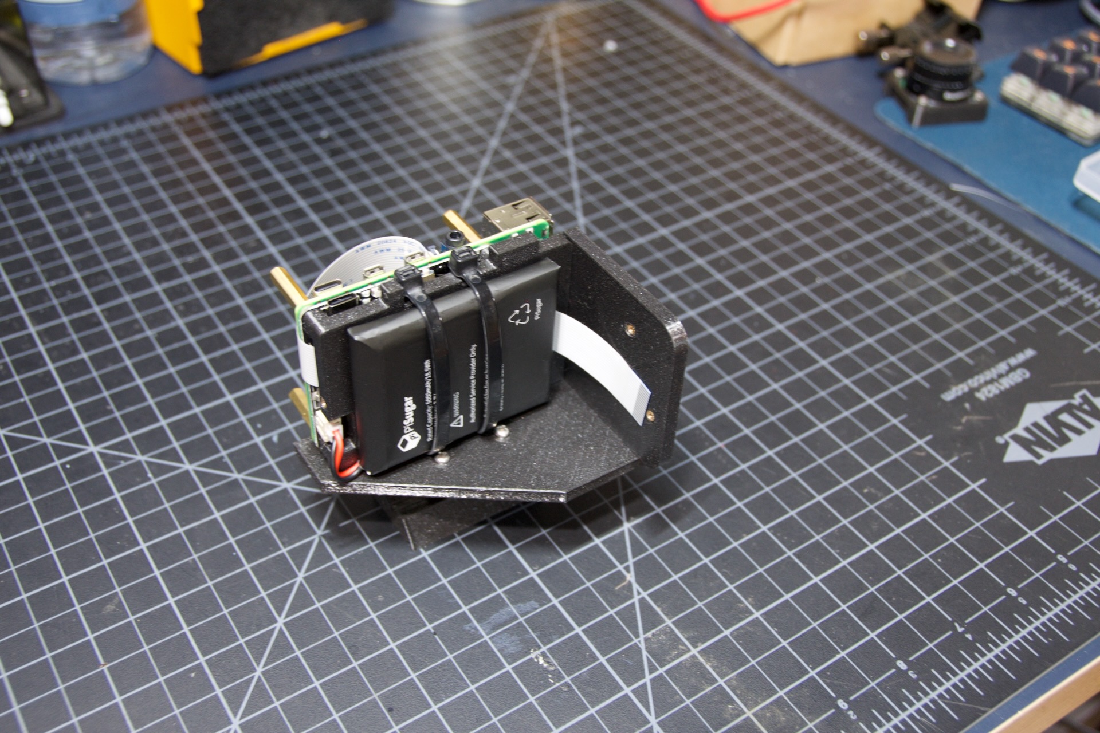
images/build_guide/v1.6/build_guide_26.jpeg
