brickbots/PiFinder/images/screenshots/how_to_see_CATALOG_004.png

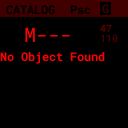
images/screenshots/how_to_see_CATALOG_004.png
