brickbots/PiFinder/images/screenshots/how_to_see_CHART_001_docs.png

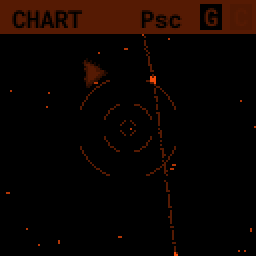
images/screenshots/how_to_see_CHART_001_docs.png
