brickbots/PiFinder/images/screenshots/how_to_see_LOG_001.png

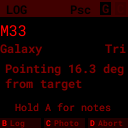
images/screenshots/how_to_see_LOG_001.png
