brickbots/PiFinder/images/screenshots/how_to_see_OPTIONS_003.png

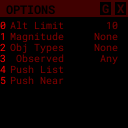
images/screenshots/how_to_see_OPTIONS_003.png
