brickbots/PiFinder/images/screenshots/how_to_see_OPTIONS_004_docs.png

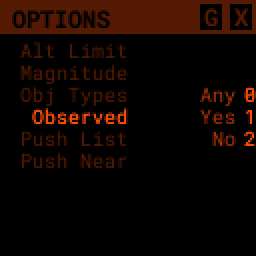
images/screenshots/how_to_see_OPTIONS_004_docs.png
