brickbots/PiFinder/images/screenshots/how_to_see_OPTIONS_005.png

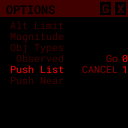
images/screenshots/how_to_see_OPTIONS_005.png
