brickbots/PiFinder/images/user_guide/ui_reference.png

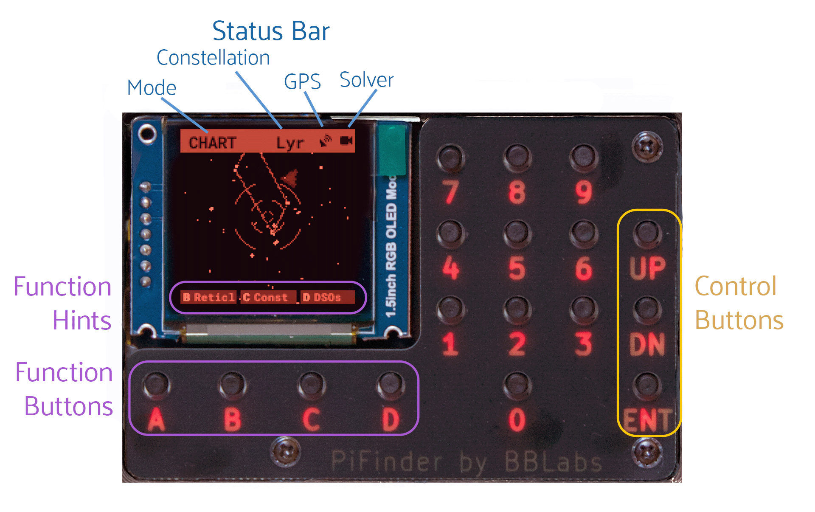
images/user_guide/ui_reference.png
