brickbots/PiFinder/docs/user_guide_faq.md

# PiFinder User Manual - FAQ

Please see our new documentation at:
[pifinder.readthedocs.io](https://pifinder.readthedocs.io/en/release/user_guide.html#faq)
