brickbots/PiFinder/python/PiFinder/state.py

#!/usr/bin/python
# -*- coding:utf-8 -*-
"""
This module contains the shared state
object.
"""

import time
import datetime
import pickle
import pytz
from PiFinder import config
import logging
from typing import List
from PiFinder.composite_object import CompositeObject
from PiFinder.types.positioning import PointingEstimate
from typing import Optional
from dataclasses import dataclass, asdict
import json
from timezonefinder import TimezoneFinder

logger = logging.getLogger("SharedState")


class RecentCompositeObjectList(list):
    """keeps the recent list of composite_objects,
    handling duplicates"""

    def __init__(self):
        super().__init__()

    def append(self, item: CompositeObject) -> None:
        # Remove the item if it's already in the list
        try:
            super().remove(item)
        except ValueError:
            pass

        # Add the item to the end of the list
        super().append(item)

    def __iter__(self):
        return super().__iter__()

    def __repr__(self) -> str:
        return f"RecentList({super().__repr__()})"

    def __str__(self) -> str:
        return super().__str__()


class UIState:
    def __init__(self):
        self.__observing_list = []
        self.__recent = RecentCompositeObjectList()
        self.__target = None
        self.__message_timeout = 0
        self.__hint_timeout = 0
        self.__show_fps = False
        # Set to true when an object is pushed
        # to the recent list from the pos_server
        # proccess (i.e. skysafari goto).  Used
        # to jump from object list to object details
        self.__new_pushto = False

    def observing_list(self):
        return self.__observing_list

    def set_observing_list(self, v):
        self.__observing_list = v

    def recent_list(self) -> List[CompositeObject]:
        return list(reversed(self.__recent))

    def add_recent(self, v: CompositeObject):
        self.__recent.append(v)

    def set_new_pushto(self, v: bool):
        self.__new_pushto = v

    def new_pushto(self) -> bool:
        return self.__new_pushto

    def target(self):
        return self.__target

    def set_target(self, v):
        self.__target = v

    def message_timeout(self):
        return self.__message_timeout

    def set_message_timeout(self, v):
        self.__message_timeout = v

    def hint_timeout(self):
        return self.__hint_timeout

    def set_hint_timeout(self, v):
        self.__hint_timeout = v

    def show_fps(self):
        return self.__show_fps

    def set_show_fps(self, v: bool):
        self.__show_fps = v

    def __str__(self):
        return str(
            {
                "recent": self.__recent,
                "hint_timeout": self.__hint_timeout,
                "show_fps": self.__show_fps,
                "observing_list": self.__observing_list,
                "target": self.__target,
                "message_timeout": self.__message_timeout,
            }
        )

    def __repr__(self):
        return self.__str__()


"""
Example shared_state object:

SharedStateObj(
    power_state=1,
    solve_state=True,
    solution=PointingEstimate(
        pointing=PointingMatrix(
            camera=PointingAxis(
                solve=Pointing(RA=22.866, Dec=15.347, Roll=306.295),
                estimate=Pointing(RA=22.866, Dec=15.347, Roll=306.295),
            ),
            aligned=PointingAxis(
                solve=Pointing(RA=22.866, Dec=15.347, Roll=306.295),
                estimate=Pointing(RA=22.866, Dec=15.347, Roll=306.295),
            ),
        ),
        imu_anchor=<quaternion>,
        Alt=None, Az=None,
        solve_source=SolveSource.CAMERA,
        estimate_time=1695297930.5532792,
        constellation='Psc',
        diagnostics=SolveDiagnostics(Matches=12, RMSE=21.99, FOV=10.20, ...),
        alignment=AlignmentResult(x_target=None, y_target=None),
    ),
    imu=ImuSample(quat=<quaternion>, timestamp=1695297930.55, status=3, moving=False),
    location=Location(lat=59.05, lon=7.99, altitude=151.4, source='GPS', ...),
    datetime=None,
    screen=<PIL.Image.Image image mode=RGB size=128x128 at 0xE693C910>,
    target_pixel=[305.697, 351.944]
)
"""


@dataclass
class SQM:
    """
    Sky Quality Meter - represents the sky brightness measurement.
    """

    value: float = 20.15  # mag/arcsec² - default typical dark sky value
    source: str = "None"  # "None", "Radiometer", "Manual", legacy "Calculated"
    last_update: Optional[str] = None  # ISO timestamp of last update

    def __str__(self):
        return (
            f"SQM(value={self.value:.2f} mag/arcsec², "
            f"source={self.source}, "
            f"last_update={self.last_update or 'Never'})"
        )

    def to_dict(self):
        """Convert the SQM object to a dictionary."""
        return asdict(self)

    def to_json(self):
        """Convert the SQM object to a JSON string."""
        return json.dumps(self.to_dict())

    @classmethod
    def from_dict(cls, data):
        """Create an SQM object from a dictionary."""
        return cls(**data)

    @classmethod
    def from_json(cls, json_str):
        """Create an SQM object from a JSON string."""
        data = json.loads(json_str)
        return cls.from_dict(data)


@dataclass
class Location:
    """
    the location of the observer, lat/lon/altitude and the source of the data.
    """

    lat: float = 0.0
    lon: float = 0.0
    altitude: float = 0.0
    source: str = "None"
    lock: bool = False  # lock means: we received a good enough location, not a GPS Fix
    lock_type: int = 0  # limited, basic, accurate, precise
    error_in_m: float = 0.0
    timezone: Optional[str] = "UTC"
    last_gps_lock: Optional[str] = None

    def __str__(self):
        return (
            f"Location(lat={self.lat:.6f}, "
            f"lon={self.lon:.6f}, "
            f"alt={self.altitude:.1f}m, "
            f"source={self.source}, "
            f"error={self.error_in_m:.1f}m, "
            f"lock={'Yes' if self.lock else 'No'} "
            f"lock_type={self.lock_type}, "
            f"{f', tz={self.timezone}' if self.timezone else ''}"
            f"{f', last_lock={self.last_gps_lock}' if self.last_gps_lock else ''})"
        )

    @staticmethod
    def make_fix(
        lat: float, lon: float, altitude: float = 0, source: str = "MANUAL"
    ) -> tuple:
        """Build a GPS fix message tuple for the gps_queue."""
        return (
            "fix",
            {
                "lat": lat,
                "lon": lon,
                "altitude": altitude,
                "error_in_m": 0,
                "source": source,
                "lock": True,
                "lock_type": 2,
            },
        )

    def reset(self):
        self.lat = 0.0
        self.lon = 0.0
        self.altitude = 0.0
        self.source = "None"
        self.lock = False
        self.lock_type = 0
        self.error_in_m = 0
        self.timezone = "UTC"
        self.last_gps_lock = None

    def to_dict(self):
        """Convert the Location object to a dictionary."""
        return asdict(self)

    def to_json(self):
        """Convert the Location object to a JSON string."""
        return json.dumps(self.to_dict())

    @classmethod
    def from_dict(cls, data):
        """Create a Location object from a dictionary."""
        return cls(**data)

    @classmethod
    def from_json(cls, json_str):
        """Create a Location object from a JSON string."""
        data = json.loads(json_str)
        return cls.from_dict(data)


class SharedStateObj:
    def __init__(self) -> None:
        self.__power_state = 1  # 0 = sleep state, 1 = awake state
        # self.__solve_state
        # None = No solve attempted yet
        # True = Valid solve data from either IMU or Camera
        # False = Invalid solve data
        self.__solve_state: Optional[bool] = None
        self.__ui_state = None
        self.__last_image_metadata = {
            "exposure_start": 0,
            "exposure_end": 0,
            "exposure_time": 500000,  # Default exposure time in microseconds (0.5s)
            "imu": None,
            "imu_delta": 0.0,  # Angle between quaternion at start and end of exposure [deg]
        }
        self.__solution: PointingEstimate = PointingEstimate()
        self.__sats = None
        self.__gps_comms = None
        self.__imu = None
        self.__battery = None
        self.__hardware = None
        self.__location: Location = Location()
        self.__sqm: SQM = SQM()
        # Processed 8-bit background floor used by the camera controller.
        # Raw SQM thresholds use different units and must not be stored here.
        self.__noise_floor: float = 10.0
        self.__sqm_details: dict = {}  # Full SQM calculation details for calibration
        self.__datetime = None
        self.__datetime_time = None
        self.__datetime_manual = False  # True when manually set, blocks GPS overrides
        self.__screen = None
        self.__target_pixel = config.Config().get_option("target_pixel")
        self.__arch = None
        self.__camera_align = False
        self.__camera_type = "imx296"  # Default, will be set by camera process
        # Configured lens, the half of the optical train nothing can detect.
        # None means "not stated", which resolves to the sensor's shipped lens
        # -- that is what lets installs predating this setting keep working.
        self.__camera_lens = config.Config().get_option("camera_lens")
        # Whether the frames arriving actually came through the optics the two
        # halves above describe. True until a camera says otherwise, so the
        # window before the camera process reports behaves like the hardware
        # case rather than silently dropping the FOV gate on every boot.
        self.__optical_train_known = True
        # Degrees the camera process rotates the solve/display image relative
        # to the stored raw frame (PIL CCW). None until the camera reports.
        self.__solve_image_rotation = None
        self.__cam_raw = None
        self.__sqm_radiometer_sample = None
        # Are we prepared to do alt/az math
        # We need gps lock and datetime
        self.__tz_finder = TimezoneFinder()
        self.__current_ui_state = None

    def serialize(self, output_file):
        with open(output_file, "wb") as f:
            pickle.dump(self, f)

    def altaz_ready(self):
        return bool(self.__location.lock and self.datetime())

    def target_pixel(self, screen_space=False):
        """
        target_pixel is (Y,X) in camera image (512x512) space

        if screen_space=True, this is returned as (X,Y) in screen (128x128) space
        """
        if screen_space:
            return (int(self.__target_pixel[1] / 4), int(self.__target_pixel[0] / 4))
        return self.__target_pixel

    def set_target_pixel(self, coords):
        self.__target_pixel = coords

    def power_state(self):
        return self.__power_state

    def set_power_state(self, v):
        """
        Sets the power_state. Allowed states are 0 (sleep) or 1 (awake). If
        the input v is any other value, power_state will be unchanged.
        """
        if v in (0, 1):
            self.__power_state = v
        else:
            logger.error(
                f"Invalid value for set_power_state: {v}. power_state not changed."
            )

    def arch(self):
        return self.__arch

    def set_arch(self, v):
        self.__arch = v

    def solve_state(self):
        return self.__solve_state

    def set_solve_state(self, v):
        self.__solve_state = v

    def camera_align(self):
        return self.__camera_align

    def set_camera_align(self, v: bool):
        self.__camera_align = v

    def camera_type(self):
        return self.__camera_type

    def solve_image_rotation(self):
        return self.__solve_image_rotation

    def set_solve_image_rotation(self, v):
        self.__solve_image_rotation = v

    def set_camera_type(self, v: str):
        self.__camera_type = v

    def camera_lens(self) -> Optional[str]:
        """Configured lens key, or None when the config states none."""
        return self.__camera_lens

    def set_camera_lens(self, v: Optional[str]):
        """Publish a lens change so the solver picks it up on the next frame.

        The solver derives its FOV gate from this, so it must be the key of a
        registered lens (see PiFinder.optics.LENSES) or None.
        """
        self.__camera_lens = v

    def optical_train_known(self) -> bool:
        """False when the frames did not come through this device's optics.

        See ``CameraInterface.optical_train_known``. Read alongside
        ``camera_type``/``camera_lens`` rather than instead of them: the train
        still resolves, it just does not describe the frames.
        """
        return self.__optical_train_known

    def set_optical_train_known(self, v: bool):
        self.__optical_train_known = bool(v)

    def sats(self):
        return self.__sats

    def set_sats(self, v):
        self.__sats = v

    def gps_comms(self):
        """The most recent GPS event as ``(name, monotonic_stamp)``, or None
        when nothing has been received this session. The name is a message
        class (``NAV-SOL``) or a marker (``?CKSUM``). The stamp is the main
        process's ``time.monotonic()`` reading when the event was drained off
        ``gps_queue``, so only that process can meaningfully subtract it --
        see docs/ax/gps/CONTEXT.md."""
        return self.__gps_comms

    def set_gps_comms(self, v):
        self.__gps_comms = v

    def imu(self):
        return self.__imu

    def set_imu(self, v):
        self.__imu = v

    def battery(self):
        """Latest BatteryState, or None when no charger is present
        (rev3 hardware / monitor not running). None is distinct from a
        low state_of_charge_pct -- see docs/ax/battery/CONTEXT.md."""
        return self.__battery

    def set_battery(self, v):
        self.__battery = v

    def hardware(self):
        """Detected HardwareCapabilities for this board."""
        return self.__hardware

    def set_hardware(self, v):
        self.__hardware = v

    def solution(self) -> PointingEstimate:
        return self.__solution

    def set_solution(self, v: PointingEstimate):
        self.__solution = v
        # solve_state is the cheap-to-poll cache of "does a current pointing
        # exist?" -- exactly solution().has_pointing(). Derive it here so the
        # two can never drift and callers can't forget to update it.
        self.__solve_state = v.has_pointing()

    def location(self):
        """Return the current location"""
        return self.__location

    def set_location(self, v):
        # if value is not none, set the timezone
        # before saving the value.
        #
        # timezone_at() returns None for coordinates it cannot resolve, and
        # assigning that raw would overwrite Location's "UTC" default with a
        # value every reader has to guard: pytz.timezone(None) raises
        # UnknownTimeZoneError, so an unresolved zone would crash the manual
        # time-entry callbacks rather than degrade. UTC is already the
        # documented fallback for an unknown zone (see local_datetime /
        # ADR-0018), so settle it here and keep the field a usable zone name.
        if v:
            v.timezone = self.__tz_finder.timezone_at(lat=v.lat, lng=v.lon) or "UTC"
        self.__location = v

    def sqm(self):
        """Return the current SQM object"""
        return self.__sqm

    def set_sqm(self, sqm: SQM):
        """Update the SQM value"""
        self.__sqm = sqm

    def noise_floor(self) -> float:
        """Return the processed-image background floor in 8-bit ADU."""
        return self.__noise_floor

    def set_noise_floor(self, v: float):
        """Update the processed-image background floor in 8-bit ADU."""
        self.__noise_floor = v

    def sqm_details(self) -> dict:
        """Return the full SQM calculation details"""
        return self.__sqm_details

    def set_sqm_details(self, v: dict):
        """Update the SQM calculation details"""
        self.__sqm_details = v

    def get_sky_brightness(self):
        """Return just the numeric SQM value for convenience"""
        return self.__sqm.value

    def last_image_metadata(self):
        return self.__last_image_metadata

    def set_last_image_metadata(self, v):
        self.__last_image_metadata = v

    def datetime(self):
        """The civil datetime (astronomical epoch), timezone-aware in UTC.

        Always UTC-aware: ``set_datetime`` normalises every input to UTC, so
        the value is safe to feed to skyfield/ephemeris math. ``None`` until a
        time is known. Prefer ``utc_datetime()`` / ``local_datetime()`` in new
        code so the intended zone is explicit at the call site. See ADR-0018.
        """
        if self.__datetime is None:
            return self.__datetime
        return self.__datetime + datetime.timedelta(
            seconds=time.time() - self.__datetime_time
        )

    def local_datetime(self):
        """The civil datetime in the active location's timezone (UTC fallback).

        Same absolute instant as ``utc_datetime()``, expressed in the
        observer's zone; falls back to UTC if no/invalid timezone. ``None``
        until a time is known. See ADR-0018.
        """
        if self.__datetime is None:
            return self.__datetime
        dt = self.datetime()
        if self.__location and self.__location.timezone:
            try:
                return dt.astimezone(pytz.timezone(self.__location.timezone))
            except (pytz.exceptions.UnknownTimeZoneError, AttributeError):
                # Fall back to UTC if timezone is invalid or None
                return dt.astimezone(pytz.utc)
        return dt.astimezone(pytz.utc)

    def utc_datetime(self):
        """The civil datetime in UTC, timezone-aware. ``None`` until known.

        The explicit UTC accessor. See ADR-0018.
        """
        if self.__datetime is None:
            return self.__datetime
        dt = self.datetime()
        return dt.astimezone(pytz.utc)

    def set_datetime(self, dt, force=False):
        """Store the civil datetime, normalised to timezone-aware UTC.

        The single write boundary for the stored civil datetime. Callers must
        pass a timezone-aware datetime; a naive value is interpreted as UTC
        (a safety net, not the contract). Aware inputs are converted to UTC.
        This keeps ``datetime()`` / ``utc_datetime()`` always UTC-aware. See
        ADR-0018.
        """
        if dt.utcoffset() is None:  # naive, assume it's UTC
            # we could use replace() instead since UTC has
            # no DST, but the idiom is dangerous for non-UTC
            dt = pytz.utc.localize(dt)
        else:  # timezone-aware -> convert to UTC
            dt = dt.astimezone(pytz.utc)

        if force:
            self.__datetime_time = time.time()
            self.__datetime = dt
            self.__datetime_manual = True
            return

        # Skip GPS time updates when time was manually set
        if self.__datetime_manual:
            return

        if self.__datetime is None:
            self.__datetime_time = time.time()
            self.__datetime = dt
        else:
            # only reset if there is some significant diff
            # as some gps recievers send multiple updates that can
            # rewind and fastforward the clock
            curtime = self.__datetime + datetime.timedelta(
                seconds=time.time() - self.__datetime_time
            )
            if curtime < dt:
                self.__datetime_time = time.time()
                self.__datetime = dt

    def reset_datetime(self):
        """Clear manual datetime override, allowing GPS time updates again."""
        self.__datetime = None
        self.__datetime_time = None
        self.__datetime_manual = False

    def screen(self):
        return self.__screen

    def set_screen(self, v):
        self.__screen = v

    def cam_raw(self):
        return self.__cam_raw

    def set_cam_raw(self, v):
        self.__cam_raw = v

    def sqm_radiometer_sample(self):
        return self.__sqm_radiometer_sample

    def set_sqm_radiometer_sample(self, v):
        self.__sqm_radiometer_sample = v

    def ui_state(self):
        return self.__ui_state

    def set_ui_state(self, v):
        self.__ui_state = v

    def current_ui_state(self):
        return self.__current_ui_state

    def set_current_ui_state(self, v):
        self.__current_ui_state = v

    def __repr__(self):
        # A simple representation showing key attributes (adjust as needed)
        return (
            f"SharedStateObj("
            f"power_state={self.__power_state}, "
            f"solve_state={self.__solve_state}, "
            f"UI_state={self.__ui_state})"
            f"solution={self.__solution}, "
            f"imu={self.__imu}, "
            f"location={self.__location}, "
            f"datetime={self.datetime()}, "
            f"screen={self.__screen}, "
            f"target_pixel={self.__target_pixel})"
        )

    def __str__(self):
        # A more human-friendly representation (adjust as needed)
        return (
            f"Shared State Object:\n"
            f"Power State: {self.__power_state}\n"
            f"Solve State: {self.__solve_state}\n"
            f"UI_state={self.__ui_state})"
            f"Solution: {self.__solution}\n"
            f"IMU: {self.__imu}\n"
            f"Battery: {self.__battery}\n"
            f"Location: {self.__location}\n"
            f"Date-Time: {self.datetime()}\n"
            f"Screen: {self.__screen}\n"
            f"Target Pixel: {self.__target_pixel}"
        )
