brickbots/PiFinder/python/PiFinder/camera_interface.py

#!/usr/bin/python
# -*- coding:utf-8 -*-
"""
This module is the camera
* Captures images
* Places preview images in queue
* Places solver images in queue
* Takes full res images on demand

"""

from typing import Tuple, Optional
from pathlib import Path
from PIL import Image
import json
import os
import random
import time
import numpy as np
import queue
import threading
import logging

from PiFinder import state_utils, timez, utils
import PiFinder.pointing_model.quaternion_transforms as qt
from PiFinder.auto_exposure import (
    ExposurePIDController,
    ExposureSNRController,
    generate_exposure_sweep,
)

logger = logging.getLogger("Camera.Interface")

# Daytime alignment uses the camera's native (driver) auto-exposure where it is
# available. On backends with no native AE (debug / non-Pi), `set_exp:native`
# falls back to this fixed short exposure -- short enough not to saturate in
# daylight while still usable for framing a distant object.
DAYTIME_AE_FALLBACK_EXPOSURE = 1000  # microseconds

# Driver metadata keys copied into each sweep frame's per-image JSON: the
# exposure/gain actually applied plus every thermal and black-level signal
# the sensor reports. Missing keys are recorded as null so files stay
# comparable across camera types.
SWEEP_FRAME_METADATA_KEYS = (
    "ExposureTime",
    "AnalogueGain",
    "DigitalGain",
    "SensorTemperature",
    "SensorBlackLevels",
    "ColourGains",
    "Lux",
    "FrameDuration",
)


def _json_safe(value):
    """Coerce picamera2 metadata values (numpy scalars, tuples) to JSON types."""
    if isinstance(value, dict):
        return {str(k): _json_safe(v) for k, v in value.items()}
    if isinstance(value, (tuple, list)):
        return [_json_safe(v) for v in value]
    if isinstance(value, np.integer):
        return int(value)
    if isinstance(value, np.floating):
        return float(value)
    if isinstance(value, (str, int, float, bool)) or value is None:
        return value
    return str(value)


def sweep_frame_record(index, exp_us, driver_metadata, cropped_frame, bit_depth):
    """Build one sweep image's metadata record: the camera settings actually
    applied (from driver metadata) plus ADU statistics of the raw frame
    (pre-bias-subtraction).

    The statistics cover the square crop, while the TIFF alongside holds the
    whole sensor. Keeping them on the crop is what makes the black-level
    series comparable with sweeps taken before the archive went full-sensor."""
    camera_metadata = {
        key: _json_safe(driver_metadata.get(key)) if driver_metadata else None
        for key in SWEEP_FRAME_METADATA_KEYS
    }
    record = {
        "index": index,
        "requested_exposure_us": exp_us,
        "exp_ms": exp_us / 1000,
        "sensor_temp_c": camera_metadata["SensorTemperature"],
        "captured_at": timez.local_now().isoformat(),
        "camera_metadata": camera_metadata,
        # Entire driver dict, uncurated: sensors differ in which keys they
        # report (and under what names/types); archived sweeps must not be
        # limited to today's whitelist when characterizing a new camera.
        "camera_metadata_full": (
            _json_safe(driver_metadata) if driver_metadata else None
        ),
    }
    if cropped_frame is not None:
        frame = cropped_frame.astype(np.float64)
        p = np.percentile(frame, [1, 5, 25, 50, 75, 95, 99])
        record["raw_stats"] = {
            # Which pixels these numbers cover. The sibling TIFF is
            # full-sensor, so without this the two would silently be
            # assumed to describe the same pixels. Sweeps from before the
            # archive went full-sensor have no such key; there the TIFF
            # was the crop too, so it meant the same thing either way.
            "extent": "crop",
            "mean_adu": float(frame.mean()),
            "median_adu": float(p[3]),
            "std_adu": float(frame.std()),
            "min_adu": float(frame.min()),
            "max_adu": float(frame.max()),
            "percentiles_adu": {
                "p01": float(p[0]),
                "p05": float(p[1]),
                "p25": float(p[2]),
                "p75": float(p[4]),
                "p95": float(p[5]),
                "p99": float(p[6]),
            },
        }
        if bit_depth:
            record["raw_stats"]["saturated_fraction"] = float(
                np.mean(cropped_frame >= 2**bit_depth - 1)
            )
    return record


# Software rotation applied to each raw capture before it reaches the solver
# and the preview, keyed by screen_direction. Each entry is paired with that
# variant's q_imu2cam in pointing_model/imu_dead_reckoning.py -- the camera
# frame ("image up") is only defined after this rotation, so the two values
# must be derived together (see pointing_model/docs/imu2cam_tool.html).
# Variants absent here fall back to 270.
SCREEN_ROTATE_AMOUNTS = {
    "flat": 270,
    "left": 270,
    "right": 90,
    "straight": 90,
    "flat3": 90,
    "as_bloom": 90,
    "as_heart": 90,
    "rev4_left": 0,
    "rev4_right": 270,
    "rev4_straight": 270,
}


class CameraInterface:
    """The CameraInterface interface."""

    _camera_started = False
    _save_next_to = None  # Filename to save next capture to (None = don't save)
    _auto_exposure_enabled = False
    _auto_exposure_mode = "pid"  # "pid" or "snr"
    _auto_exposure_pid: Optional[ExposurePIDController] = None
    _auto_exposure_snr: Optional[ExposureSNRController] = None
    _last_solve_time: Optional[float] = None
    # Native (camera-driver) auto-exposure, distinct from the solver-driven
    # auto-exposure above. Enabled for daytime alignment via `set_exp:native`.
    _native_ae_enabled = False
    # Handle to an in-flight capture thread (see _capture_with_timeout). A
    # wedged V4L2 capture can outlive its timeout; tracking it lets the next
    # frame decline to start a second, concurrent capture on a camera that is
    # not thread-safe.
    _capture_thread: Optional[threading.Thread] = None

    def set_native_ae(self, enabled: bool) -> bool:
        """Enable/disable the camera's native (driver) auto-exposure.

        Returns True if the backend actually supports native AE; False otherwise
        (the caller then falls back to a fixed short exposure). The base
        implementation has no native AE.
        """
        return False

    def initialize(self) -> None:
        pass

    def capture(self) -> Image.Image:
        return Image.Image()

    def capture_file(self, filename) -> None:
        pass

    def capture_raw_file(self, filename) -> None:
        pass

    def _settle_exposure(self, requested_us, max_frames=8, tolerance=0.02):
        """Discard frames until the sensor actually delivers `requested_us`.

        A fixed flush count cannot be right for every sensor: the IMX290/462
        serves exactly three frames at the old exposure after a change, while
        the IMX477 emits half-exposure transitional frames instead. Flushing
        two frames -- as this did -- left the next capture still on the old
        exposure, so a sweep's processed PNG was one step behind the raw TIFF
        beside it, and the radiometer sample attached to the record described
        the PNG. Watch the driver's reported ExposureTime instead.

        Returns the number of frames discarded.
        """
        for n in range(max_frames):
            self.capture()
            meta = getattr(self, "last_frame_metadata", None) or {}
            actual = meta.get("ExposureTime")
            if actual is None:
                # Backend reports no exposure metadata (debug/none cameras);
                # nothing to settle against, so don't burn frames on it.
                return n + 1
            if abs(float(actual) - requested_us) <= tolerance * requested_us:
                return n + 1
        logger.warning(
            "Exposure did not settle at %sµs after %d frames; "
            "the frame may not match its label",
            requested_us,
            max_frames,
        )
        return max_frames

    def _blank_capture(self):
        """
        Returns a properly formated black frame
        """
        return Image.new("L", (512, 512), 0)  # Black 512x512 image

    def _capture_with_timeout(self, timeout=10) -> Optional[Image.Image]:
        """Run capture() with a timeout, never overlapping two captures.

        A V4L2 capture can hang indefinitely (e.g. the sensor wedges), which
        would otherwise freeze the whole camera process. Run the capture on a
        daemon thread and give up after ``timeout`` seconds, returning None so
        the caller can recover instead of blocking forever.

        A timed-out capture cannot be cancelled (picamera2/V4L2 exposes no such
        API), so the daemon thread stays stuck inside the driver until it
        eventually returns. To avoid piling concurrent capture_request() calls
        onto a camera that is not thread-safe -- and racing on shared camera
        state -- we keep a handle to the in-flight thread and refuse to launch a
        second capture while it is still alive. At most one capture is ever
        running; the caller just gets blank frames until the stuck one clears.
        """
        # A previous capture is still wedged in the driver -- don't start a
        # second one. Returning None lets the caller fall back to a blank frame
        # while we wait for the stuck capture to clear.
        if self._capture_thread is not None and self._capture_thread.is_alive():
            return None

        result: list = [None]
        exc: list = [None]

        def _do_capture():
            try:
                result[0] = self.capture()
            except Exception as e:  # propagate to the caller's thread
                exc[0] = e

        thread = threading.Thread(target=_do_capture, daemon=True)
        self._capture_thread = thread
        thread.start()
        thread.join(timeout)

        if thread.is_alive():
            # Still running: leave it tracked so the next call sees it and
            # declines to start an overlapping capture.
            return None

        # Finished within the timeout -- clear the handle so the next frame
        # starts a fresh capture.
        self._capture_thread = None
        if exc[0]:
            raise exc[0]
        return result[0]

    def capture_bias(self):
        """
        Capture a bias frame for pedestal calculation.
        Base implementation returns a black frame (no bias correction).
        Override in subclasses that support bias frames.
        Returns Image.Image or np.ndarray depending on implementation.
        """
        return self._blank_capture()

    def set_camera_config(
        self, exposure_time: float, gain: float
    ) -> Tuple[float, float]:
        return (0, 0)

    def get_cam_type(self) -> str:
        return "foo"

    def optical_train_known(self) -> bool:
        """Whether these frames came through this device's own optics.

        True for anything pointed at the sky, which is why it defaults that
        way: a camera has to opt *out*, so a new hardware backend inherits the
        FOV gate rather than silently losing it.

        False is an **unknown optical train** (docs/ax/camera/CONTEXT.md): the
        frames were captured through some other train, so the resolved one
        describes this machine and not them. Two things follow, both handled
        by the consumers rather than here -- the solver asserts no FOV gate,
        and lens self-heal declines to infer a lens from a fitted FOV that
        measured a recording. See docs/adr/0029.
        """
        return True

    def start_camera(self) -> None:
        pass

    def stop_camera(self) -> None:
        pass

    def get_image_loop(
        self, shared_state, camera_image, command_queue, console_queue, cfg
    ):
        try:
            # Store shared_state for access by capture() methods
            self.shared_state = shared_state

            # Store camera type in shared state for SQM calibration
            camera_type_str = self.get_cam_type()  # e.g., "PI imx296", "PI hq"
            if " " in camera_type_str:
                # Extract just the sensor type (imx296, hq, imx462, etc.)
                camera_type = camera_type_str.split(" ")[1].lower()
                shared_state.set_camera_type(camera_type)
                logger.info(f"Camera type set to: {camera_type}")

            # Published beside the sensor because it qualifies it: the sensor
            # a playback camera declares is the one its *frames* were shot on,
            # which is not the same claim a live camera makes.
            train_known = self.optical_train_known()
            shared_state.set_optical_train_known(train_known)
            if not train_known:
                logger.info(
                    "Optical train is unknown: these frames did not come "
                    "through this device's optics, so the solver gets no FOV "
                    "gate and the lens cannot self-heal from them"
                )

            # Check if auto-exposure was previously enabled in config
            config_exp = cfg.get_option("camera_exp")
            if config_exp == "auto":
                self._auto_exposure_enabled = True
                self._last_solve_time = None
                if self._auto_exposure_pid is None:
                    self._auto_exposure_pid = ExposurePIDController()
                else:
                    self._auto_exposure_pid.reset()
                logger.info("Auto-exposure mode enabled from config")

            screen_direction = cfg.get_option("screen_direction")
            camera_rotation = cfg.get_option("camera_rotation")

            # Publish the display rotation applied to the solve image (PIL
            # CCW degrees, relative to the stored raw frame) so SQM can map
            # solve-image centroids back onto the raw for photometry.
            if camera_rotation is not None:
                solve_rotation = (-int(camera_rotation)) % 360
            else:
                solve_rotation = SCREEN_ROTATE_AMOUNTS.get(screen_direction, 270)
            shared_state.set_solve_image_rotation(solve_rotation)

            # Set path for test mode image
            root_dir = os.path.realpath(
                os.path.join(os.path.dirname(__file__), "..", "..")
            )
            test_image_path = os.path.join(
                root_dir, "test_images", "pifinder_debug_02.png"
            )

            # 60 half-second cycles (30 seconds between captures in sleep mode)
            sleep_delay = 60
            was_sleeping = False
            test_mode_on = False
            while True:
                sleeping = state_utils.sleep_for_framerate(
                    shared_state, limit_framerate=False
                )
                if sleeping:
                    # Log transition to sleep mode
                    if not was_sleeping:
                        logger.info("Camera entering low-power sleep mode")
                        was_sleeping = True
                    # Even in sleep mode, we want to take photos every
                    # so often to update positions
                    sleep_delay -= 1
                    if sleep_delay > 0:
                        continue
                    else:
                        sleep_delay = 60
                        logger.debug("Sleep mode: waking for periodic capture")
                elif was_sleeping:
                    logger.info("Camera exiting low-power sleep mode")
                    was_sleeping = False

                imu_start = shared_state.imu()
                image_start_time = time.time()
                if self._camera_started:
                    if not test_mode_on:
                        base_image = self._capture_with_timeout()
                        if base_image is None:
                            # Capture hung; fall back to a blank frame so the
                            # loop keeps running and stays responsive to
                            # commands instead of freezing. The blank frame
                            # simply fails to solve.
                            logger.warning("Camera capture timed out; blank frame")
                            base_image = self._blank_capture()
                        base_image = base_image.convert("L")

                        base_image = base_image.rotate(solve_rotation)
                    else:
                        # Test Mode: load image from disc and wait
                        # No real raw matrix backs this frame; prevent a recent
                        # hardware radiometer sample from being paired with it.
                        shared_state.set_sqm_radiometer_sample(None)
                        base_image = Image.open(test_image_path)
                        base_image = base_image.convert(
                            "L"
                        )  # Convert to grayscale to match camera output
                        time.sleep(0.2)
                    image_end_time = time.time()
                    # check imu to make sure we're still static
                    imu_end = shared_state.imu()

                    # see if we moved during exposure
                    if imu_start and imu_end:
                        # Returns the pointing difference between successive IMU quaternions as
                        # an angle (radians). Note that this also accounts for rotation around the
                        # scope axis. Returns an angle in radians.
                        pointing_diff = qt.get_quat_angular_diff(
                            imu_start.quat, imu_end.quat
                        )
                    else:
                        pointing_diff = 0.0

                    # Make image available
                    if test_mode_on and abs(pointing_diff) > 0.01:
                        # Scope moved during the fake exposure: return a blank
                        # image so the solver doesn't report a stale solve
                        camera_image.paste(self._blank_capture())
                    else:
                        camera_image.paste(base_image)
                    image_metadata = {
                        "exposure_start": image_start_time,
                        "exposure_end": image_end_time,
                        "imu": imu_end,
                        "imu_delta": np.rad2deg(pointing_diff),
                        "exposure_time": self.exposure_time,
                        "actual_exposure_us": (
                            getattr(self, "last_frame_metadata", None) or {}
                        ).get("ExposureTime"),
                        "gain": self.gain,
                        "sensor_temp_c": getattr(self, "last_sensor_temp", None),
                    }
                    shared_state.set_last_image_metadata(image_metadata)

                    # Auto-exposure: adjust based on plate solve results
                    # Updates as fast as new solve results arrive (naturally rate-limited)
                    if self._auto_exposure_enabled and self._auto_exposure_pid:
                        solution = shared_state.solution()
                        solve_source = solution.solve_source if solution else None

                        # Handle camera solves (successful or failed)
                        if solve_source in ("CAM", "CAM_FAILED"):
                            matched_stars = solution.diagnostics.Matches
                            solve_attempt_time = solution.last_solve_attempt
                            solve_rmse = solution.diagnostics.RMSE

                            # Only update on NEW solve results (not re-processing same solution)
                            # Use last_solve_attempt since it's set for both success and failure
                            if (
                                solve_attempt_time
                                and solve_attempt_time != self._last_solve_time
                            ):
                                rmse_str = (
                                    f"{solve_rmse:.1f}"
                                    if solve_rmse is not None
                                    else "N/A"
                                )
                                logger.debug(
                                    f"Auto-exposure feedback - Stars: {matched_stars}, "
                                    f"RMSE: {rmse_str}, Current exposure: {self.exposure_time}µs"
                                )

                                # Call auto-exposure update based on current mode
                                if self._auto_exposure_mode == "snr":
                                    # SNR mode: use background-based controller (for SQM measurements)
                                    if self._auto_exposure_snr is None:
                                        # Default 8-bit thresholds; the
                                        # controller measures the processed
                                        # display image.
                                        self._auto_exposure_snr = (
                                            ExposureSNRController()
                                        )
                                    # The controller sees the processed 8-bit
                                    # image, so this must remain in 8-bit ADU.
                                    processed_noise_floor = (
                                        self.shared_state.noise_floor()
                                    )
                                    new_exposure = self._auto_exposure_snr.update(
                                        self.exposure_time,
                                        base_image,
                                        noise_floor=processed_noise_floor,
                                    )
                                else:
                                    # PID mode: use star-count based controller (default)
                                    new_exposure = self._auto_exposure_pid.update(
                                        matched_stars, self.exposure_time
                                    )

                                if (
                                    new_exposure is not None
                                    and new_exposure != self.exposure_time
                                ):
                                    # Exposure value actually changed - update camera
                                    logger.info(
                                        f"Auto-exposure adjustment: {matched_stars} stars → "
                                        f"{self.exposure_time}µs → {new_exposure}µs "
                                        f"(change: {new_exposure - self.exposure_time:+d}µs)"
                                    )
                                    self.exposure_time = new_exposure
                                    self.set_camera_config(
                                        self.exposure_time, self.gain
                                    )
                                elif new_exposure is None:
                                    logger.debug(
                                        f"Auto-exposure: {matched_stars} stars, no adjustment needed"
                                    )
                                self._last_solve_time = solve_attempt_time

                # Loop over any pending commands
                # There may be more than one!
                command = True
                while command:
                    try:
                        command = command_queue.get(block=True, timeout=0.1)
                    except queue.Empty:
                        command = ""
                        continue
                    except Exception as e:
                        logger.error(f"CameraInterface: Command error: {e}")

                    try:
                        if command == "debug":
                            test_mode_on = not test_mode_on

                        if command.startswith("set_exp"):
                            transient_exposure = command.startswith(
                                "set_exp_transient:"
                            )
                            exp_value = command.split(":")[1]
                            if exp_value == "auto":
                                # Enable auto-exposure mode
                                self._auto_exposure_enabled = True
                                self._native_ae_enabled = False
                                self._last_solve_time = None  # Reset solve tracking
                                if self._auto_exposure_pid is None:
                                    self._auto_exposure_pid = ExposurePIDController()
                                else:
                                    self._auto_exposure_pid.reset()
                                console_queue.put("CAM: Auto-Exposure Enabled")
                                logger.info("Auto-exposure mode enabled")
                            elif exp_value == "native":
                                # Native (driver) auto-exposure for daytime align.
                                # Disable the solver-driven AE so it doesn't fight
                                # the driver; leave the saved camera_exp config
                                # untouched so the prior mode can be restored.
                                self._auto_exposure_enabled = False
                                self._last_solve_time = None
                                if self.set_native_ae(True):
                                    self._native_ae_enabled = True
                                    console_queue.put("CAM: Native AE")
                                    logger.info("Native auto-exposure enabled")
                                else:
                                    # No native AE on this backend (debug / non-Pi):
                                    # fall back to a fixed short daylight exposure.
                                    self._native_ae_enabled = False
                                    self.exposure_time = DAYTIME_AE_FALLBACK_EXPOSURE
                                    self.set_camera_config(
                                        self.exposure_time, self.gain
                                    )
                                    console_queue.put("CAM: Day exposure")
                                    logger.info(
                                        "Native AE unsupported; fixed exposure "
                                        f"{self.exposure_time}µs"
                                    )
                            else:
                                # Disable auto-exposure and set manual exposure.
                                # set_camera_config also clears native AE on Pi.
                                self._auto_exposure_enabled = False
                                self._native_ae_enabled = False
                                self.exposure_time = int(exp_value)
                                self.set_camera_config(self.exposure_time, self.gain)
                                # Calibration uses transient manual exposures;
                                # never persist those over the user's saved
                                # auto/manual choice.
                                if not transient_exposure:
                                    cfg.set_option("camera_exp", self.exposure_time)
                                console_queue.put("CAM: Exp=" + str(self.exposure_time))
                                logger.info(
                                    f"Manual exposure set: {self.exposure_time}µs"
                                )

                        if command.startswith("set_gain"):
                            old_gain = self.gain
                            self.gain = int(command.split(":")[1])
                            self.exposure_time, self.gain = self.set_camera_config(
                                self.exposure_time, self.gain
                            )
                            console_queue.put("CAM: Gain=" + str(self.gain))
                            logger.info(f"Gain changed: {old_gain}x → {self.gain}x")

                        if command.startswith("set_ae_mode"):
                            mode = command.split(":")[1]
                            if mode in ["pid", "snr"]:
                                self._auto_exposure_mode = mode
                                console_queue.put(f"CAM: AE Mode={mode.upper()}")
                                logger.info(
                                    f"Auto-exposure mode changed to: {mode.upper()}"
                                )
                            else:
                                logger.warning(
                                    f"Unknown auto-exposure mode: {mode} (valid: pid, snr)"
                                )

                        if command == "exp_up" or command == "exp_dn":
                            # Manual exposure adjustments disable auto-exposure
                            # (both solver-driven and native; set_camera_config
                            # also clears native AeEnable on Pi).
                            self._auto_exposure_enabled = False
                            self._native_ae_enabled = False
                            if command == "exp_up":
                                self.exposure_time = int(self.exposure_time * 1.25)
                            else:
                                self.exposure_time = int(self.exposure_time * 0.75)
                            self.set_camera_config(self.exposure_time, self.gain)
                            console_queue.put("CAM: Exp=" + str(self.exposure_time))
                        if command == "exp_save":
                            # Saving exposure disables auto-exposure and locks to current value
                            self._auto_exposure_enabled = False
                            cfg.set_option("camera_exp", self.exposure_time)
                            cfg.set_option("camera_gain", int(self.gain))
                            console_queue.put(
                                f"CAM: Exp Saved ({self.exposure_time}µs)"
                            )
                            logger.info(
                                f"Exposure saved and auto-exposure disabled: {self.exposure_time}µs"
                            )

                        if command.startswith("save_image:"):
                            # Save current camera frame to specified path
                            save_path = command.split(":", 1)[1]
                            try:
                                img = camera_image.copy()
                                img.save(save_path, "PNG", compress_level=6)
                                logger.debug("Telemetry image saved: %s", save_path)
                            except Exception as e:
                                logger.error("Failed to save telemetry image: %s", e)

                        if command.startswith("save:"):
                            # Set flag to save next capture to this file
                            self._save_next_to = command.split(":", 1)[1]
                            console_queue.put("CAM: Save flag set")

                        if (
                            command.startswith("capture")
                            and command != "capture_exp_sweep"
                        ):
                            # Capture one identified frame. Calibration waits on
                            # this timestamp, preventing it from analysing the
                            # preceding continuously captured frame.
                            capture_imu_start = shared_state.imu()
                            capture_start = time.time()
                            captured_image = self.capture().convert("L")
                            captured_image = captured_image.rotate(solve_rotation)
                            captured_raw = None
                            if self._save_next_to:
                                captured_raw = shared_state.cam_raw()
                                if captured_raw is not None:
                                    captured_raw = captured_raw.copy()
                            camera_image.paste(captured_image)
                            capture_end = time.time()
                            capture_imu_end = shared_state.imu()
                            if capture_imu_start and capture_imu_end:
                                capture_pointing_diff = qt.get_quat_angular_diff(
                                    capture_imu_start.quat,
                                    capture_imu_end.quat,
                                )
                            else:
                                capture_pointing_diff = 0.0
                            shared_state.set_last_image_metadata(
                                {
                                    "exposure_start": capture_start,
                                    "exposure_end": capture_end,
                                    "imu": capture_imu_end,
                                    "imu_delta": np.rad2deg(capture_pointing_diff),
                                    "exposure_time": self.exposure_time,
                                    "actual_exposure_us": (
                                        getattr(self, "last_frame_metadata", None) or {}
                                    ).get("ExposureTime"),
                                    "gain": self.gain,
                                    "sensor_temp_c": getattr(
                                        self, "last_sensor_temp", None
                                    ),
                                }
                            )

                            # If save flag is set, save to disk
                            if self._save_next_to:
                                requested_path = Path(self._save_next_to)
                                if not requested_path.is_absolute():
                                    requested_path = (
                                        Path(utils.data_dir)
                                        / "captures"
                                        / requested_path
                                    )
                                filename = requested_path.with_suffix(".png")
                                filename.parent.mkdir(parents=True, exist_ok=True)

                                # Save the identified capture itself. Calling
                                # capture_file()/capture_raw_file() here would
                                # acquire different frames and break pairing.
                                captured_image.save(filename)
                                if captured_raw is not None:
                                    Image.fromarray(captured_raw).save(
                                        filename.with_suffix(".tiff")
                                    )

                                console_queue.put("CAM: Captured + Saved")
                                self._save_next_to = None  # Clear flag
                            else:
                                console_queue.put("CAM: Captured")

                        if command.startswith("capture_exp_sweep"):
                            # Capture exposure sweep - save both RAW and processed images
                            # at different exposures for SQM testing
                            # RAW: 16-bit TIFF to preserve full sensor bit depth
                            # Processed: 8-bit PNG from normal camera.capture() pipeline

                            # Parse reference SQM if provided
                            reference_sqm = None
                            if ":" in command:
                                try:
                                    reference_sqm = float(command.split(":")[1])
                                    logger.info(f"Reference SQM: {reference_sqm:.2f}")
                                except (ValueError, IndexError):
                                    logger.warning("Invalid reference SQM in command")

                            logger.info(
                                "Starting exposure sweep capture (20 image pairs)"
                            )
                            console_queue.put("CAM: Starting sweep...")

                            # Save current settings
                            original_exposure = self.exposure_time
                            original_gain = self.gain
                            original_ae_enabled = self._auto_exposure_enabled

                            # Disable auto-exposure during sweep
                            self._auto_exposure_enabled = False

                            # Generate 20 exposure values with logarithmic spacing
                            # from 25ms (25000µs) to 1s (1000000µs)
                            min_exp = 25000  # 25ms
                            max_exp = 1000000  # 1s
                            num_images = 20

                            # Generate logarithmic sweep using shared utility
                            sweep_exposures = generate_exposure_sweep(
                                min_exp, max_exp, num_images
                            )
                            # Capture in random order: a monotonic ramp lets any
                            # temporal sky drift (twilight, passing haze) alias
                            # into an apparent exposure dependence in analysis.
                            # Each file name carries its exposure, so order is
                            # irrelevant downstream.
                            random.shuffle(sweep_exposures)
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
